Julesc013/abacus-2/hardware/video/video_adapter/CDA Code Pages New.pdf

0 | 1 | 2 | 3 | 4 | 5 | 6 | 7 | 8 | 9 | A | B | C | D | E
0x | Α Β Γ Δ Ε Ζ Η Θ Ι Κ û Μ Ν Ξ
1x | Π Ρ | ⁊ | Σ Τ Υ Φ Χ Ψ Ω ℥ ⟨ ‹ ⟩ ›
2x | | ! | " | # | $ | % | & | ' | ( | ) | * | + | , | - | .
3x | 0 | 1 | 2 | 3 | 4 | 5 | 6 | 7 | 8 | 9 | : | ; | < | = | >
4x | @ | A | B | C | D | E | F | G | H | I | J | K | L | M | N
5x | P | Q | R | S | T | U | V | W | X | Y | Z | [ | \ | ] | ^
6x | ` | a | b | c | d | e | f | g | h | i | j | k | l | m | n
7x | p | q | r | s | t | u | v | w | x | y | z | { | | | } | ~
8x | € | α | β | γ | δ | ε | ζ | η | θ | ι | κ | λ | μ | ν | ξ
9x | π | ρ | ς | σ | τ | υ | φ | χ | ψ | ω | – | — | … | ℠ | ℗
Ax | | ¡ | ¢ | £ | ¤ | ¥ | ¦ | § | ¨ | © | ª | « | ¬ | ™ | ®
Bx | ° ± ² ³ ´ | µ | ¶ · ¸ ¹ º » ¼ ½ ¾
Cx Dx Ex Fx | À Á Â Ã Ä Å Æ Ç È É Ê Ë Ì Í Î Ð Ñ Ò Ó Ô Õ Ö × Ø Ù Ú Û Ü Ý Þ à á â ã ä å æ ç è é ê ë ì í î ð ñ ò ó ô õ ö ÷ ø ù ú û ü ý þ
0x | † ‡ ℹ | ⁎ | ⁑ ⁂ ※ ∓ | ‸ ⁿ ƒ | ⁋ ⁌ ⁍ ‽
1x | ‰ ‱ ′ ″ ‴ ⁗ | ∂ | ∧ ∨ ∩ ∪ ∫ ∬ ∭ | ℇ
2x 3x | ∠ ∡ ∢ ∟ ⊾ ⅈ ⅉ ∈ ∉ ∥ ∦ ∝ ⌐ √ ∛ ≠ ≡ ≢ ≣ ≔ ∴ ∵ ∷ ⋰ ⋱ ⋮ ⋯ ≤ ≈ ≥
4x | ℕ ℤ ℚ A ℝ I ℂ ∞ | ⌀ ∗ ∘ · | ⊕ ⊖ ⊗
5x | ⅐ | ⅑ ⅒ ⅓ | ⅔ | ⅕ | ⅖ | ⅗ | ⅘ | ⅙ | ⅚ | ⅛ | ⅜ | ⅝ | ⅞
6x | ← | ↑ | → | ↓ ↔ | ↕ | ↖ | ↗ | ↘ | ↙ | ⇐ | ⇋ | ⇒ | ⇌ | ⇔
7x | ◄ | ▲ | ► | ▼ | ☺ ☻ | ♥ | ♦ | ♣ | ♠ | ♂ | ♀ | ♪ | ♫ | ☼
8x | 🮀 | 🮁 | 🮂 | 🮃 | 🮄 | 🮅 | 🮆 | 🮇 | 🮈 | 🮉 | 🮊 | 🮋 | 🮌 | 🮍 | 🮎
9x | 🮐 🮑 🮒 | ■ | 🮔 🮕 🮖 🮗 🮘 🮙 🮚 🮛 🮜 🮝 🮞
Ax Bx | ▀ ▁ ▂ ▃ ▄ ▅ ▆ ▇ █ ▉ ▊ ▋ ▌ ▍ ▎ ▐ ░ ▒ ▓ ▔ ▕ ▖ ▗ ▘ ▙ ▚ ▛ ▜ ▝ ▞
Cx | ─ │ ┌ ┐ └ ┘ ├ ┤ ┬ ┴ ┼ | ‣ • ◘ ○
Dx Ex | ═ ║ ╒ ╓ ╔ ╕ ╖ ╗ ╘ ╙ ╚ ╛ ╜ ╝ ╞ ╠ ╡ ╢ ╣ ╤ ╥ ╦ ╧ ╨ ╩ ╪ ╫ ╬ ╭ ╮
Fx | ╰ ╱ ╲ ╳ | ⌠ ⌡ ∎ | ▬ ╸ ╹ ╺ ╻ | ☑ ☐ 🮰

1

Page

0

F | Block | Page | Block
Ο ₧ | Greek Alphabet (Uppercase) | 0 | 0x – 1x 2x – 7x 8x – 9x Ax – Fx

/ ?

O 0x – 3x _ o ⌂ | Latin Alphabet (ASCII) | 1 | 4x – 7x 8x – Cx Dx – Fx
ο № | Greek Alphabet (Lowercase) | 2 | 0x – 7x 8x – Fx
¯ ¿ Ï | Latin Supplement | 3 | 0x – Bx Cx – Dx Ex – Fx

ß ï ÿ

‼
ℯ | General Punctuation &
∜ ≉ ⊘ | Mathematical Operators
⅟ ⇕ | Supplementary Symbols
↨ | Code Page 437 (Leftovers)
🮏 🮟 | Legacy Elements
▏ ▟ | Block Elements

◙
╟ ╯ | Box Drawing

Points | Notes
Miscellaneous Symbols A Latin Alphabet (ASCII) Miscellaneous Symbols B Latin Supplement
Greek Alphabet Cyrillic Alphabet General Punctuation Supplementary Symbols | Arrows, Fractions, Currency, Roman Numerals

Mathematical Operators Box Drawing

Legacy Elements Block Elements Letterlike Symbols | Symbols for Legacy Computing
