Julesc013/abacus-2/hardware/video/video_adapter/CDA Code Pages.pdf

0 | 1 | 2 | 3 | 4 | 5 | 6 | 7 | 8 | 9 | A | B | C | D | E | F | U+ | Block
0x 1x 2x 3x 4x 5x 6x 7x 0 8x 9x Ax Bx Cx Dx Ex Fx | NUL SOH STX ETX EOT ENQ ACK BEL BS HT LF VT FF CR SO SI DLE DC1 DC2 DC3 DC4 NAK SYN ETB CAN EM SUB ESC FS GS RS US | 000x C0 Controls 001x
| SP ! " # $ % & ' ( ) * + , -. / 0 1 2 3 4 5 6 7 8 9 : ; < = > ? @ A B C D E F G H I J K L M N O P Q R S T U V W X Y Z [ \ ] ^ _ ` a b c d e f g h i j k l m n o p q r s t u v w x y z { | } ~ DEL | 002x 003x 004x Basic Latin 005x 006x 007x
| XXX XXX BPH NBH IND NEL SSA ESA HTS HTJ VTS PLD PLU RI SS2 SS3 DCS PU1 PU2 STS CCH MW SPA EPA SOS XXX SCI CSI ST OSC PM APC | 008x C1 Controls 009x
| NBSP ¡ ¢ £ ¤ ¥ ¦ § ¨ © ª « ¬ SHY ® ¯ ° ± ² ³ ´ µ ¶ · ¸ ¹ º » ¼ ½ ¾ ¿ À Á Â Ã Ä Å Æ Ç È É Ê Ë Ì Í Î Ï Ð Ñ Ò Ó Ô Õ Ö × Ø Ù Ú Û Ü Ý Þ ß à á â ã ä å æ ç è é ê ë ì í î ï ð ñ ò ó ô õ ö ÷ ø ù ú û ü ý þ ÿ | 00Ax 00Bx 00Cx Latin-1 Supplement 00Dx 00Ex 00Fx
0x 1x 2x 3x 4x 5x 6x 7x 1 8x 9x Ax Bx Cx Dx Ex Fx | Ѐ Ё Ђ Ѓ Є Ѕ І Ї Ј Љ Њ Ћ Ќ Ѝ Ў Џ А Б В Г Д Е Ж З И Й К Л М Н О П Р С Т У Ф Х Ц Ч Ш Щ Ъ Ы Ь Э Ю Я а б в г д е ж з и й к л м н о п р с т у ф х ц ч ш щ ъ ы ь э ю я ѐ ё ђ ѓ є ѕ і ї ј љ њ ћ ќ ѝ ў џ Ѡ ѡ Ѣ ѣ Ѥ ѥ Ѧ ѧ Ѩ ѩ Ѫ ѫ Ѭ ѭ Ѯ ѯ Ѱ ѱ Ѳ ѳ Ѵ ѵ Ѷ ѷ Ѹ ѹ Ѻ ѻ Ѽ ѽ Ѿ ѿ | 040x 041x 042x 043x Cyrillic 044x 045x 046x 047x
| ΄ ΅ Ά · Έ Ή Ί Ό Ύ Ώ ΐ Α Β Γ Δ Ε Ζ Η Θ Ι Κ Λ Μ Ν Ξ Ο Π Ρ Σ Τ Υ Φ Χ Ψ Ω Ϊ Ϋ ά έ ή ί ΰ α β γ δ ε ζ η θ ι κ λ μ ν ξ ο π ρ ς σ τ υ φ χ ψ ω ϊ ϋ ό ύ ώ Ϗ ϐ ϑ ϒ ϓ ϔ ϕ ϖ ϗ Ϙ ϙ Ϛ ϛ Ϝ ϝ Ϟ ϟ Ϡ ϡ Ϣ ϣ Ϥ ϥ Ϧ ϧ Ϩ ϩ Ϫ ϫ Ϭ ϭ Ϯ ϯ ϰ ϱ ϲ ϳ ϴ ϵ ϶ Ϸ ϸ Ϲ Ϻ ϻ ϼ Ͻ Ͼ Ͽ | 038x 039x 03Ax 03Bx Greek and Coptic 03Cx 03Dx 03Ex 03Fx
0x 1x 2x 3x 4x 5x 6x 7x 2 8x 9x Ax Bx Cx Dx Ex Fx | IDSP 、 。 〃 〄 々 〆 〇 〈 〉 《 》 「 」 『 』 【 】 〒 〓 〔 〕 〖 〗 〘 〙 〚 〛 〜 〝 〞 〟 〠 〡 〢 〣 〤 〥 〦 〧 〨 〩 〪 〫 〬 〭 〮 〯 〰 〱 〲 〳 〴 〵 〶 〷 〸 〹 〺 〻 〼 〽 〾 〿 | 300x 301x CJK Symbols and Punctuation 302x 303x
| ぁ あ ぃ い ぅ う ぇ え ぉ お か が き ぎ く ぐ け げ こ ご さ ざ し じ す ず せ ぜ そ ぞ た だ ち ぢ っ つ づ て で と ど な に ぬ ね の は ば ぱ ひ び ぴ ふ ぶ ぷ へ べ ぺ ほ ぼ ぽ ま み む め も ゃ や ゅ ゆ ょ よ ら り る れ ろ ゎ わ ゐ ゑ を ん ゔ ゕ ゖ ゙◌ ゚◌ ゛ ゜ ゝ ゞ ゟ | 304x 305x 306x Hiragana 307x 308x 309x
| ゠ ァ ア ィ イ ゥ ウ ェ エ ォ オ カ ガ キ ギ ク グ ケ ゲ コ ゴ サ ザ シ ジ ス ズ セ ゼ ソ ゾ タ ダ チ ヂ ッ ツ ヅ テ デ ト ド ナ ニ ヌ ネ ノ ハ バ パ ヒ ビ ピ フ ブ プ ヘ ベ ペ ホ ボ ポ マ ミ ム メ モ ャ ヤ ュ ユ ョ ヨ ラ リ ル レ ロ ヮ ワ ヰ ヱ ヲ ン ヴ ヵ ヶ ヷ ヸ ヹ ヺ ・ ー ヽ ヾ ヿ | 30Ax 30Bx 30Cx Katakana 30Dx 30Ex 30Fx
0x 1x 2x 3x 4x 5x 6x 7x 3 8x 9x Ax Bx Cx Dx Ex Fx | ─ ━ │ ┃ ┄ ┅ ┆ ┇ ┈ ┉ ┊ ┋ ┌ ┍ ┎ ┏ ┐ ┑ ┒ ┓ └ ┕ ┖ ┗ ┘ ┙ ┚ ┛ ├ ┝ ┞ ┟ ┠ ┡ ┢ ┣ ┤ ┥ ┦ ┧ ┨ ┩ ┪ ┫ ┬ ┭ ┮ ┯ ┰ ┱ ┲ ┳ ┴ ┵ ┶ ┷ ┸ ┹ ┺ ┻ ┼ ┽ ┾ ┿ ╀ ╁ ╂ ╃ ╄ ╅ ╆ ╇ ╈ ╉ ╊ ╋ ╌ ╍ ╎ ╏ ═ ║ ╒ ╓ ╔ ╕ ╖ ╗ ╘ ╙ ╚ ╛ ╜ ╝ ╞ ╟ ╠ ╡ ╢ ╣ ╤ ╥ ╦ ╧ ╨ ╩ ╪ ╫ ╬ ╭ ╮ ╯ ╰ ╱ ╲ ╳ ╴ ╵ ╶ ╷ ╸ ╹ ╺ ╻ ╼ ╽ ╾ ╿ | 250x 251x 252x 253x Box Drawing 254x 255x 256x 257x
| ▀ ▁ ▂ ▃ ▄ ▅ ▆ ▇ █ ▉ ▊ ▋ ▌ ▍ ▎ ▏ ▐ ░ ▒ ▓ ▔ ▕ ▖ ▖ ▖ ▖ ▖ ▖ ▖ ▖ ▖ ▖ | 258x Block Elements 259x
| ■ □ ▢ ▣ ▤ ▥ ▦ ▧ ▨ ▩ ▪ ▫ ▬ ▭ ▮ ▯ ▰ ▱ ▲ △ ▴ ▵ ▶ ▷ ▸ ▹ ► ▻ ▼ ▽ ▾ ▿ ◀ ◁ ◂ ◃ ◄ ◅ ◆ ◇ ◈ ◉ ◊ ○ ◌ ◍ ◎ ● ◐ ◑ ◒ ◓ ◔ ◕ ◖ ◗ ◘ ◙ ◚ ◛ ◜ ◝ ◞ ◟ ◠ ◡ ◢ ◣ ◤ ◥ ◦ ◧ ◨ ◩ ◪ ◫ ◬ ◭ ◮ ◯ ◰ ◱ ◲ ◳ ◴ ◵ ◶ ◷ ◸ ◹ ◺ ◻ ◼ ◽ ◾ ◿ | 25Ax 25Bx 25Cx Geometric Shapes 25Dx 25Ex 25Fx

Page

0x 1x 2x 3x 4x 5x 6x 7x 4 8x 9x Ax Bx Cx Dx Ex Fx | NQSP MQSP ENSP EMSP 3/MSP 4/MSP 6/MSP FSP PSP THSP HSP ZWSP ZWNJ ZW J LRM RLM -NB ‒ – — ― ‖ ‗ ‘ ’ ‚ ‛ “ ” „ ‟ † ‡ • ‣ ․ ‥ … ‧ LSEP PSEP LRE RLE PDF LRO RLO NNBSP ‰ ‱ ′ ″ ‴ ‵ ‶ ‷ ‸ ‹ › ※ ‼ ‽ ‾ ‿ ⁀ ⁁ ⁂ ⁃ ⁄ ⁅ ⁆ ⁇ ⁈ ⁉ ⁊ ⁋ ⁌ ⁍ ⁎ ⁏ ⁐ ⁑ ⁒ ⁓ ⁔ ⁕ ⁖ ⁗ ⁘ ⁙ ⁚ ⁛ ⁜ ⁝ ⁞ MMSP WJ ƒ() × , + LRI RLI FSI PDI ISS ASS IAFS AAFS NADS NODS | 200x 201x 202x 203x General Punctuation 204x 205x 206x
| ▖ ▖ ▖ ▖ ▖ ▖ ▖ ▖ ▖ ▖ ▖ | 244x Optical Character Recognition
| ⸀ ⸁ ⸂ ⸃ ⸄ ⸅ ⸆ ⸇ ⸈ ⸉ ⸊ ⸋ ⸌ ⸍ ⸎ ⸒ ⸓ ⸔ ⸕ ⸖ ⸗ ⸘ ⸙ ⸚ ⸛ ⸜ ⸝ ⸞ ⸟ ⸠ ⸡ ⸢ ⸣ ⸤ ⸥ ⸦ ⸧ ⸨ ⸩ ⸪ ⸫ ⸬ ⸭ ⸮ ⸯ ⸰ ⸱ ⸲ ⸳ ⸴ ⸵ ⸶ ⸷ ⸸ ⸹ 2M⸺ 3M⸻ ⸼ ⸽ ⸾ ⸿ ⹀ ⹁ ⹂ ⹃ ⹄ ⹅ ⹅ ⹅ ⹅ ⹅ ⹅ ⹅ ⹅ ⹅ ⹅ ⹅ ▖ ▖ ▖ ▖ ▖ ▖ ▖ ▖ ▖ ▖ ▖ ▖ ▖ ▖ | 2E0x 2E1x 2E2x Supplemental Punctuation 2E3x 2E4x 2E5x
0x | ℀ | ℁ | ℂ | ℃ | ℄ | ℅ | ℆ | ℇ | ℈ | ℉ | ℊ | ℋ | ℌ | ℍ | ℎ | ℏ | 210x
1x | ℐ | ℑ | ℒ | ℓ | ℔ | ℕ | № | ℗ | ℘ | ℙ | ℚ | ℛ | ℜ | ℝ | ℞ | ℟ | 211x
2x | ℠ | ℡ | ™ | ℣ | ℤ | ℥ | Ω | ℧ | ℨ | ℩ | K | Å | ℬ | ℭ | ℮ | ℯ | 212x
3x | ℰ | ℱ | Ⅎ | ℳ | ℴ | ℵ | ℶ | ℷ | ℸ | ℹ | ℺ | ℻ | ℼ | ℽ | ℾ | ℿ | 213x
4x | ⅀ | ⅁ | ⅂ | ⅃ | ⅄ | ⅅ | ⅆ | ⅇ | ⅈ | ⅉ | ⅊ | ⅋ | ⅌ | ⅍ | ⅎ | ⅏ | 214x
5x | ⅐ | ⅑ ⅒ | ⅓ | ⅔ | ⅕ | ⅖ | ⅗ | ⅘ | ⅙ | ⅚ | ⅛ | ⅜ | ⅝ | ⅞ | ⅟ | 215x
6x | Ⅰ | Ⅱ | Ⅲ | Ⅳ | Ⅴ | Ⅵ | Ⅶ | Ⅷ | Ⅸ | Ⅹ | Ⅺ | Ⅻ | Ⅼ | Ⅽ | Ⅾ | Ⅿ | 216x
7x | ⅰ | ⅱ | ⅲ | ⅳ | ⅴ | ⅵ | ⅶ | ⅷ | ⅸ | ⅹ | ⅺ | ⅻ | ⅼ | ⅽ | ⅾ | ⅿ | 217x
8x | ↀ | ↁ | ↂ | Ↄ | ↄ | ↅ | ↆ | ↇ | ↈ | ↉ | ↊ | ↋ | | | | | 218x
9x
Ax | ₠ | ₡ | ₢ | ₣ | ₤ | ₥ | ₦ | ₧ | ₨ | ₩ | ₪ | ₫ | € | ₭ | ₮ | ₯ | 20Ax
Bx | ₰ | ₱ | ₲ | ₳ | ₴ | ₵ | ₶ | ₷ | ₸ | ₹ | ₺ | ₻ | ₼ | ₽ | ₾ | ₿ | 20Bx
Cx
Dx
Ex
Fx
0x 1x 2x 3x 4x 5x 6x 7x 6 Mathematical Operators 8x 9x Ax Bx Cx Dx Ex Fx | ∀ ∁ ∂ ∃ ∄ ∅ ∆ ∇ ∈ ∉ ∊ ∋ ∌ ∍ ∎ ∏ ∐ ∑ − ∓ ∔ ∕ ∖ ∗ ∘ · √ ∛ ∜ ∝ ∞ ∟ ∠ ∡ ∢ ∣ ∤ ∥ ∦ ∧ ∨ ∩ ∪ ∫ ∬ ∭ ∮ ∯ ∰ ∱ ∲ ∳ ∴ ∵ ∶ ∷ ∸ ∹ ∺ ∻ ∼ ∽ ∾ ∿ ≀ ≁ ≂ ≃ ≄ ≅ ≆ ≇ ≈ ≉ ≊ ≋ ≌ ≍ ≎ ≏ ≐ ≑ ≒ ≓ ≔ ≕ ≖ ≗ ≘ ≙ ≚ ≛ ≜ ≝ ≞ ≟ ≠ ≡ ≢ ≣ ≤ ≥ ≦ ≧ ≨ ≩ ≪ ≫ ≬ ≭ ≮ ≯ ≰ ≱ ≲ ≳ ≴ ≵ ≶ ≷ ≸ ≹ ≺ ≻ ≼ ≽ ≾ ≿ ⊀ ⊁ ⊂ ⊃ ⊄ ⊅ ⊆ ⊇ ⊈ ⊉ ⊊ ⊋ ⊌ ⊍ ⊎ ⊏ ⊐ ⊑ ⊒ ⊓ ⊔ ⊕ ⊖ ⊗ ⊘ ⊙ ⊚ ⊛ ⊜ ⊝ ⊞ ⊟ ⊠ ⊡ ⊢ ⊣ ⊤ ⊥ ⊦ ⊧ ⊨ ⊩ ⊪ ⊫ ⊬ ⊭ ⊮ ⊯ ⊰ ⊱ ⊲ ⊳ ⊴ ⊵ ⊶ ⊷ ⊸ ⊹ ⊺ ⊻ ⊼ ⊽ ⊾ ⊿ ⋀ ⋁ ⋂ ⋃ ⋄ ⋅ ⋆ ⋇ ⋈ ⋉ ⋊ ⋋ ⋌ ⋍ ⋎ ⋏ ⋐ ⋑ ⋒ ⋓ ⋔ ⋕ ⋖ ⋗ ⋘ ⋙ ⋚ ⋛ ⋜ ⋝ ⋞ ⋟ ⋠ ⋡ ⋢ ⋣ ⋤ ⋥ ⋦ ⋧ ⋨ ⋩ ⋪ ⋫ ⋬ ⋭ ⋮ ⋯ ⋰ ⋱ ⋲ ⋳ ⋴ ⋵ ⋶ ⋷ ⋸ ⋹ ⋺ ⋻ ⋼ ⋽ ⋾ ⋿ | 220x 221x 222x 223x 224x 225x 226x 227x 228x 229x 22Ax 22Bx 22Cx 22Dx 22Ex 22Fx
0x 1x 2x 3x 4x 5x 6x 7x 7 8x 9x Ax Bx Cx Dx Ex Fx | 🬀 🬁 🬂 🬃 🬄 🬅 🬆 🬇 🬈 🬉 🬊 🬋 🬌 🬍 🬎 🬏 🬐 🬑 🬒 🬓 🬔 🬕 🬖 🬗 🬘 🬙 🬚 🬛 🬜 🬝 🬞 🬟 🬠 🬡 🬢 🬣 🬤 🬥 🬦 🬧 🬨 🬩 🬪 🬫 🬬 🬭 🬮 🬯 🬰 🬱 🬲 🬳 🬴 🬵 🬶 🬷 🬸 🬹 🬺 🬻 🬼 🬽 🬾 🬿 🭀 🭁 🭂 🭃 🭄 🭅 🭆 🭇 🭈 🭉 🭊 🭋 🭌 🭍 🭎 🭏 🭐 🭑 🭒 🭓 🭔 🭕 🭖 🭗 🭘 🭙 🭚 🭛 🭜 🭝 🭞 🭟 🭠 🭡 🭢 🭣 🭤 🭥 🭦 🭧 🭨 🭩 🭪 🭫 🭬 🭭 🭮 🭯 🭰 🭱 🭲 🭳 🭴 🭵 🭶 🭷 🭸 🭹 🭺 🭻 🭼 🭽 🭾 🭿 🮀 🮁 🮂 🮃 🮄 🮅 🮆 🮇 🮈 🮉 🮊 🮋 🮌 🮍 🮎 🮏 🮐 🮑 🮒 🮔 🮕 🮖 🮗 🮘 🮙 🮚 🮛 🮜 🮝 🮞 🮟 🮠 🮡 🮢 🮣 🮤 🮥 🮦 🮧 🮨 🮩 🮪 🮫 🮬 🮭 🮮 🮯 🮰 🮱 🮲 🮳 🮴 🮵 🮶 🮷 🮸 🮹 🮺 🮻 🮼 🮽 🮾 🮿 🯀 🯁 🯂 🯃 🯄 🯅 🯆 🯇 🯈 🯉 🯊 | 1FB0x 1FB1x 1FB2x 1FB3x 1FB4x 1FB5x 1FB6x Symbols for Legacy Computing 1FB7x 1FB8x 1FB9x 1FBAx 1FBBx 1FBCx
| 🜀 🜁 🜂 🜃 🜄 🜅 🜆 🜇 🜈 🜉 🜊 🜋 🜌 🜍 🜎 🜏 🜐 🜑 🜒 🜓 🜔 🜕 🜖 🜗 🜘 🜙 🜚 🜛 🜜 🜝 🜞 🜟 | 1F70x Alchemical Symbols 1F71x
| 🯰 🯱 🯲 🯳 🯴 🯵 🯶 🯷 🯸 🯹 | 1FBFx Symbols for Legacy Computing

5

Letterlike Symbols

Number Forms

Currency Symbols

0x 1x 2x 3x 4x 5x 6x 7x 8 8x 9x Ax Bx Cx Dx Ex Fx | SP ! " # $ % & ' ( ) * + , -. / 0 1 2 3 4 5 6 7 8 9 : ; < = > ? @ A B C D E F G H I J K L M N O P Q R S T U V W X Y Z [ \ ] ^ _ ` a b c d e f g h i j k l m n o p q r s t u v w x y z { | } ~ ± § α β γ δ ε ζ η θ ι κ λ μ ν ξ ο π ρ ς σ τ υ φ χ ψ ω Δ Θ Ξ Π Σ Ω | N/A N/A N/A N/A Superscript Symbols N/A N/A N/A N/A
| SP ! " # $ % & ' ( ) * + , -. / 0 1 2 3 4 5 6 7 8 9 : ; < = > ? @ A B C D E F G H I J K L M N O P Q R S T U V W X Y Z [ \ ] ^ _ ` a b c d e f g h i j k l m n o p q r s t u v w x y z { | } ~ ± § α β γ δ ε ζ η θ ι κ λ μ ν ξ ο π ρ ς σ τ υ φ χ ψ ω Δ Θ Ξ Π Σ Ω | N/A N/A N/A N/A Subscript Symbols N/A N/A N/A N/A
| | Miscellaneous Mathematical Symbols-B
| | Miscellaneous Mathematical Symbols-A
| | Arrows
| | Miscellaneous Symbols and Arrows
| | Miscellaneous Symbols
0x 1x 2x 3x 4x 5x 6x 7x B Miscellaneous Technical 8x 9x Ax Bx Cx Dx Ex Fx | ⌀ ⌁ ⌂ ⌃ ⌄ ⌅ ⌆ ⌇ ⌈ ⌉ ⌊ ⌋ ⌌ ⌍ ⌎ ⌏ ⌐ ⌑ ⌒ ⌓ ⌔ ⌕ ⌖ ⌗ ⌘ ⌙ ⌚ ⌛ ⌜ ⌝ ⌞ ⌟ ⌠ ⌡ ⌢ ⌣ ⌤ ⌥ ⌦ ⌧ ⌨ 〈 〉 ▖ ▖ ▖ ▖ ▖ ⌰ ⌱ ⌲ ⌳ ⌴ ⌵ ⌶ ⌷ ⌸ ⌹ ⌺ ⌻ ⌼ ⌽ ⌾ ⌿ ⍀ ⍁ ⍂ ⍃ ⍄ ⍅ ⍆ ⍇ ⍈ ⍉ ⍊ ⍋ ⍌ ⍍ ⍎ ⍏ ⍐ ⍑ ⍒ ⍓ ⍔ ⍕ ⍖ ⍗ ⍘ ⍙ ⍚ ⍛ ⍜ ⍝ ⍞ ⍟ ⍠ ⍡ ⍢ ⍣ ⍤ ⍥ ⍦ ⍧ ⍨ ⍩ ⍪ ⍫ ⍬ ⍭ ⍮ ⍯ ⍰ ⍱ ⍲ ⍳ ⍴ ⍵ ⍶ ⍷ ⍸ ⍹ ⍺ ⍻ ⍼ ⍽ ⍾ ⍿ ⎀ ⎐ ⎁ ⎑ ⎂ ⎒ ⎃ ⎓ ⎄ ⎔ ⎕ ⎅ ⎆ ⎖ ⎇ ⎗ ⎘ ⎈ ⎙ ⎉ ⎚ ⎊ ⎛ ⎜ ⎝ ⎞ ⎟ ⎋ ⎌ ⎍ ⎎ ⎏ ⎠ ⎡ ⎢ ⎣ ⎤ ⎥ ⎦ ⎧ ⎨ ⎩ ⎪ ⎫ ⎬ ⎭ ⎮ ⎯ ⎰ ⎱ ⎲ ⎳ ⎴ ⎵ ⎶ ⎷ ⎸ ⎹ ⎺ ⎻ ⎼ ⎽ ⎾ ⎿ ⏀ ⏁ ⏂ ⏃ ⏄ ⏅ ⏆ ⏇ ⏈ ⏉ ⏊ ⏋ ⏌ ⏍ ⏎ ⏏ ▖ ▖ ▖ ▖ ▖ ▖ ▖ ▖ ▖ ▖ ⏚ ⏛ ⏜ ⏝ ⏞ ⏟ ⏠ ▖ ▖ ▖ ▖ ▖ ▖ ▖ ▖ ⏩ ⏪ ⏫ ⏬ ⏭ ⏮ ⏯ ⏰ ⏱ ⏲ ⏳ ▖ ▖ ▖ ▖ ⏸ ⏹ ⏺ ▖ ▖ ▖ ▖ ▖ | 230x 231x 232x 233x 234x 235x 236x 237x 238x 239x 23Ax 23Bx 23Cx 23Dx 23Ex 23Fx
0x | ⦀ | ⦁ | ⦂ | ⦃ | ⦄ | ⦅ | ⦆ | ⦇ | ⦈ | ⦉ | ⦊ | ⦋ | ⦌ | ⦍ | ⦎ | ⦏ | 298x
1x | ⦐ | ⦑ | ⦒ | ⦓ | ⦔ | ⦕ | ⦖ | ⦗ | ⦘ | ⦙ | ⦚ | ⦛ | ⦜ | ⦝ | ⦞ | ⦟ | 299x
2x | ⦠ | ⦡ | ⦢ | ⦣ | ⦤ | ⦥ | ⦦ | ⦧ | ⦨ | ⦩ | ⦪ | ⦫ | ⦬ | ⦭ | ⦮ | ⦯ | 29Ax
3x | ⦰ | ⦱ | ⦲ ⦳ ⦴ ⦵ | ⦶ | ⦷ | ⦸ | ⦹ | ⦺ | ⦻ | ⦼ | ⦽ ⦾ | ⦿ | 29Bx
4x | ⧀ | ⧁ | ⧂ ⧃ | ⧄ | ⧅ | ⧆ | ⧇ | ⧈ | ⧉ | ⧊ | ⧋ | ⧌ | ⧍ | ⧎ | ⧏ | 29Cx
5x | ⧐ | ⧑ | ⧒ | ⧓ | ⧔ | ⧕ | ⧖ | ⧗ | ⧘ | ⧙ | ⧚ | ⧛ | ⧜ | ⧝ | ⧞ | ⧟ | 29Dx
6x | ⧠ | ⧡ | ⧢ | ⧣ | ⧤ | ⧥ | ⧦ | ⧧ | ⧨ | ⧩ | ⧪ | ⧫ | ⧬ | ⧭ | ⧮ | ⧯ | 29Ex
7x | ⧰ | ⧱ | ⧲ | ⧳ | ⧴ | ⧵ | ⧶ | ⧷ | ⧸ ⧹ ⧺ | ⧻ | ⧼ | ⧽ | ⧾ | ⧿ | 29Fx
8x | ⟀ | ⟁ | ⟂ | ⟃ | ⟄ | ⟅ | ⟆ | ⟇ | ⟈ | ⟉ | ⟊ | ⟋ | ⟌ | ⟍ | ⟎ | ⟏ | 27Cx
9x | ⟐ | ⟑ | ⟒ | ⟓ | ⟔ | ⟕ | ⟖ | ⟗ | ⟘ | ⟙ | ⟚ ⟛ | ⟜ | ⟝ | ⟞ | ⟟ | 27Dx
Ax | ⟠ | ⟡ | ⟢ | ⟣ | ⟤ | ⟥ | ⟦ | ⟧ | ⟨ | ⟩ | ⟪ | ⟫ | ⟬ | ⟭ | ⟮ | ⟯ | 27Ex
Bx | ← ↑ → ↓ ↔ ↕ | ↖ ↗ ↘ ↙ ↚ | ↛ | ↜ | ↝ | ↞ | ↟ | 219x
Cx | ↠ | ↡ | ↢ | ↣ | ↤ | ↥ | ↦ | ↧ | ↨ | ↩ | ↪ | ↫ | ↬ | ↭ | ↮ | ↯ | 21Ax
Dx | ↰ | ↱ | ↲ | ↳ | ↴ | ↵ | ↶ | ↷ | ↸ | ↹ | ↺ | ↻ | ↼ | ↽ | ↾ | ↿ | 21Bx
Ex | ⇀ | ⇁ | ⇂ | ⇃ | ⇄ | ⇅ | ⇆ | ⇇ | ⇈ | ⇉ | ⇊ | ⇋ | ⇌ | ⇍ | ⇎ | ⇏ | 21Cx
Fx | ⇐ | ⇑ | ⇒ | ⇓ | ⇔ | ⇕ | ⇖ | ⇗ | ⇘ | ⇙ | ⇚ | ⇛ | ⇜ | ⇝ | ⇞ | ⇟ | 21Dx
0x | ⬀ ⬁ ⬂ ⬃ ⬄ | ⬅ ⬆ | ⬇ | ⬈ ⬉ ⬊ ⬋ ⬌ | ⬍ | ⬎ ⬏ | 2B0x
1x | ⬐ ⬑ ⬒ ⬓ ⬔ ⬕ ⬖ ⬗ ⬘ ⬙ ⬚ ⬛ ⬜ ⬝ | ⬞ | ⬟ | 2B1x
2x | ⬠ ⬡ ⬢ ⬣ ⬤ ⬥ ⬦ ⬧ ⬨ | ⬩ | ⬪ | ⬫ | ⬬ ⬭ ⬮ ⬯ | 2B2x
3x | ⬰ ⬱ ⬲ ⬳ ⬴ ⬵ ⬶ ⬷ ⬸ ⬹ ⬺ ⬻ ⬼ ⬽ ⬾ ⬿ | 2B3x
4x | ⭀ ⭁ ⭂ ⭃ ⭄ ⭅ ⭆ ⭇ ⭈ ⭉ ⭊ ⭋ ⭌ | ⭍ ⭎ | ⭏ | 2B4x
5x | ⭐ ⭑ | ⭒ | ⭓ ⭔ ⭕ ⭖ ⭗ ⭘ ⭙ ⭚ | ⭛ ⭜ ⭝ ⭞ | ⭟ | 2B5x
6x | ⭠ ⭡ ⭢ ⭣ | ⭤ ⭥ | ⭦ | ⭧ | ⭨ | ⭩ | ⭪ ⭫ | ⭬ ⭭ ⭮ ⭯ | 2B6x
7x | ⭰ ⭱ ⭲ ⭳ | ⭶ ⭷ ⭸ ⭹ ⭺ | ⭻ | ⭼ | ⭽ ⭾ ⭿ | 2B7x
8x | ☀ ☁ ☂ ☃ ☄ ★ ☆ | ☇ | ☈ ☉ ☊ ☋ | ☌ | ☍ ☎ ☏ | 260x
9x | ☐ ☑ ☒ ☓ ☔ ☕ ☖ ☗ ☘ ☙ ☚ ☛ ☜ | ☝ | ☞ | ☟ | 261x
Ax | ☠ ☡ ☢ ☣ | ☤ | ☥ | ☦ | ☧ | ☨ ☩ ☪ ☫ ☬ ☭ ☮ ☯ | 262x
Bx | ☰ ☱ ☲ ☳ ☴ ☵ ☶ ☷ ☸ ☹ ☺ ☻ ☼ ☽ | ☾ | ☿ | 263x
Cx | ♀ | ♁ | ♂ ♃ | ♄ | ♅ ♆ | ♇ ♈ ♉ ♊ ♋ ♌ ♍ ♎ ♏ | 264x
Dx | ♐ ♑ ♒ ♓ ♔ ♕ ♖ ♗ ♘ ♙ ♚ ♛ ♜ ♝ ♞ ♟ | 265x
Ex | ♠ | ♡ | ♢ | ♣ | ♤ | ♥ | ♦ | ♧ ♨ | ♩ | ♪ | ♫ ♬ | ♭ | ♮ | ♯ | 266x
Fx | ♰ | ♱ ♲ ♳ ♴ ♵ ♶ ♷ ♸ ♹ ♺ ♻ ♼ ♽ ♾ ♿ | 267x

9

A

0x 1x 2x 3x 4x 5x 6x 7x C Allocated for User Definition 8x 9x Ax Bx Cx Dx Ex Fx | N/A N/A N/A N/A N/A N/A N/A N/A N/A N/A N/A N/A N/A N/A N/A N/A
0x 1x 2x 3x 4x 5x 6x 7x D Allocated for User Definition 8x 9x Ax Bx Cx Dx Ex Fx | N/A N/A N/A N/A N/A N/A N/A N/A N/A N/A N/A N/A N/A N/A N/A N/A
0x 1x 2x 3x 4x 5x 6x 7x E Allocated for User Definition 8x 9x Ax Bx Cx Dx Ex Fx | N/A N/A N/A N/A N/A N/A N/A N/A N/A N/A N/A N/A N/A N/A N/A N/A
0x 1x 2x 3x 4x 5x 6x 7x F Allocated for User Definition 8x 9x Ax Bx Cx Dx Ex Fx | N/A N/A N/A N/A N/A N/A N/A N/A N/A N/A N/A N/A N/A N/A N/A N/A
