Julesc013/abacus-2/hardware/case/s01.JPG

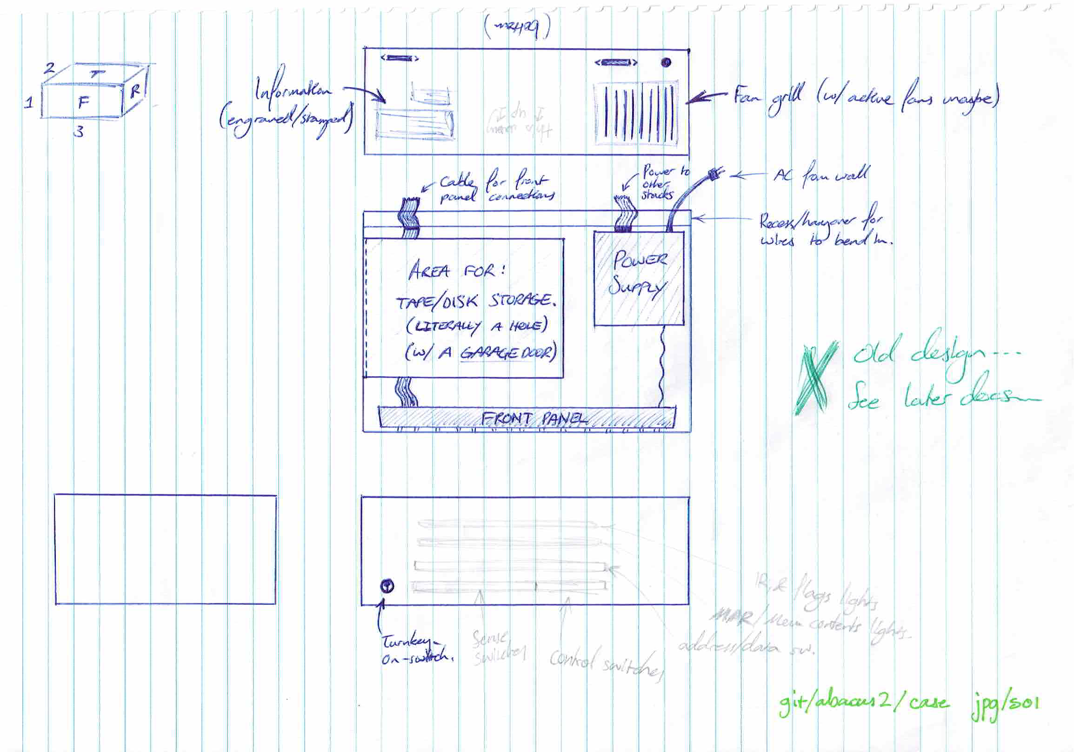
hardware/case/s01.JPG
