Julesc013/abacus-2/hardware/case/s02.JPG

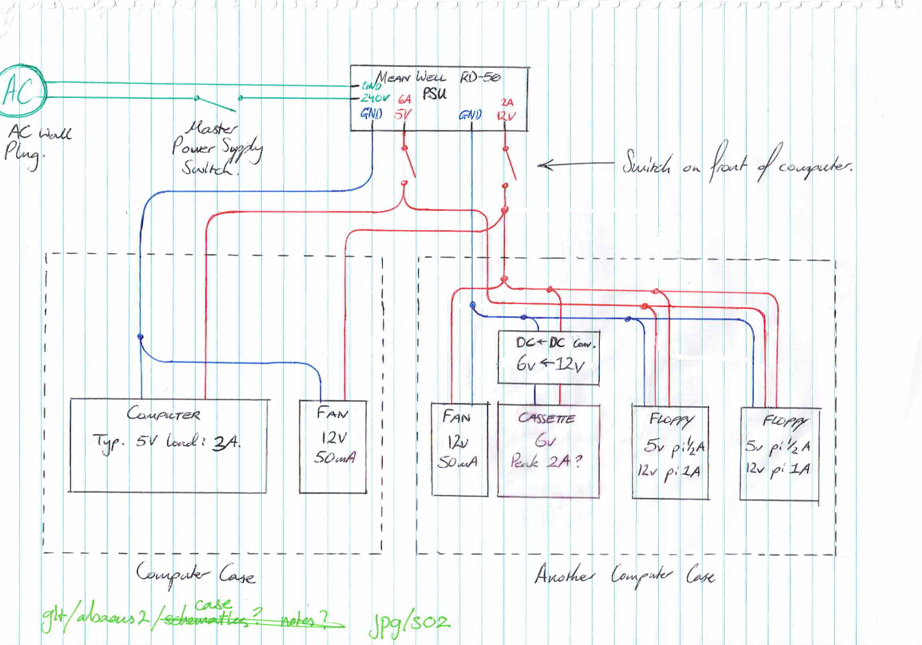
hardware/case/s02.JPG
