Julesc013/abacus-2/hardware/chipset/c04.JPG

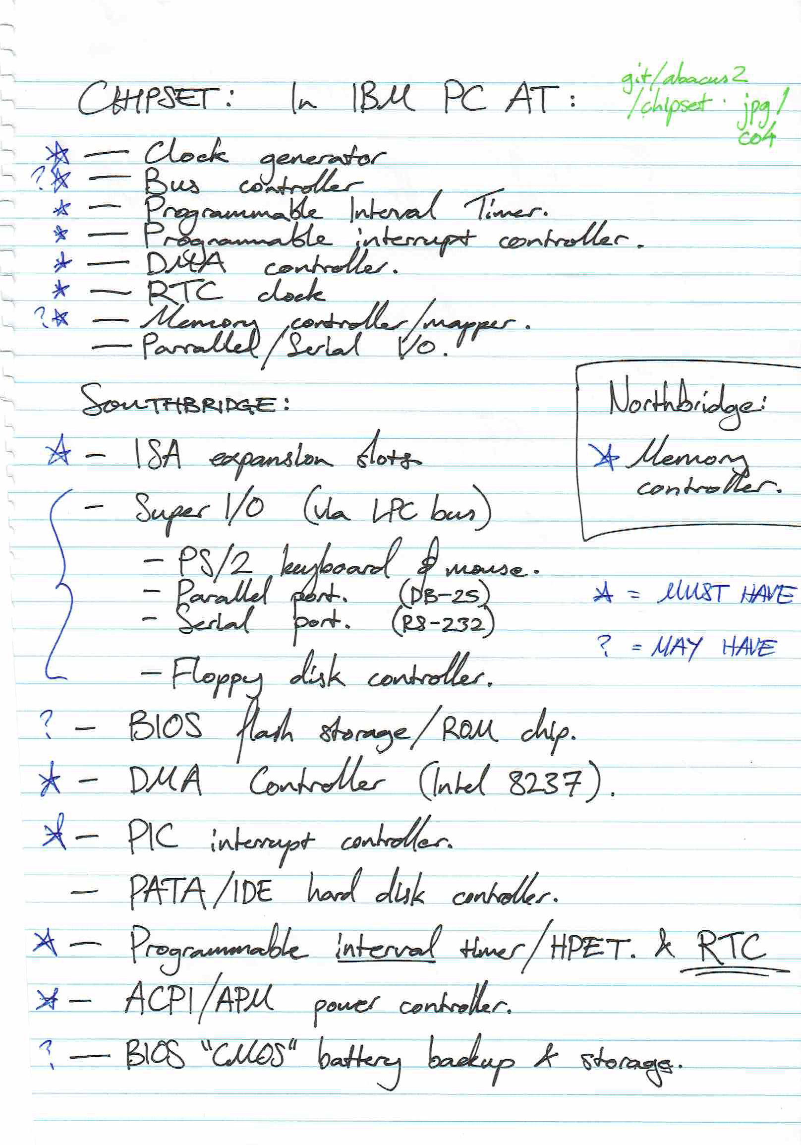
hardware/chipset/c04.JPG
