Julesc013/abacus-2/hardware/interrupts/i04.JPG

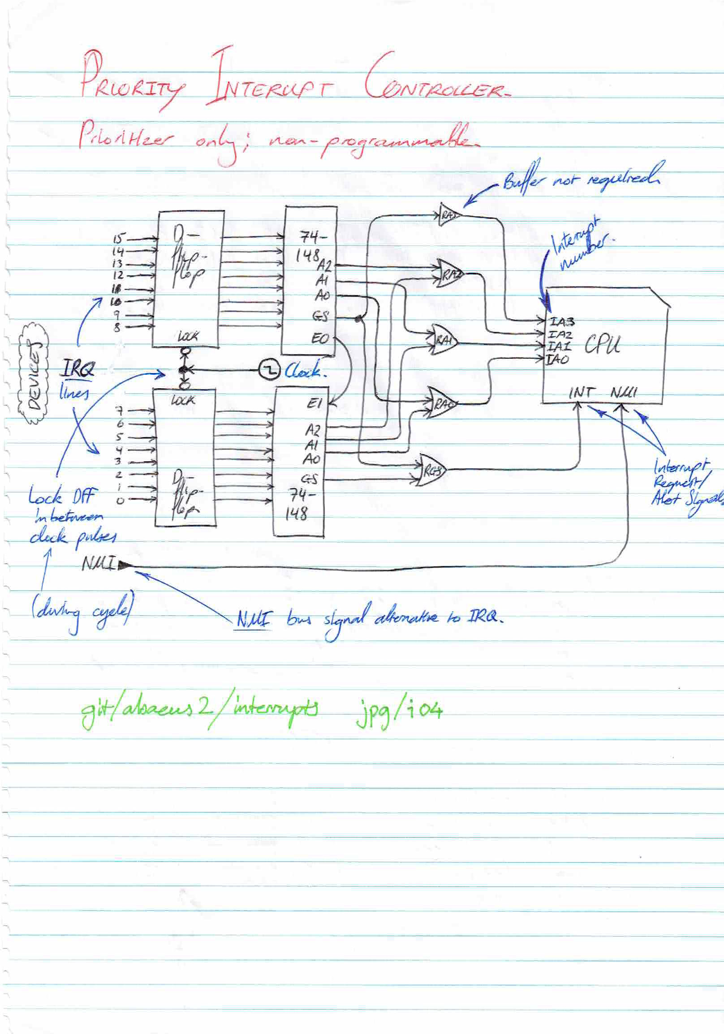
hardware/interrupts/i04.JPG
