Julesc013/abacus-2/hardware/interrupts/v01.JPG

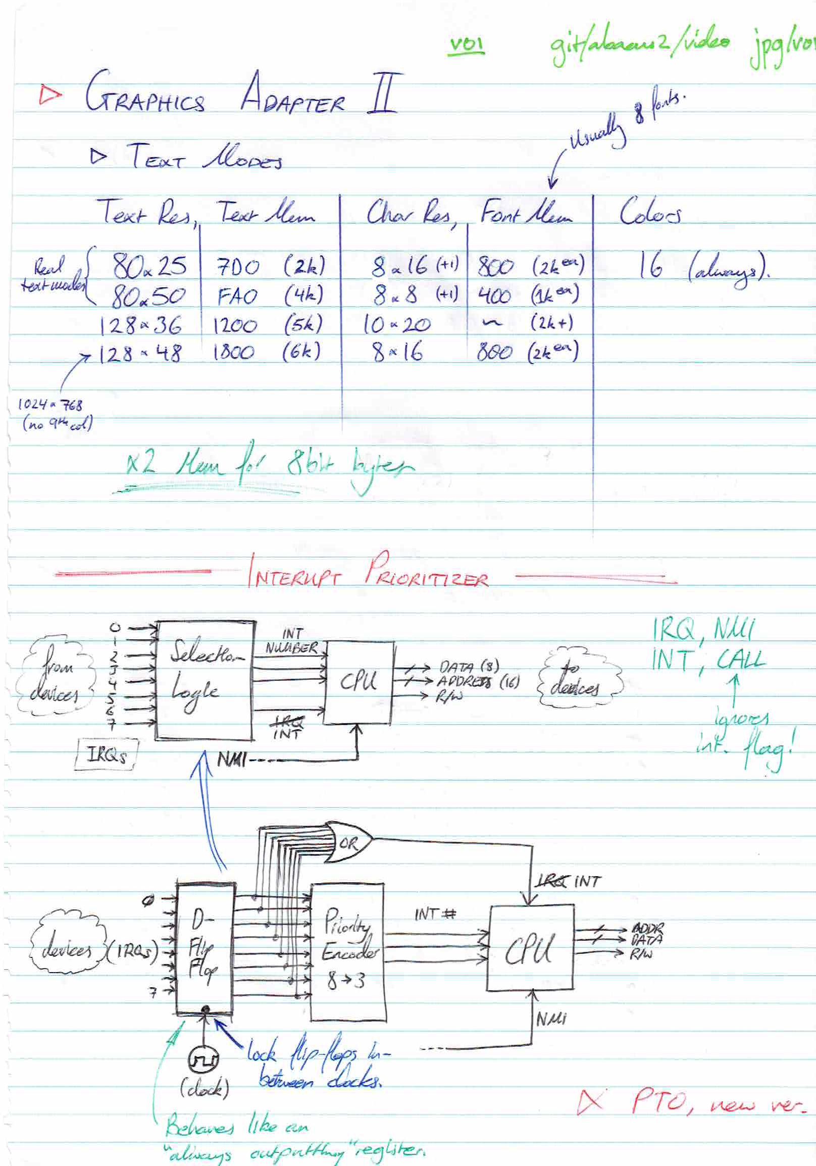
hardware/interrupts/v01.JPG
