Julesc013/abacus-2/hardware/memory/Memory Map 5V.png

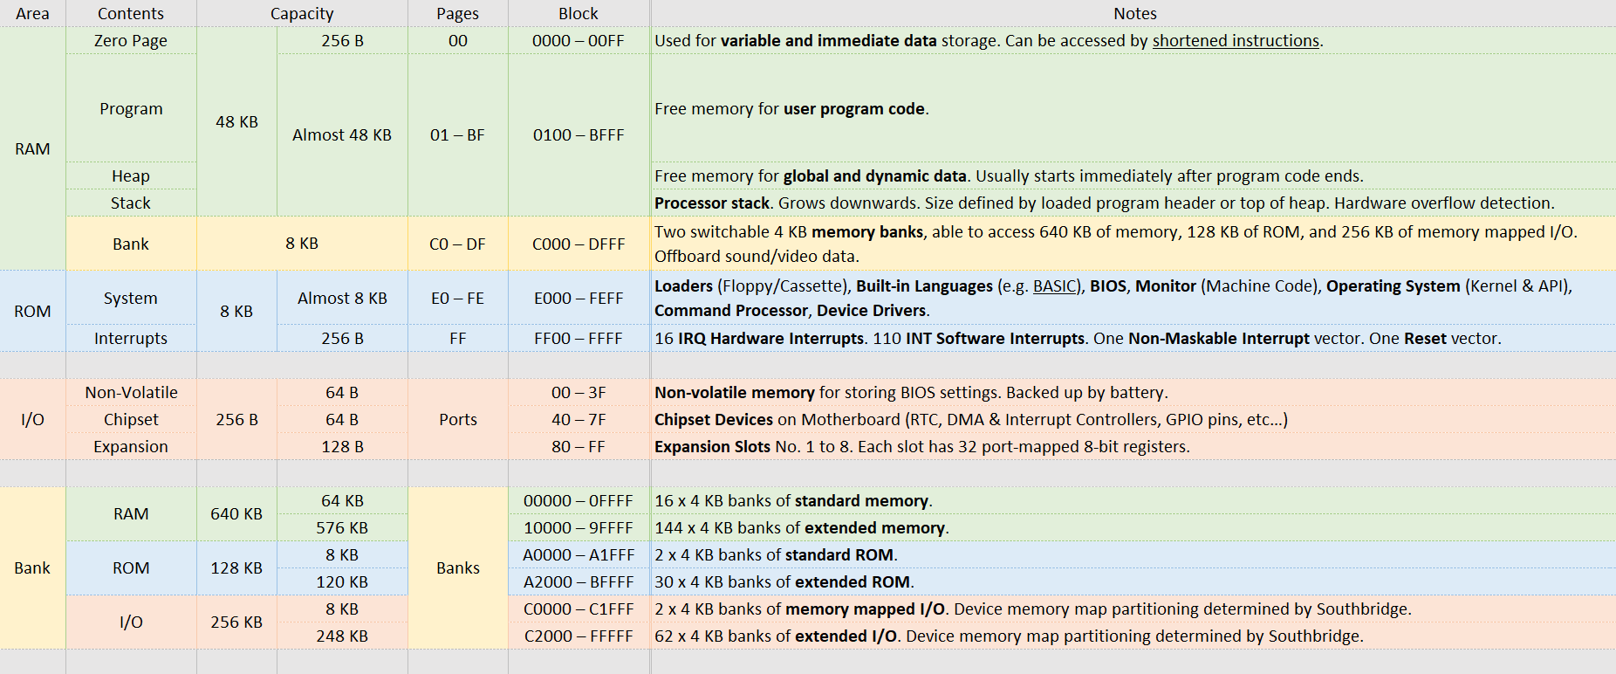
hardware/memory/Memory Map 5V.png
