Julesc013/abacus-2/hardware/memory/Memory Map 6 Lite.png

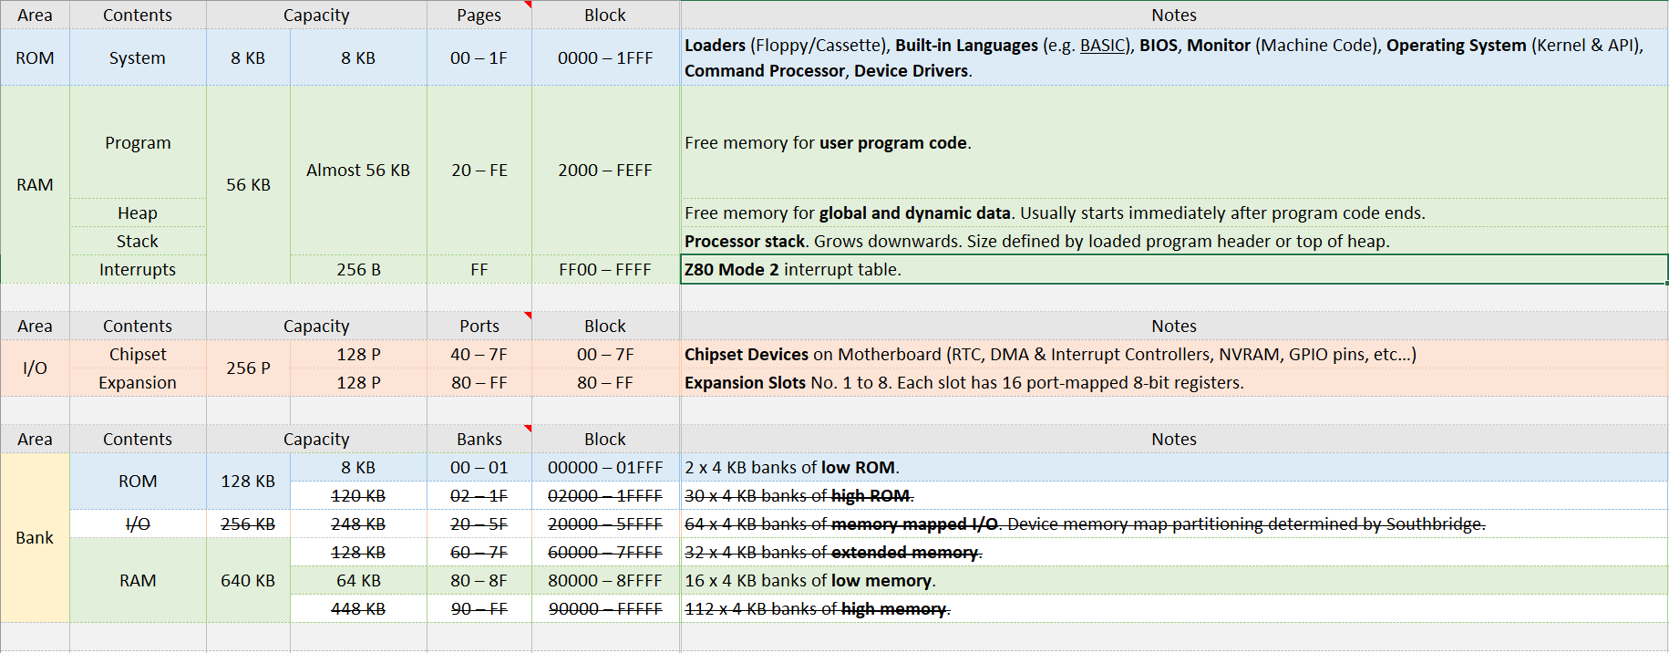
hardware/memory/Memory Map 6 Lite.png
