Julesc013/abacus-2/hardware/video/video_adapter/resources/Color_Palette_-_8-Bit_Color_(VGA).png

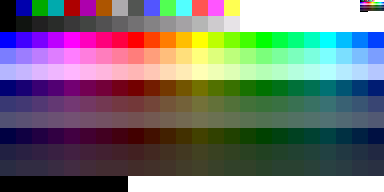
hardware/video/video_adapter/resources/Color_Palette_-_8-Bit_Color_(VGA).png
