Julesc013/abacus-2/hardware/video/video_adapter/resources/US_ASCII_Control_Character_Symbols.png

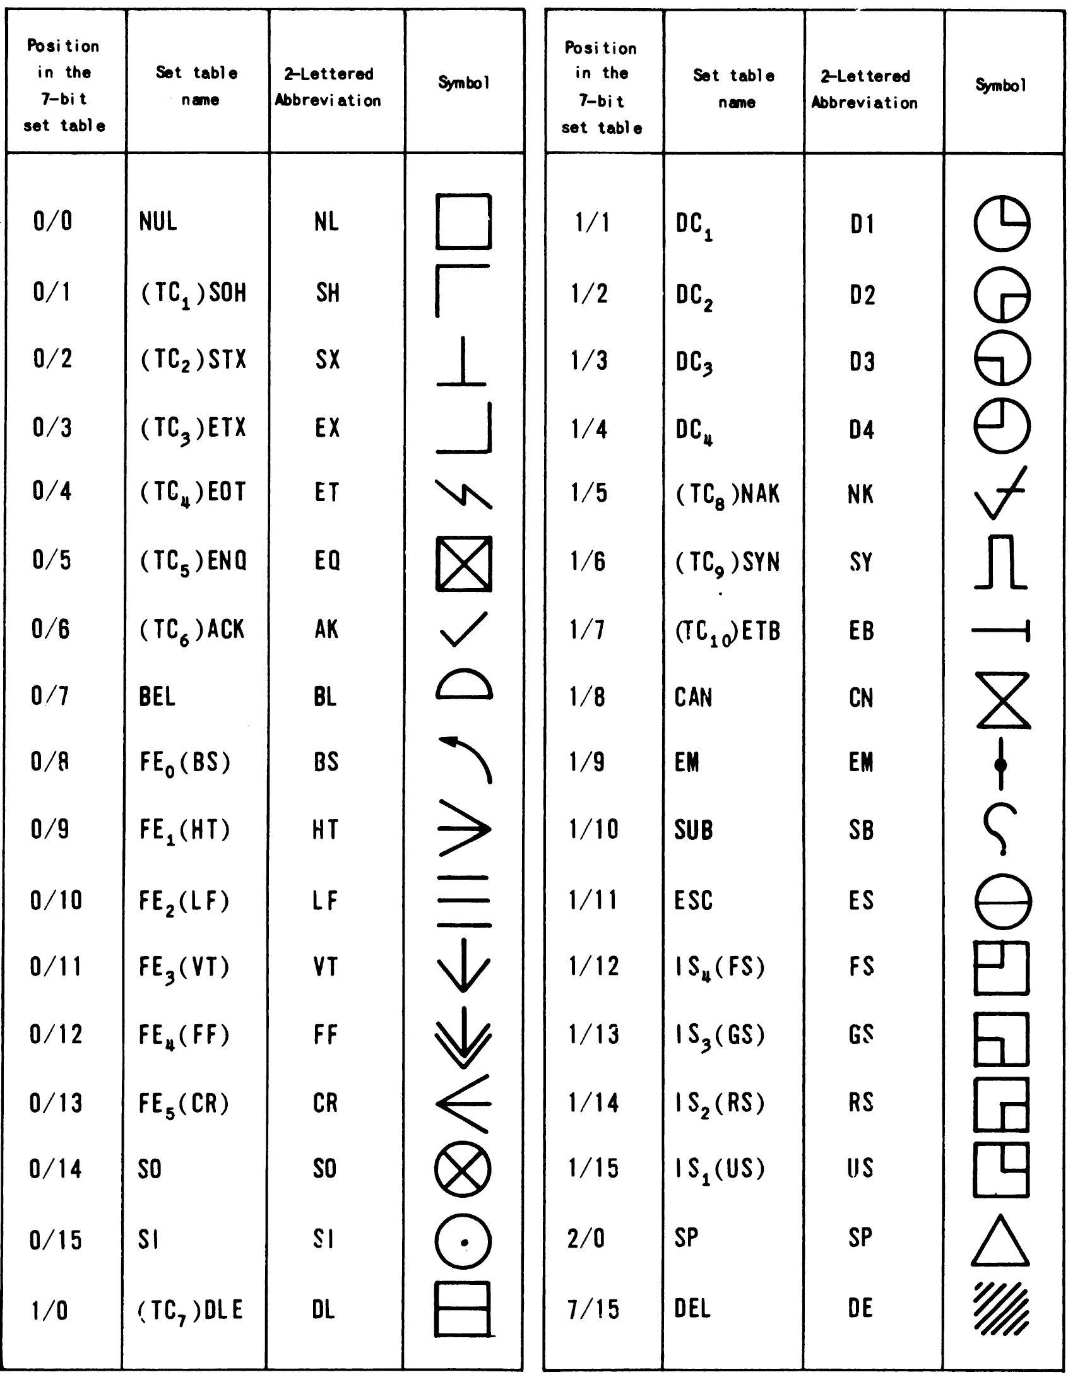
hardware/video/video_adapter/resources/US_ASCII_Control_Character_Symbols.png
