Julesc013/abacus-2/info/datasheets/alu/74181 Functions.jpg

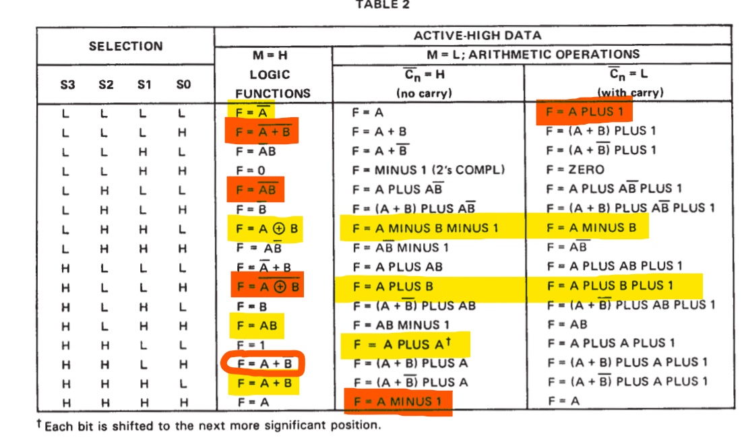
info/datasheets/alu/74181 Functions.jpg
