Julesc013/abacus-2/info/datasheets/logic/Logic Families.png

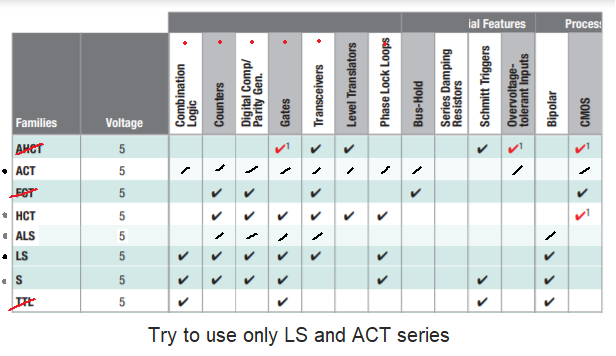
info/datasheets/logic/Logic Families.png
