Julesc013/abacus-2/hardware/video/Unicode Code Points.xlsx

Sheet: Latin
U+ | 0 | 1 | 2 | 3 | 4 | 5 | 6 | 7 | 8 | 9 | A | B | C | D | E | F | Block | #
0040 | @ | A | B | C | D | E | F | G | H | I | J | K | L | M | N | O | C0 Controls and Basic Latin | 52
0050 | P | Q | R | S | T | U | V | W | X | Y | Z | [ | \ | ] | ^ | _ | 0000–007F
0060 | ` | a | b | c | d | e | f | g | h | i | j | k | l | m | n | o | (identical to ASCII)
0070 | p | q | r | s | t | u | v | w | x | y | z | { | | | } | ~ | DEL
00A0 |  | ¡ | ¢ | £ | ¤ | ¥ | ¦ | § | ¨ | © | ª | « | ¬ |  | ® | ¯ | C1 Controls and Latin-1 Supplement | 64
00B0 | ° | ± | ² | ³ | ´ | µ | ¶ | · | ¸ | ¹ | º | » | ¼ | ½ | ¾ | ¿ | 0080–00FF
00C0 | À | Á | Â | Ã | Ä | Å | Æ | Ç | È | É | Ê | Ë | Ì | Í | Î | Ï | (identical to ISO/IEC 8859-1)
00D0 | Ð | Ñ | Ò | Ó | Ô | Õ | Ö | × | Ø | Ù | Ú | Û | Ü | Ý | Þ | ß
00E0 | à | á | â | ã | ä | å | æ | ç | è | é | ê | ë | ì | í | î | ï
00F0 | ð | ñ | ò | ó | ô | õ | ö | ÷ | ø | ù | ú | û | ü | ý | þ | ÿ
0100 | Ā | ā | Ă | ă | Ą | ą | Ć | ć | Ĉ | ĉ | Ċ | ċ | Č | č | Ď | ď | Latin Extended-A | 128
0110 | Đ | đ | Ē | ē | Ĕ | ĕ | Ė | ė | Ę | ę | Ě | ě | Ĝ | ĝ | Ğ | ğ | 0100–017F
0120 | Ġ | ġ | Ģ | ģ | Ĥ | ĥ | Ħ | ħ | Ĩ | ĩ | Ī | ī | Ĭ | ĭ | Į | į
0130 | İ | ı | Ĳ | ĳ | Ĵ | ĵ | Ķ | ķ | ĸ | Ĺ | ĺ | Ļ | ļ | Ľ | ľ | Ŀ
0140 | ŀ | Ł | ł | Ń | ń | Ņ | ņ | Ň | ň | ŉ | Ŋ | ŋ | Ō | ō | Ŏ | ŏ
0150 | Ő | ő | Œ | œ | Ŕ | ŕ | Ŗ | ŗ | Ř | ř | Ś | ś | Ŝ | ŝ | Ş | ş
0160 | Š | š | Ţ | ţ | Ť | ť | Ŧ | ŧ | Ũ | ũ | Ū | ū | Ŭ | ŭ | Ů | ů
0170 | Ű | ű | Ų | ų | Ŵ | ŵ | Ŷ | ŷ | Ÿ | Ź | ź | Ż | ż | Ž | ž | ſ
0180 | ƀ | Ɓ | Ƃ | ƃ | Ƅ | ƅ | Ɔ | Ƈ | ƈ | Ɖ | Ɗ | Ƌ | ƌ | ƍ | Ǝ | Ə | Latin Extended-B | 208
0190 | Ɛ | Ƒ | ƒ | Ɠ | Ɣ | ƕ | Ɩ | Ɨ | Ƙ | ƙ | ƚ | ƛ | Ɯ | Ɲ | ƞ | Ɵ | 0180–024F
01A0 | Ơ | ơ | Ƣ | ƣ | Ƥ | ƥ | Ʀ | Ƨ | ƨ | Ʃ | ƪ | ƫ | Ƭ | ƭ | Ʈ | Ư
01B0 | ư | Ʊ | Ʋ | Ƴ | ƴ | Ƶ | ƶ | Ʒ | Ƹ | ƹ | ƺ | ƻ | Ƽ | ƽ | ƾ | ƿ
01C0 | ǀ | ǁ | ǂ | ǃ | Ǆ | ǅ | ǆ | Ǉ | ǈ | ǉ | Ǌ | ǋ | ǌ | Ǎ | ǎ | Ǐ
01D0 | ǐ | Ǒ | ǒ | Ǔ | ǔ | Ǖ | ǖ | Ǘ | ǘ | Ǚ | ǚ | Ǜ | ǜ | ǝ | Ǟ | ǟ
01E0 | Ǡ | ǡ | Ǣ | ǣ | Ǥ | ǥ | Ǧ | ǧ | Ǩ | ǩ | Ǫ | ǫ | Ǭ | ǭ | Ǯ | ǯ
01F0 | ǰ | Ǳ | ǲ | ǳ | Ǵ | ǵ | Ƕ | Ƿ | Ǹ | ǹ | Ǻ | ǻ | Ǽ | ǽ | Ǿ | ǿ
0200 | Ȁ | ȁ | Ȃ | ȃ | Ȅ | ȅ | Ȇ | ȇ | Ȉ | ȉ | Ȋ | ȋ | Ȍ | ȍ | Ȏ | ȏ
0210 | Ȑ | ȑ | Ȓ | ȓ | Ȕ | ȕ | Ȗ | ȗ | Ș | ș | Ț | ț | Ȝ | ȝ | Ȟ | ȟ
0220 | Ƞ | ȡ | Ȣ | ȣ | Ȥ | ȥ | Ȧ | ȧ | Ȩ | ȩ | Ȫ | ȫ | Ȭ | ȭ | Ȯ | ȯ
0230 | Ȱ | ȱ | Ȳ | ȳ | ȴ | ȵ | ȶ | ȷ | ȸ | ȹ | Ⱥ | Ȼ | ȼ | Ƚ | Ⱦ | ȿ
0240 | ɀ | Ɂ | ɂ | Ƀ | Ʉ | Ʌ | Ɇ | ɇ | Ɉ | ɉ | Ɋ | ɋ | Ɍ | ɍ | Ɏ | ɏ
0250 | ɐ | ɑ | ɒ | ɓ | ɔ | ɕ | ɖ | ɗ | ɘ | ə | ɚ | ɛ | ɜ | ɝ | ɞ | ɟ | IPA Extensions | 96
0260 | ɠ | ɡ | ɢ | ɣ | ɤ | ɥ | ɦ | ɧ | ɨ | ɩ | ɪ | ɫ | ɬ | ɭ | ɮ | ɯ | 0250–02AF
0270 | ɰ | ɱ | ɲ | ɳ | ɴ | ɵ | ɶ | ɷ | ɸ | ɹ | ɺ | ɻ | ɼ | ɽ | ɾ | ɿ
0280 | ʀ | ʁ | ʂ | ʃ | ʄ | ʅ | ʆ | ʇ | ʈ | ʉ | ʊ | ʋ | ʌ | ʍ | ʎ | ʏ
0290 | ʐ | ʑ | ʒ | ʓ | ʔ | ʕ | ʖ | ʗ | ʘ | ʙ | ʚ | ʛ | ʜ | ʝ | ʞ | ʟ
02A0 | ʠ | ʡ | ʢ | ʣ | ʤ | ʥ | ʦ | ʧ | ʨ | ʩ | ʪ | ʫ | ʬ | ʭ | ʮ | ʯ
02B0 | ʰ | ʱ | ʲ | ʳ | ʴ | ʵ | ʶ | ʷ | ʸ | ʹ | ʺ | ʻ | ʼ | ʽ | ʾ | ʿ | Spacing Modifier Letters | 14
 |  |  |  |  |  |  |  |  |  |  |  |  |  |  |  |  | 02B0–02FF
02E0 | ˠ | ˡ | ˢ | ˣ | ˤ | ˥ | ˦ | ˧ | ˨ | ˩ | ˪ | ˫ | ˬ | ˭ | ˮ | ˯
1D00 | ᴀ | ᴁ | ᴂ | ᴃ | ᴄ | ᴅ | ᴆ | ᴇ | ᴈ | ᴉ | ᴊ | ᴋ | ᴌ | ᴍ | ᴎ | ᴏ | Phonetic Extensions | 111
1D10 | ᴐ | ᴑ | ᴒ | ᴓ | ᴔ | ᴕ | ᴖ | ᴗ | ᴘ | ᴙ | ᴚ | ᴛ | ᴜ | ᴝ | ᴞ | ᴟ | 1D00–1D7F
1D20 | ᴠ | ᴡ | ᴢ | ᴣ | ᴤ | ᴥ | ᴦ | ᴧ | ᴨ | ᴩ | ᴪ | ᴫ | ᴬ | ᴭ | ᴮ | ᴯ
1D30 | ᴰ | ᴱ | ᴲ | ᴳ | ᴴ | ᴵ | ᴶ | ᴷ | ᴸ | ᴹ | ᴺ | ᴻ | ᴼ | ᴽ | ᴾ | ᴿ
1D40 | ᵀ | ᵁ | ᵂ | ᵃ | ᵄ | ᵅ | ᵆ | ᵇ | ᵈ | ᵉ | ᵊ | ᵋ | ᵌ | ᵍ | ᵎ | ᵏ
1D50 | ᵐ | ᵑ | ᵒ | ᵓ | ᵔ | ᵕ | ᵖ | ᵗ | ᵘ | ᵙ | ᵚ | ᵛ | ᵜ | ᵝ | ᵞ | ᵟ
1D60 | ᵠ | ᵡ | ᵢ | ᵣ | ᵤ | ᵥ | ᵦ | ᵧ | ᵨ | ᵩ | ᵪ | ᵫ | ᵬ | ᵭ | ᵮ | ᵯ
1D70 | ᵰ | ᵱ | ᵲ | ᵳ | ᵴ | ᵵ | ᵶ | ᵷ | ᵸ | ᵹ | ᵺ | ᵻ | ᵼ | ᵽ | ᵾ | ᵿ
1D80 | ᶀ | ᶁ | ᶂ | ᶃ | ᶄ | ᶅ | ᶆ | ᶇ | ᶈ | ᶉ | ᶊ | ᶋ | ᶌ | ᶍ | ᶎ | ᶏ | Phonetic Extensions Supplement | 63
1D90 | ᶐ | ᶑ | ᶒ | ᶓ | ᶔ | ᶕ | ᶖ | ᶗ | ᶘ | ᶙ | ᶚ | ᶛ | ᶜ | ᶝ | ᶞ | ᶟ | 1D80–1DBF
1DA0 | ᶠ | ᶡ | ᶢ | ᶣ | ᶤ | ᶥ | ᶦ | ᶧ | ᶨ | ᶩ | ᶪ | ᶫ | ᶬ | ᶭ | ᶮ | ᶯ
1DB0 | ᶰ | ᶱ | ᶲ | ᶳ | ᶴ | ᶵ | ᶶ | ᶷ | ᶸ | ᶹ | ᶺ | ᶻ | ᶼ | ᶽ | ᶾ | ᶿ
1E00 | Ḁ | ḁ | Ḃ | ḃ | Ḅ | ḅ | Ḇ | ḇ | Ḉ | ḉ | Ḋ | ḋ | Ḍ | ḍ | Ḏ | ḏ | Latin Extended Additional | 256
1E10 | Ḑ | ḑ | Ḓ | ḓ | Ḕ | ḕ | Ḗ | ḗ | Ḙ | ḙ | Ḛ | ḛ | Ḝ | ḝ | Ḟ | ḟ | 1E00–1EFF
1E20 | Ḡ | ḡ | Ḣ | ḣ | Ḥ | ḥ | Ḧ | ḧ | Ḩ | ḩ | Ḫ | ḫ | Ḭ | ḭ | Ḯ | ḯ
1E30 | Ḱ | ḱ | Ḳ | ḳ | Ḵ | ḵ | Ḷ | ḷ | Ḹ | ḹ | Ḻ | ḻ | Ḽ | ḽ | Ḿ | ḿ
1E40 | Ṁ | ṁ | Ṃ | ṃ | Ṅ | ṅ | Ṇ | ṇ | Ṉ | ṉ | Ṋ | ṋ | Ṍ | ṍ | Ṏ | ṏ
1E50 | Ṑ | ṑ | Ṓ | ṓ | Ṕ | ṕ | Ṗ | ṗ | Ṙ | ṙ | Ṛ | ṛ | Ṝ | ṝ | Ṟ | ṟ
1E60 | Ṡ | ṡ | Ṣ | ṣ | Ṥ | ṥ | Ṧ | ṧ | Ṩ | ṩ | Ṫ | ṫ | Ṭ | ṭ | Ṯ | ṯ
1E70 | Ṱ | ṱ | Ṳ | ṳ | Ṵ | ṵ | Ṷ | ṷ | Ṹ | ṹ | Ṻ | ṻ | Ṽ | ṽ | Ṿ | ṿ
1E80 | Ẁ | ẁ | Ẃ | ẃ | Ẅ | ẅ | Ẇ | ẇ | Ẉ | ẉ | Ẋ | ẋ | Ẍ | ẍ | Ẏ | ẏ
1E90 | Ẑ | ẑ | Ẓ | ẓ | Ẕ | ẕ | ẖ | ẗ | ẘ | ẙ | ẚ | ẛ | ẜ | ẝ | ẞ | ẟ
1EA0 | Ạ | ạ | Ả | ả | Ấ | ấ | Ầ | ầ | Ẩ | ẩ | Ẫ | ẫ | Ậ | ậ | Ắ | ắ
1EB0 | Ằ | ằ | Ẳ | ẳ | Ẵ | ẵ | Ặ | ặ | Ẹ | ẹ | Ẻ | ẻ | Ẽ | ẽ | Ế | ế
1EC0 | Ề | ề | Ể | ể | Ễ | ễ | Ệ | ệ | Ỉ | ỉ | Ị | ị | Ọ | ọ | Ỏ | ỏ
1ED0 | Ố | ố | Ồ | ồ | Ổ | ổ | Ỗ | ỗ | Ộ | ộ | Ớ | ớ | Ờ | ờ | Ở | ở
1EE0 | Ỡ | ỡ | Ợ | ợ | Ụ | ụ | Ủ | ủ | Ứ | ứ | Ừ | ừ | Ử | ử | Ữ | ữ
1EF0 | Ự | ự | Ỳ | ỳ | Ỵ | ỵ | Ỷ | ỷ | Ỹ | ỹ | Ỻ | ỻ | Ỽ | ỽ | Ỿ | ỿ
2070 | ⁰ | ⁱ |  |  | ⁴ | ⁵ | ⁶ | ⁷ | ⁸ | ⁹ | ⁺ | ⁻ | ⁼ | ⁽ | ⁾ | ⁿ | Superscripts and Subscripts | 15
2080 | ₀ | ₁ | ₂ | ₃ | ₄ | ₅ | ₆ | ₇ | ₈ | ₉ | ₊ | ₋ | ₌ | ₍ | ₎ |  | 2070–209F
2090 | ₐ | ₑ | ₒ | ₓ | ₔ | ₕ | ₖ | ₗ | ₘ | ₙ | ₚ | ₛ | ₜ
2C60 | Ⱡ | ⱡ | Ɫ | Ᵽ | Ɽ | ⱥ | ⱦ | Ⱨ | ⱨ | Ⱪ | ⱪ | Ⱬ | ⱬ | Ɑ | Ɱ | Ɐ | Latin Extended-C | 32
2C70 | Ɒ | ⱱ | Ⱳ | ⱳ | ⱴ | Ⱶ | ⱶ | ⱷ | ⱸ | ⱹ | ⱺ | ⱻ | ⱼ | ⱽ | Ȿ | Ɀ | 2C60–2C7F
A720 | ꜠ | ꜡ | Ꜣ | ꜣ | Ꜥ | ꜥ | Ꜧ | ꜧ | Ꜩ | ꜩ | Ꜫ | ꜫ | Ꜭ | ꜭ | Ꜯ | ꜯ | Latin Extended-D | 188
A730 | ꜰ | ꜱ | Ꜳ | ꜳ | Ꜵ | ꜵ | Ꜷ | ꜷ | Ꜹ | ꜹ | Ꜻ | ꜻ | Ꜽ | ꜽ | Ꜿ | ꜿ | A720–A7FF
A740 | Ꝁ | ꝁ | Ꝃ | ꝃ | Ꝅ | ꝅ | Ꝇ | ꝇ | Ꝉ | ꝉ | Ꝋ | ꝋ | Ꝍ | ꝍ | Ꝏ | ꝏ
A750 | Ꝑ | ꝑ | Ꝓ | ꝓ | Ꝕ | ꝕ | Ꝗ | ꝗ | Ꝙ | ꝙ | Ꝛ | ꝛ | Ꝝ | ꝝ | Ꝟ | ꝟ
A760 | Ꝡ | ꝡ | Ꝣ | ꝣ | Ꝥ | ꝥ | Ꝧ | ꝧ | Ꝩ | ꝩ | Ꝫ | ꝫ | Ꝭ | ꝭ | Ꝯ | ꝯ
A770 | ꝰ | ꝱ | ꝲ | ꝳ | ꝴ | ꝵ | ꝶ | ꝷ | ꝸ | Ꝺ | ꝺ | Ꝼ | ꝼ | Ᵹ | Ꝿ | ꝿ
A780 | Ꞁ | ꞁ | Ꞃ | ꞃ | Ꞅ | ꞅ | Ꞇ | ꞇ | ꞈ | ꞉ | ꞊ | Ꞌ | ꞌ | Ɥ | ꞎ | ꞏ
A790 | Ꞑ | ꞑ | Ꞓ | ꞓ | ꞔ | ꞕ | Ꞗ | ꞗ | Ꞙ | ꞙ | Ꞛ | ꞛ | Ꞝ | ꞝ | Ꞟ | ꞟ
A7A0 | Ꞡ | ꞡ | Ꞣ | ꞣ | Ꞥ | ꞥ | Ꞧ | ꞧ | Ꞩ | ꞩ | Ɦ | Ɜ | Ɡ | Ɬ | Ɪ | ꞯ
A7B0 | Ʞ | Ʇ | Ʝ | Ꭓ | Ꞵ | ꞵ | Ꞷ | ꞷ | Ꞹ | ꞹ | Ꞻ | ꞻ | Ꞽ | ꞽ | Ꞿ | ꞿ
A7C0 | Ꟁ | ꟁ | Ꟃ | ꟃ | Ꞔ | Ʂ | Ᶎ | Ꟈ | ꟈ | Ꟊ | ꟊ
A7D0 | Ꟑ | ꟑ |  | ꟓ |  | ꟕ | Ꟗ | ꟗ | Ꟙ | ꟙ
A7E0
A7F0 |  |  | ꟲ | ꟳ | ꟴ | Ꟶ | ꟶ | ꟷ | ꟸ | ꟹ | ꟺ | ꟻ | ꟼ | ꟽ | ꟾ | ꟿ
AB30 | ꬰ | ꬱ | ꬲ | ꬳ | ꬴ | ꬵ | ꬶ | ꬷ | ꬸ | ꬹ | ꬺ | ꬻ | ꬼ | ꬽ | ꬾ | ꬿ | Latin Extended-E | 56
AB40 | ꭀ | ꭁ | ꭂ | ꭃ | ꭄ | ꭅ | ꭆ | ꭇ | ꭈ | ꭉ | ꭊ | ꭋ | ꭌ | ꭍ | ꭎ | ꭏ | AB30–AB6F
AB50 | ꭐ | ꭑ | ꭒ | ꭓ | ꭔ | ꭕ | ꭖ | ꭗ | ꭘ | ꭙ | ꭚ | ꭛ | ꭜ | ꭝ | ꭞ | ꭟ
AB60 | ꭠ | ꭡ | ꭢ | ꭣ | ꭤ | ꭥ | ꭦ | ꭧ | ꭨ | ꭩ | ꭪ | ꭫
FB00 | ﬀ | ﬁ | ﬂ | ﬃ | ﬄ | ﬅ | ﬆ |  |  |  |  |  |  |  |  |  | Alphabetic Presentation Forms | 7
FF20 | ＠ | Ａ | Ｂ | Ｃ | Ｄ | Ｅ | Ｆ | Ｇ | Ｈ | Ｉ | Ｊ | Ｋ | Ｌ | Ｍ | Ｎ | Ｏ | Halfwidth and Fullwidth Forms | 52
FF30 | Ｐ | Ｑ | Ｒ | Ｓ | Ｔ | Ｕ | Ｖ | Ｗ | Ｘ | Ｙ | Ｚ | ［ | ＼ | ］ | ＾ | ＿ | (fullwidth Latin letters)
FF40 | ｀ | ａ | ｂ | ｃ | ｄ | ｅ | ｆ | ｇ | ｈ | ｉ | ｊ | ｋ | ｌ | ｍ | ｎ | ｏ | FF00–FFEF
FF50 | ｐ | ｑ | ｒ | ｓ | ｔ | ｕ | ｖ | ｗ | ｘ | ｙ | ｚ | ｛ | ｜ | ｝ | ～ | ｟
10780 | 𐞀 | 𐞁 | 𐞂 | 𐞃 | 𐞄 | 𐞅 |  | 𐞇 | 𐞈 | 𐞉 | 𐞊 | 𐞋 | 𐞌 | 𐞍 | 𐞎 | 𐞏 | Latin Extended-F | 57
10790 | 𐞐 | 𐞑 | 𐞒 | 𐞓 | 𐞔 | 𐞕 | 𐞖 | 𐞗 | 𐞘 | 𐞙 | 𐞚 | 𐞛 | 𐞜 | 𐞝 | 𐞞 | 𐞟 | 10780–107BF
107A0 | 𐞠 | 𐞡 | 𐞢 | 𐞣 | 𐞤 | 𐞥 | 𐞦 | 𐞧 | 𐞨 | 𐞩 | 𐞪 | 𐞫 | 𐞬 | 𐞭 | 𐞮 | 𐞯
107B0 | 𐞰 |  | 𐞲 | 𐞳 | 𐞴 | 𐞵 | 𐞶 | 𐞷 | 𐞸 | 𐞹 | 𐞺
1DF00 | 𝼀 | 𝼁 | 𝼂 | 𝼃 | 𝼄 | 𝼅 | 𝼆 | 𝼇 | 𝼈 | 𝼉 | 𝼊 | 𝼋 | 𝼌 | 𝼍 | 𝼎 | 𝼏 | Latin Extended-G | 37
1DF10 | 𝼐 | 𝼑 | 𝼒 | 𝼓 | 𝼔 | 𝼕 | 𝼖 | 𝼗 | 𝼘 | 𝼙 | 𝼚 | 𝼛 | 𝼜 | 𝼝 | 𝼞 |  | 1DF00–1DFFF
1DF20 |  |  |  |  |  | 𝼥 | 𝼦 | 𝼧 | 𝼨 | 𝼩 | 𝼪
TOTAL |  |  |  |  |  |  |  |  |  |  |  |  |  |  |  |  |  | 1,481

Sheet: Non-Latin
U+ | U+ | 0 | 1 | 2 | 3 | 4 | 5 | 6 | 7 | 8 | 9 | A | B | C | D | E | F | Block | #
037x | U+037x | Ͱ | ͱ | Ͳ | ͳ | ʹ | ͵ | Ͷ | ͷ |  |  | ͺ | ͻ | ͼ | ͽ | ; | Ϳ | Greek and Coptic | 135
038x | U+038x |  |  |  |  | ΄ | ΅ | Ά | · | Έ | Ή | Ί |  | Ό |  | Ύ | Ώ | U+0370..U+03FF
039x | U+039x | ΐ | Α | Β | Γ | Δ | Ε | Ζ | Η | Θ | Ι | Κ | Λ | Μ | Ν | Ξ | Ο
03Ax | U+03Ax | Π | Ρ |  | Σ | Τ | Υ | Φ | Χ | Ψ | Ω | Ϊ | Ϋ | ά | έ | ή | ί
03Bx | U+03Bx | ΰ | α | β | γ | δ | ε | ζ | η | θ | ι | κ | λ | μ | ν | ξ | ο
03Cx | U+03Cx | π | ρ | ς | σ | τ | υ | φ | χ | ψ | ω | ϊ | ϋ | ό | ύ | ώ | Ϗ
03Dx | U+03Dx | ϐ | ϑ | ϒ | ϓ | ϔ | ϕ | ϖ | ϗ | Ϙ | ϙ | Ϛ | ϛ | Ϝ | ϝ | Ϟ | ϟ
03Ex | U+03Ex | Ϡ | ϡ | Ϣ | ϣ | Ϥ | ϥ | Ϧ | ϧ | Ϩ | ϩ | Ϫ | ϫ | Ϭ | ϭ | Ϯ | ϯ
03Fx | U+03Fx | ϰ | ϱ | ϲ | ϳ | ϴ | ϵ | ϶ | Ϸ | ϸ | Ϲ | Ϻ | ϻ | ϼ | Ͻ | Ͼ | Ͽ
040x | U+040x | Ѐ | Ё | Ђ | Ѓ | Є | Ѕ | І | Ї | Ј | Љ | Њ | Ћ | Ќ | Ѝ | Ў | Џ | Cyrillic | 256
041x | U+041x | А | Б | В | Г | Д | Е | Ж | З | И | Й | К | Л | М | Н | О | П | U+0400..U+04FF
042x | U+042x | Р | С | Т | У | Ф | Х | Ц | Ч | Ш | Щ | Ъ | Ы | Ь | Э | Ю | Я
043x | U+043x | а | б | в | г | д | е | ж | з | и | й | к | л | м | н | о | п
044x | U+044x | р | с | т | у | ф | х | ц | ч | ш | щ | ъ | ы | ь | э | ю | я
045x | U+045x | ѐ | ё | ђ | ѓ | є | ѕ | і | ї | ј | љ | њ | ћ | ќ | ѝ | ў | џ
046x | U+046x | Ѡ | ѡ | Ѣ | ѣ | Ѥ | ѥ | Ѧ | ѧ | Ѩ | ѩ | Ѫ | ѫ | Ѭ | ѭ | Ѯ | ѯ
047x | U+047x | Ѱ | ѱ | Ѳ | ѳ | Ѵ | ѵ | Ѷ | ѷ | Ѹ | ѹ | Ѻ | ѻ | Ѽ | ѽ | Ѿ | ѿ
048x | U+048x | Ҁ | ҁ | ҂ | ◌҃ | ◌҄ | ◌҅ | ◌҆ | ◌҇ | ◌҈ | ◌҉ | Ҋ | ҋ | Ҍ | ҍ | Ҏ | ҏ
049x | U+049x | Ґ | ґ | Ғ | ғ | Ҕ | ҕ | Җ | җ | Ҙ | ҙ | Қ | қ | Ҝ | ҝ | Ҟ | ҟ
04Ax | U+04Ax | Ҡ | ҡ | Ң | ң | Ҥ | ҥ | Ҧ | ҧ | Ҩ | ҩ | Ҫ | ҫ | Ҭ | ҭ | Ү | ү
04Bx | U+04Bx | Ұ | ұ | Ҳ | ҳ | Ҵ | ҵ | Ҷ | ҷ | Ҹ | ҹ | Һ | һ | Ҽ | ҽ | Ҿ | ҿ
04Cx | U+04Cx | Ӏ | Ӂ | ӂ | Ӄ | ӄ | Ӆ | ӆ | Ӈ | ӈ | Ӊ | ӊ | Ӌ | ӌ | Ӎ | ӎ | ӏ
04Dx | U+04Dx | Ӑ | ӑ | Ӓ | ӓ | Ӕ | ӕ | Ӗ | ӗ | Ә | ә | Ӛ | ӛ | Ӝ | ӝ | Ӟ | ӟ
04Ex | U+04Ex | Ӡ | ӡ | Ӣ | ӣ | Ӥ | ӥ | Ӧ | ӧ | Ө | ө | Ӫ | ӫ | Ӭ | ӭ | Ӯ | ӯ
04Fx | U+04Fx | Ӱ | ӱ | Ӳ | ӳ | Ӵ | ӵ | Ӷ | ӷ | Ӹ | ӹ | Ӻ | ӻ | Ӽ | ӽ | Ӿ | ӿ
304x | U+304x |  | ぁ | あ | ぃ | い | ぅ | う | ぇ | え | ぉ | お | か | が | き | ぎ | く | Hiragana | 93
305x | U+305x | ぐ | け | げ | こ | ご | さ | ざ | し | じ | す | ず | せ | ぜ | そ | ぞ | た | U+3040..U+309F
306x | U+306x | だ | ち | ぢ | っ | つ | づ | て | で | と | ど | な | に | ぬ | ね | の | は
307x | U+307x | ば | ぱ | ひ | び | ぴ | ふ | ぶ | ぷ | へ | べ | ぺ | ほ | ぼ | ぽ | ま | み
308x | U+308x | む | め | も | ゃ | や | ゅ | ゆ | ょ | よ | ら | り | る | れ | ろ | ゎ | わ
309x | U+309x | ゐ | ゑ | を | ん | ゔ | ゕ | ゖ |  |  | ゙ | ゚ | ゛ | ゜ | ゝ | ゞ | ゟ
30Ax | U+30Ax | ゠ | ァ | ア | ィ | イ | ゥ | ウ | ェ | エ | ォ | オ | カ | ガ | キ | ギ | ク | Katakana | 96
30Bx | U+30Bx | グ | ケ | ゲ | コ | ゴ | サ | ザ | シ | ジ | ス | ズ | セ | ゼ | ソ | ゾ | タ | U+30A0..U+30FF
30Cx | U+30Cx | ダ | チ | ヂ | ッ | ツ | ヅ | テ | デ | ト | ド | ナ | ニ | ヌ | ネ | ノ | ハ
30Dx | U+30Dx | バ | パ | ヒ | ビ | ピ | フ | ブ | プ | ヘ | ベ | ペ | ホ | ボ | ポ | マ | ミ
30Ex | U+30Ex | ム | メ | モ | ャ | ヤ | ュ | ユ | ョ | ヨ | ラ | リ | ル | レ | ロ | ヮ | ワ
30Fx | U+30Fx | ヰ | ヱ | ヲ | ン | ヴ | ヵ | ヶ | ヷ | ヸ | ヹ | ヺ | ・ | ー | ヽ | ヾ | ヿ
300x | U+300x | IDSP | 、 | 。 | 〃 | 〄 | 々 | 〆 | 〇 | 〈 | 〉 | 《 | 》 | 「 | 」 | 『 | 』 | CJK Symbols and Punctuation | 64
301x | U+301x | 【 | 】 | 〒 | 〓 | 〔 | 〕 | 〖 | 〗 | 〘 | 〙 | 〚 | 〛 | 〜 | 〝 | 〞 | 〟 | U+3000..U+303F
302x | U+302x | 〠 | 〡 | 〢 | 〣 | 〤 | 〥 | 〦 | 〧 | 〨 | 〩 | 〪 | 〫 | 〬 | 〭 | 〮 | 〯
303x | U+303x | 〰 | 〱 | 〲 | 〳 | 〴 | 〵 | 〶 | 〷 | 〸 | 〹 | 〺 | 〻 | 〼 | 〽 | 〾 | 〿

Sheet: Punctuation
U+ | U+ | 0 | 1 | 2 | 3 | 4 | 5 | 6 | 7 | 8 | 9 | A | B | C | D | E | F | Block | #
200x | U+200x | NQSP | MQSP | ENSP | EMSP | 3/MSP | 4/MSP | 6/MSP | FSP | PSP | THSP | HSP | ZWSP | ZWNJ | ZW J | LRM | RLM | General Punctuation | 111
201x | U+201x | ‐ | NB | ‒ | – | — | ― | ‖ | ‗ | ‘ | ’ | ‚ | ‛ | “ | ” | „ | ‟
202x | U+202x | † | ‡ | • | ‣ | ․ | ‥ | … | ‧ | LSEP | PSEP | LRE | RLE | PDF | LRO | RLO | NNBSP
203x | U+203x | ‰ | ‱ | ′ | ″ | ‴ | ‵ | ‶ | ‷ | ‸ | ‹ | › | ※ | ‼ | ‽ | ‾ | ‿
204x | U+204x | ⁀ | ⁁ | ⁂ | ⁃ | ⁄ | ⁅ | ⁆ | ⁇ | ⁈ | ⁉ | ⁊ | ⁋ | ⁌ | ⁍ | ⁎ | ⁏
205x | U+205x | ⁐ | ⁑ | ⁒ | ⁓ | ⁔ | ⁕ | ⁖ | ⁗ | ⁘ | ⁙ | ⁚ | ⁛ | ⁜ | ⁝ | ⁞ | MMSP
206x | U+206x | WJ | ƒ() | × | , | + |  | LRI | RLI | FSI | PDI | ISS | ASS | IAFS | AAFS | NADS | NODS
2E0x | U+2E0x | ⸀ | ⸁ | ⸂ | ⸃ | ⸄ | ⸅ | ⸆ | ⸇ | ⸈ | ⸉ | ⸊ | ⸋ | ⸌ | ⸍ | ⸎ | ⸏ | Supplemental Punctuation | 128
2E1x | U+2E1x | ⸐ | ⸑ | ⸒ | ⸓ | ⸔ | ⸕ | ⸖ | ⸗ | ⸘ | ⸙ | ⸚ | ⸛ | ⸜ | ⸝ | ⸞ | ⸟ | U+2E00..U+2E7F
2E2x | U+2E2x | ⸠ | ⸡ | ⸢ | ⸣ | ⸤ | ⸥ | ⸦ | ⸧ | ⸨ | ⸩ | ⸪ | ⸫ | ⸬ | ⸭ | ⸮ | ⸯ
2E3x | U+2E3x | ⸰ | ⸱ | ⸲ | ⸳ | ⸴ | ⸵ | ⸶ | ⸷ | ⸸ | ⸹ | 2M⸺ | 3M⸻ | ⸼ | ⸽ | ⸾ | ⸿
2E4x | U+2E4x | ⹀ | ⹁ | ⹂ | ⹃ | ⹄ | ⹅ | ⹆ | ⹇ | ⹈ | ⹉ | ⹊ | ⹋ | ⹌ | ⹍ | ⹎ | ⹏
2E5x | U+2E5x | ⹐ | ⹑ | ⹒ | ⹓ | ⹔ | ⹕ | ⹖ | ⹗ | ⹘ | ⹙ | ⹚ | ⹛ | ⹜ | ⹝
2E6x | U+2E6x
2E7x | U+2E7x
20Ax | U+20Ax | ₠ | ₡ | ₢ | ₣ | ₤ | ₥ | ₦ | ₧ | ₨ | ₩ | ₪ | ₫ | € | ₭ | ₮ | ₯ | Currency Symbols | 48
20Bx | U+20Bx | ₰ | ₱ | ₲ | ₳ | ₴ | ₵ | ₶ | ₷ | ₸ | ₹ | ₺ | ₻ | ₼ | ₽ | ₾ | ₿ | U+20A0..U+20CF
20Cx | U+20Cx | ⃀
210x | U+210x | ℀ | ℁ | ℂ | ℃ | ℄ | ℅ | ℆ | ℇ | ℈ | ℉ | ℊ | ℋ | ℌ | ℍ | ℎ | ℏ | Letterlike Symbols | 80
211x | U+211x | ℐ | ℑ | ℒ | ℓ | ℔ | ℕ | № | ℗ | ℘ | ℙ | ℚ | ℛ | ℜ | ℝ | ℞ | ℟ | U+2100–U+214F
212x | U+212x | ℠ | ℡ | ™ | ℣ | ℤ | ℥ | Ω | ℧ | ℨ | ℩ | K | Å | ℬ | ℭ | ℮ | ℯ
213x | U+213x | ℰ | ℱ | Ⅎ | ℳ | ℴ | ℵ | ℶ | ℷ | ℸ | ℹ | ℺ | ℻ | ℼ | ℽ | ℾ | ℿ
214x | U+214x | ⅀ | ⅁ | ⅂ | ⅃ | ⅄ | ⅅ | ⅆ | ⅇ | ⅈ | ⅉ | ⅊ | ⅋ | ⅌ | ⅍ | ⅎ | ⅏
246x | U+246x | ① | ② | ③ | ④ | ⑤ | ⑥ | ⑦ | ⑧ | ⑨ | ⑩ | ⑪ | ⑫ | ⑬ | ⑭ | ⑮ | ⑯ | Enclosed Alphanumerics | 160
247x | U+247x | ⑰ | ⑱ | ⑲ | ⑳ | ⑴ | ⑵ | ⑶ | ⑷ | ⑸ | ⑹ | ⑺ | ⑻ | ⑼ | ⑽ | ⑾ | ⑿ | U+2460..U+24FF
248x | U+248x | ⒀ | ⒁ | ⒂ | ⒃ | ⒄ | ⒅ | ⒆ | ⒇ | ⒈ | ⒉ | ⒊ | ⒋ | ⒌ | ⒍ | ⒎ | ⒏
249x | U+249x | ⒐ | ⒑ | ⒒ | ⒓ | ⒔ | ⒕ | ⒖ | ⒗ | ⒘ | ⒙ | ⒚ | ⒛ | ⒜ | ⒝ | ⒞ | ⒟
24Ax | U+24Ax | ⒠ | ⒡ | ⒢ | ⒣ | ⒤ | ⒥ | ⒦ | ⒧ | ⒨ | ⒩ | ⒪ | ⒫ | ⒬ | ⒭ | ⒮ | ⒯
24Bx | U+24Bx | ⒰ | ⒱ | ⒲ | ⒳ | ⒴ | ⒵ | Ⓐ | Ⓑ | Ⓒ | Ⓓ | Ⓔ | Ⓕ | Ⓖ | Ⓗ | Ⓘ | Ⓙ
24Cx | U+24Cx | Ⓚ | Ⓛ | Ⓜ | Ⓝ | Ⓞ | Ⓟ | Ⓠ | Ⓡ | Ⓢ | Ⓣ | Ⓤ | Ⓥ | Ⓦ | Ⓧ | Ⓨ | Ⓩ
24Dx | U+24Dx | ⓐ | ⓑ | ⓒ | ⓓ | ⓔ | ⓕ | ⓖ | ⓗ | ⓘ | ⓙ | ⓚ | ⓛ | ⓜ | ⓝ | ⓞ | ⓟ
24Ex | U+24Ex | ⓠ | ⓡ | ⓢ | ⓣ | ⓤ | ⓥ | ⓦ | ⓧ | ⓨ | ⓩ | ⓪ | ⓫ | ⓬ | ⓭ | ⓮ | ⓯
24Fx | U+24Fx | ⓰ | ⓱ | ⓲ | ⓳ | ⓴ | ⓵ | ⓶ | ⓷ | ⓸ | ⓹ | ⓺ | ⓻ | ⓼ | ⓽ | ⓾ | ⓿

Sheet: Mathematics
U+ | U+ | 0 | 1 | 2 | 3 | 4 | 5 | 6 | 7 | 8 | 9 | A | B | C | D | E | F | Block | #
220x | U+220x | ∀ | ∁ | ∂ | ∃ | ∄ | ∅ | ∆ | ∇ | ∈ | ∉ | ∊ | ∋ | ∌ | ∍ | ∎ | ∏ | Mathematical Operators | 256
221x | U+221x | ∐ | ∑ | − | ∓ | ∔ | ∕ | ∖ | ∗ | ∘ | ∙ | √ | ∛ | ∜ | ∝ | ∞ | ∟ | U+2200–U+22FF
222x | U+222x | ∠ | ∡ | ∢ | ∣ | ∤ | ∥ | ∦ | ∧ | ∨ | ∩ | ∪ | ∫ | ∬ | ∭ | ∮ | ∯
223x | U+223x | ∰ | ∱ | ∲ | ∳ | ∴ | ∵ | ∶ | ∷ | ∸ | ∹ | ∺ | ∻ | ∼ | ∽ | ∾ | ∿
224x | U+224x | ≀ | ≁ | ≂ | ≃ | ≄ | ≅ | ≆ | ≇ | ≈ | ≉ | ≊ | ≋ | ≌ | ≍ | ≎ | ≏
225x | U+225x | ≐ | ≑ | ≒ | ≓ | ≔ | ≕ | ≖ | ≗ | ≘ | ≙ | ≚ | ≛ | ≜ | ≝ | ≞ | ≟
226x | U+226x | ≠ | ≡ | ≢ | ≣ | ≤ | ≥ | ≦ | ≧ | ≨ | ≩ | ≪ | ≫ | ≬ | ≭ | ≮ | ≯
227x | U+227x | ≰ | ≱ | ≲ | ≳ | ≴ | ≵ | ≶ | ≷ | ≸ | ≹ | ≺ | ≻ | ≼ | ≽ | ≾ | ≿
228x | U+228x | ⊀ | ⊁ | ⊂ | ⊃ | ⊄ | ⊅ | ⊆ | ⊇ | ⊈ | ⊉ | ⊊ | ⊋ | ⊌ | ⊍ | ⊎ | ⊏
229x | U+229x | ⊐ | ⊑ | ⊒ | ⊓ | ⊔ | ⊕ | ⊖ | ⊗ | ⊘ | ⊙ | ⊚ | ⊛ | ⊜ | ⊝ | ⊞ | ⊟
22Ax | U+22Ax | ⊠ | ⊡ | ⊢ | ⊣ | ⊤ | ⊥ | ⊦ | ⊧ | ⊨ | ⊩ | ⊪ | ⊫ | ⊬ | ⊭ | ⊮ | ⊯
22Bx | U+22Bx | ⊰ | ⊱ | ⊲ | ⊳ | ⊴ | ⊵ | ⊶ | ⊷ | ⊸ | ⊹ | ⊺ | ⊻ | ⊼ | ⊽ | ⊾ | ⊿
22Cx | U+22Cx | ⋀ | ⋁ | ⋂ | ⋃ | ⋄ | ⋅ | ⋆ | ⋇ | ⋈ | ⋉ | ⋊ | ⋋ | ⋌ | ⋍ | ⋎ | ⋏
22Dx | U+22Dx | ⋐ | ⋑ | ⋒ | ⋓ | ⋔ | ⋕ | ⋖ | ⋗ | ⋘ | ⋙ | ⋚ | ⋛ | ⋜ | ⋝ | ⋞ | ⋟
22Ex | U+22Ex | ⋠ | ⋡ | ⋢ | ⋣ | ⋤ | ⋥ | ⋦ | ⋧ | ⋨ | ⋩ | ⋪ | ⋫ | ⋬ | ⋭ | ⋮ | ⋯
22Fx | U+22Fx | ⋰ | ⋱ | ⋲ | ⋳ | ⋴ | ⋵ | ⋶ | ⋷ | ⋸ | ⋹ | ⋺ | ⋻ | ⋼ | ⋽ | ⋾ | ⋿
2A0x | U+2A0x | ⨀ | ⨁ | ⨂ | ⨃ | ⨄ | ⨅ | ⨆ | ⨇ | ⨈ | ⨉ | ⨊ | ⨋ | ⨌ | ⨍ | ⨎ | ⨏ | Supplemental Mathematical Operators | 256
2A1x | U+2A1x | ⨐ | ⨑ | ⨒ | ⨓ | ⨔ | ⨕ | ⨖ | ⨗ | ⨘ | ⨙ | ⨚ | ⨛ | ⨜ | ⨝ | ⨞ | ⨟ | U+2A00–U+2AFF
2A2x | U+2A2x | ⨠ | ⨡ | ⨢ | ⨣ | ⨤ | ⨥ | ⨦ | ⨧ | ⨨ | ⨩ | ⨪ | ⨫ | ⨬ | ⨭ | ⨮ | ⨯
2A3x | U+2A3x | ⨰ | ⨱ | ⨲ | ⨳ | ⨴ | ⨵ | ⨶ | ⨷ | ⨸ | ⨹ | ⨺ | ⨻ | ⨼ | ⨽ | ⨾ | ⨿
2A4x | U+2A4x | ⩀ | ⩁ | ⩂ | ⩃ | ⩄ | ⩅ | ⩆ | ⩇ | ⩈ | ⩉ | ⩊ | ⩋ | ⩌ | ⩍ | ⩎ | ⩏
2A5x | U+2A5x | ⩐ | ⩑ | ⩒ | ⩓ | ⩔ | ⩕ | ⩖ | ⩗ | ⩘ | ⩙ | ⩚ | ⩛ | ⩜ | ⩝ | ⩞ | ⩟
2A6x | U+2A6x | ⩠ | ⩡ | ⩢ | ⩣ | ⩤ | ⩥ | ⩦ | ⩧ | ⩨ | ⩩ | ⩪ | ⩫ | ⩬ | ⩭ | ⩮ | ⩯
2A7x | U+2A7x | ⩰ | ⩱ | ⩲ | ⩳ | ⩴ | ⩵ | ⩶ | ⩷ | ⩸ | ⩹ | ⩺ | ⩻ | ⩼ | ⩽ | ⩾ | ⩿
2A8x | U+2A8x | ⪀ | ⪁ | ⪂ | ⪃ | ⪄ | ⪅ | ⪆ | ⪇ | ⪈ | ⪉ | ⪊ | ⪋ | ⪌ | ⪍ | ⪎ | ⪏
2A9x | U+2A9x | ⪐ | ⪑ | ⪒ | ⪓ | ⪔ | ⪕ | ⪖ | ⪗ | ⪘ | ⪙ | ⪚ | ⪛ | ⪜ | ⪝ | ⪞ | ⪟
2AAx | U+2AAx | ⪠ | ⪡ | ⪢ | ⪣ | ⪤ | ⪥ | ⪦ | ⪧ | ⪨ | ⪩ | ⪪ | ⪫ | ⪬ | ⪭ | ⪮ | ⪯
2ABx | U+2ABx | ⪰ | ⪱ | ⪲ | ⪳ | ⪴ | ⪵ | ⪶ | ⪷ | ⪸ | ⪹ | ⪺ | ⪻ | ⪼ | ⪽ | ⪾ | ⪿
2ACx | U+2ACx | ⫀ | ⫁ | ⫂ | ⫃ | ⫄ | ⫅ | ⫆ | ⫇ | ⫈ | ⫉ | ⫊ | ⫋ | ⫌ | ⫍ | ⫎ | ⫏
2ADx | U+2ADx | ⫐ | ⫑ | ⫒ | ⫓ | ⫔ | ⫕ | ⫖ | ⫗ | ⫘ | ⫙ | ⫚ | ⫛ | ⫝̸ | ⫝ | ⫞ | ⫟
2AEx | U+2AEx | ⫠ | ⫡ | ⫢ | ⫣ | ⫤ | ⫥ | ⫦ | ⫧ | ⫨ | ⫩ | ⫪ | ⫫ | ⫬ | ⫭ | ⫮ | ⫯
2AFx | U+2AFx | ⫰ | ⫱ | ⫲ | ⫳ | ⫴ | ⫵ | ⫶ | ⫷ | ⫸ | ⫹ | ⫺ | ⫻ | ⫼ | ⫽ | ⫾ | ⫿
27Cx | U+27Cx | ⟀ | ⟁ | ⟂ | ⟃ | ⟄ | ⟅ | ⟆ | ⟇ | ⟈ | ⟉ | ⟊ | ⟋ | ⟌ | ⟍ | ⟎ | ⟏ | Miscellaneous Mathematical Symbols-A | 48
27Dx | U+27Dx | ⟐ | ⟑ | ⟒ | ⟓ | ⟔ | ⟕ | ⟖ | ⟗ | ⟘ | ⟙ | ⟚ | ⟛ | ⟜ | ⟝ | ⟞ | ⟟ | U+27C0–U+27EF
27Ex | U+27Ex | ⟠ | ⟡ | ⟢ | ⟣ | ⟤ | ⟥ | ⟦ | ⟧ | ⟨ | ⟩ | ⟪ | ⟫ | ⟬ | ⟭ | ⟮ | ⟯
298x | U+298x | ⦀ | ⦁ | ⦂ | ⦃ | ⦄ | ⦅ | ⦆ | ⦇ | ⦈ | ⦉ | ⦊ | ⦋ | ⦌ | ⦍ | ⦎ | ⦏ | Miscellaneous Mathematical Symbols-B | 128
299x | U+299x | ⦐ | ⦑ | ⦒ | ⦓ | ⦔ | ⦕ | ⦖ | ⦗ | ⦘ | ⦙ | ⦚ | ⦛ | ⦜ | ⦝ | ⦞ | ⦟ | U+2980–U+29FF
29Ax | U+29Ax | ⦠ | ⦡ | ⦢ | ⦣ | ⦤ | ⦥ | ⦦ | ⦧ | ⦨ | ⦩ | ⦪ | ⦫ | ⦬ | ⦭ | ⦮ | ⦯
29Bx | U+29Bx | ⦰ | ⦱ | ⦲ | ⦳ | ⦴ | ⦵ | ⦶ | ⦷ | ⦸ | ⦹ | ⦺ | ⦻ | ⦼ | ⦽ | ⦾ | ⦿
29Cx | U+29Cx | ⧀ | ⧁ | ⧂ | ⧃ | ⧄ | ⧅ | ⧆ | ⧇ | ⧈ | ⧉ | ⧊ | ⧋ | ⧌ | ⧍ | ⧎ | ⧏
29Dx | U+29Dx | ⧐ | ⧑ | ⧒ | ⧓ | ⧔ | ⧕ | ⧖ | ⧗ | ⧘ | ⧙ | ⧚ | ⧛ | ⧜ | ⧝ | ⧞ | ⧟
29Ex | U+29Ex | ⧠ | ⧡ | ⧢ | ⧣ | ⧤ | ⧥ | ⧦ | ⧧ | ⧨ | ⧩ | ⧪ | ⧫ | ⧬ | ⧭ | ⧮ | ⧯
29Fx | U+29Fx | ⧰ | ⧱ | ⧲ | ⧳ | ⧴ | ⧵ | ⧶ | ⧷ | ⧸ | ⧹ | ⧺ | ⧻ | ⧼ | ⧽ | ⧾ | ⧿
2160 | 2160 | Ⅰ | Ⅱ | Ⅲ | Ⅳ | Ⅴ | Ⅵ | Ⅶ | Ⅷ | Ⅸ | Ⅹ | Ⅺ | Ⅻ | Ⅼ | Ⅽ | Ⅾ | Ⅿ | Number Forms | 41
2170 | 2170 | ⅰ | ⅱ | ⅲ | ⅳ | ⅴ | ⅵ | ⅶ | ⅷ | ⅸ | ⅹ | ⅺ | ⅻ | ⅼ | ⅽ | ⅾ | ⅿ | 2150–218F
2180 | 2180 | ↀ | ↁ | ↂ | Ↄ | ↄ | ↅ | ↆ | ↇ | ↈ | ↉ | ↊ | ↋

Sheet: Technical
U+ | U+ | 0 | 1 | 2 | 3 | 4 | 5 | 6 | 7 | 8 | 9 | A | B | C | D | E | F | Block | #
230x | U+230x | ⌀ | ⌁ | ⌂ | ⌃ | ⌄ | ⌅ | ⌆ | ⌇ | ⌈ | ⌉ | ⌊ | ⌋ | ⌌ | ⌍ | ⌎ | ⌏ | Miscellaneous Technical | 256
231x | U+231x | ⌐ | ⌑ | ⌒ | ⌓ | ⌔ | ⌕ | ⌖ | ⌗ | ⌘ | ⌙ | ⌚ | ⌛ | ⌜ | ⌝ | ⌞ | ⌟ | U+2300..U+23FF
232x | U+232x | ⌠ | ⌡ | ⌢ | ⌣ | ⌤ | ⌥ | ⌦ | ⌧ | ⌨ | 〈 | 〉 | ⌫ | ⌬ | ⌭ | ⌮ | ⌯
233x | U+233x | ⌰ | ⌱ | ⌲ | ⌳ | ⌴ | ⌵ | ⌶ | ⌷ | ⌸ | ⌹ | ⌺ | ⌻ | ⌼ | ⌽ | ⌾ | ⌿
234x | U+234x | ⍀ | ⍁ | ⍂ | ⍃ | ⍄ | ⍅ | ⍆ | ⍇ | ⍈ | ⍉ | ⍊ | ⍋ | ⍌ | ⍍ | ⍎ | ⍏
235x | U+235x | ⍐ | ⍑ | ⍒ | ⍓ | ⍔ | ⍕ | ⍖ | ⍗ | ⍘ | ⍙ | ⍚ | ⍛ | ⍜ | ⍝ | ⍞ | ⍟
236x | U+236x | ⍠ | ⍡ | ⍢ | ⍣ | ⍤ | ⍥ | ⍦ | ⍧ | ⍨ | ⍩ | ⍪ | ⍫ | ⍬ | ⍭ | ⍮ | ⍯
237x | U+237x | ⍰ | ⍱ | ⍲ | ⍳ | ⍴ | ⍵ | ⍶ | ⍷ | ⍸ | ⍹ | ⍺ | ⍻ | ⍼ | ⍽ | ⍾ | ⍿
238x | U+238x | ⎀ | ⎁ | ⎂ | ⎃ | ⎄ | ⎅ | ⎆ | ⎇ | ⎈ | ⎉ | ⎊ | ⎋ | ⎌ | ⎍ | ⎎ | ⎏
239x | U+239x | ⎐ | ⎑ | ⎒ | ⎓ | ⎔ | ⎕ | ⎖ | ⎗ | ⎘ | ⎙ | ⎚ | ⎛ | ⎜ | ⎝ | ⎞ | ⎟
23Ax | U+23Ax | ⎠ | ⎡ | ⎢ | ⎣ | ⎤ | ⎥ | ⎦ | ⎧ | ⎨ | ⎩ | ⎪ | ⎫ | ⎬ | ⎭ | ⎮ | ⎯
23Bx | U+23Bx | ⎰ | ⎱ | ⎲ | ⎳ | ⎴ | ⎵ | ⎶ | ⎷ | ⎸ | ⎹ | ⎺ | ⎻ | ⎼ | ⎽ | ⎾ | ⎿
23Cx | U+23Cx | ⏀ | ⏁ | ⏂ | ⏃ | ⏄ | ⏅ | ⏆ | ⏇ | ⏈ | ⏉ | ⏊ | ⏋ | ⏌ | ⏍ | ⏎ | ⏏
23Dx | U+23Dx | ⏐ | ⏑ | ⏒ | ⏓ | ⏔ | ⏕ | ⏖ | ⏗ | ⏘ | ⏙ | ⏚ | ⏛ | ⏜ | ⏝ | ⏞ | ⏟
23Ex | U+23Ex | ⏠ | ⏡ | ⏢ | ⏣ | ⏤ | ⏥ | ⏦ | ⏧ | ⏨ | ⏩ | ⏪ | ⏫ | ⏬ | ⏭ | ⏮ | ⏯
23Fx | U+23Fx | ⏰ | ⏱ | ⏲ | ⏳ | ⏴ | ⏵ | ⏶ | ⏷ | ⏸ | ⏹ | ⏺ | ⏻ | ⏼ | ⏽ | ⏾ | ⏿
244x | U+244x | ⑀ | ⑁ | ⑂ | ⑃ | ⑄ | ⑅ | ⑆ | ⑇ | ⑈ | ⑉ | ⑊ |  |  |  |  |  | Optical Character Recognition | 11
245x | U+245x |  |  |  |  |  |  |  |  |  |  |  |  |  |  |  |  | U+2440..U+245F
240x | U+240x | ␀ | ␁ | ␂ | ␃ | ␄ | ␅ | ␆ | ␇ | ␈ | ␉ | ␊ | ␋ | ␌ | ␍ | ␎ | ␏ | Control Pictures | 39
241x | U+241x | ␐ | ␑ | ␒ | ␓ | ␔ | ␕ | ␖ | ␗ | ␘ | ␙ | ␚ | ␛ | ␜ | ␝ | ␞ | ␟ | U+2400..U+243F
242x | U+242x | ␠ | ␡ | ␢ | ␣ | ␤ | ␥ | ␦
243x | U+243x

Sheet: Symbols
U+ | U+ | 0 | 1 | 2 | 3 | 4 | 5 | 6 | 7 | 8 | 9 | A | B | C | D | E | F | Block | #
250x | U+250x | ─ | ━ | │ | ┃ | ┄ | ┅ | ┆ | ┇ | ┈ | ┉ | ┊ | ┋ | ┌ | ┍ | ┎ | ┏ | Box Drawing | 128
251x | U+251x | ┐ | ┑ | ┒ | ┓ | └ | ┕ | ┖ | ┗ | ┘ | ┙ | ┚ | ┛ | ├ | ┝ | ┞ | ┟ | U+2500..U+257F
252x | U+252x | ┠ | ┡ | ┢ | ┣ | ┤ | ┥ | ┦ | ┧ | ┨ | ┩ | ┪ | ┫ | ┬ | ┭ | ┮ | ┯
253x | U+253x | ┰ | ┱ | ┲ | ┳ | ┴ | ┵ | ┶ | ┷ | ┸ | ┹ | ┺ | ┻ | ┼ | ┽ | ┾ | ┿
254x | U+254x | ╀ | ╁ | ╂ | ╃ | ╄ | ╅ | ╆ | ╇ | ╈ | ╉ | ╊ | ╋ | ╌ | ╍ | ╎ | ╏
255x | U+255x | ═ | ║ | ╒ | ╓ | ╔ | ╕ | ╖ | ╗ | ╘ | ╙ | ╚ | ╛ | ╜ | ╝ | ╞ | ╟
256x | U+256x | ╠ | ╡ | ╢ | ╣ | ╤ | ╥ | ╦ | ╧ | ╨ | ╩ | ╪ | ╫ | ╬ | ╭ | ╮ | ╯
257x | U+257x | ╰ | ╱ | ╲ | ╳ | ╴ | ╵ | ╶ | ╷ | ╸ | ╹ | ╺ | ╻ | ╼ | ╽ | ╾ | ╿
258x | U+258x | ▀ | ▁ | ▂ | ▃ | ▄ | ▅ | ▆ | ▇ | █ | ▉ | ▊ | ▋ | ▌ | ▍ | ▎ | ▏ | Block Elements | 32
259x | U+259x | ▐ | ░ | ▒ | ▓ | ▔ | ▕ | ▖ | ▗ | ▘ | ▙ | ▚ | ▛ | ▜ | ▝ | ▞ | ▟ | U+2580..U+259F
1FB0x | U+1FB0x | 🬀 | 🬁 | 🬂 | 🬃 | 🬄 | 🬅 | 🬆 | 🬇 | 🬈 | 🬉 | 🬊 | 🬋 | 🬌 | 🬍 | 🬎 | 🬏 | Symbols for Legacy Computing | 212
1FB1x | U+1FB1x | 🬐 | 🬑 | 🬒 | 🬓 | 🬔 | 🬕 | 🬖 | 🬗 | 🬘 | 🬙 | 🬚 | 🬛 | 🬜 | 🬝 | 🬞 | 🬟 | U+1FB00..U+1FBFF
1FB2x | U+1FB2x | 🬠 | 🬡 | 🬢 | 🬣 | 🬤 | 🬥 | 🬦 | 🬧 | 🬨 | 🬩 | 🬪 | 🬫 | 🬬 | 🬭 | 🬮 | 🬯
1FB3x | U+1FB3x | 🬰 | 🬱 | 🬲 | 🬳 | 🬴 | 🬵 | 🬶 | 🬷 | 🬸 | 🬹 | 🬺 | 🬻 | 🬼 | 🬽 | 🬾 | 🬿
1FB4x | U+1FB4x | 🭀 | 🭁 | 🭂 | 🭃 | 🭄 | 🭅 | 🭆 | 🭇 | 🭈 | 🭉 | 🭊 | 🭋 | 🭌 | 🭍 | 🭎 | 🭏
1FB5x | U+1FB5x | 🭐 | 🭑 | 🭒 | 🭓 | 🭔 | 🭕 | 🭖 | 🭗 | 🭘 | 🭙 | 🭚 | 🭛 | 🭜 | 🭝 | 🭞 | 🭟
1FB6x | U+1FB6x | 🭠 | 🭡 | 🭢 | 🭣 | 🭤 | 🭥 | 🭦 | 🭧 | 🭨 | 🭩 | 🭪 | 🭫 | 🭬 | 🭭 | 🭮 | 🭯
1FB7x | U+1FB7x | 🭰 | 🭱 | 🭲 | 🭳 | 🭴 | 🭵 | 🭶 | 🭷 | 🭸 | 🭹 | 🭺 | 🭻 | 🭼 | 🭽 | 🭾 | 🭿
1FB8x | U+1FB8x | 🮀 | 🮁 | 🮂 | 🮃 | 🮄 | 🮅 | 🮆 | 🮇 | 🮈 | 🮉 | 🮊 | 🮋 | 🮌 | 🮍 | 🮎 | 🮏
1FB9x | U+1FB9x | 🮐 | 🮑 | 🮒 |  | 🮔 | 🮕 | 🮖 | 🮗 | 🮘 | 🮙 | 🮚 | 🮛 | 🮜 | 🮝 | 🮞 | 🮟
1FBAx | U+1FBAx | 🮠 | 🮡 | 🮢 | 🮣 | 🮤 | 🮥 | 🮦 | 🮧 | 🮨 | 🮩 | 🮪 | 🮫 | 🮬 | 🮭 | 🮮 | 🮯
1FBBx | U+1FBBx | 🮰 | 🮱 | 🮲 | 🮳 | 🮴 | 🮵 | 🮶 | 🮷 | 🮸 | 🮹 | 🮺 | 🮻 | 🮼 | 🮽 | 🮾 | 🮿
1FBCx | U+1FBCx | 🯀 | 🯁 | 🯂 | 🯃 | 🯄 | 🯅 | 🯆 | 🯇 | 🯈 | 🯉 | 🯊
1FBDx | U+1FBDx
1FBEx | U+1FBEx
1FBFx | U+1FBFx | 🯰 | 🯱 | 🯲 | 🯳 | 🯴 | 🯵 | 🯶 | 🯷 | 🯸 | 🯹
25Ax | U+25Ax | ■ | □ | ▢ | ▣ | ▤ | ▥ | ▦ | ▧ | ▨ | ▩ | ▪ | ▫ | ▬ | ▭ | ▮ | ▯ | Geometric Shapes | 96
25Bx | U+25Bx | ▰ | ▱ | ▲ | △ | ▴ | ▵ | ▶ | ▷ | ▸ | ▹ | ► | ▻ | ▼ | ▽ | ▾ | ▿ | U+25A0–U+25FF
25Cx | U+25Cx | ◀ | ◁ | ◂ | ◃ | ◄ | ◅ | ◆ | ◇ | ◈ | ◉ | ◊ | ○ | ◌ | ◍ | ◎ | ●
25Dx | U+25Dx | ◐ | ◑ | ◒ | ◓ | ◔ | ◕ | ◖ | ◗ | ◘ | ◙ | ◚ | ◛ | ◜ | ◝ | ◞ | ◟
25Ex | U+25Ex | ◠ | ◡ | ◢ | ◣ | ◤ | ◥ | ◦ | ◧ | ◨ | ◩ | ◪ | ◫ | ◬ | ◭ | ◮ | ◯
25Fx | U+25Fx | ◰ | ◱ | ◲ | ◳ | ◴ | ◵ | ◶ | ◷ | ◸ | ◹ | ◺ | ◻ | ◼ | ◽ | ◾ | ◿
219x | U+219x | ← | ↑ | → | ↓ | ↔ | ↕ | ↖ | ↗ | ↘ | ↙ | ↚ | ↛ | ↜ | ↝ | ↞ | ↟ | Arrows | 128
21Ax | U+21Ax | ↠ | ↡ | ↢ | ↣ | ↤ | ↥ | ↦ | ↧ | ↨ | ↩ | ↪ | ↫ | ↬ | ↭ | ↮ | ↯ | U+2190–U+21FF
21Bx | U+21Bx | ↰ | ↱ | ↲ | ↳ | ↴ | ↵ | ↶ | ↷ | ↸ | ↹ | ↺ | ↻ | ↼ | ↽ | ↾ | ↿
21Cx | U+21Cx | ⇀ | ⇁ | ⇂ | ⇃ | ⇄ | ⇅ | ⇆ | ⇇ | ⇈ | ⇉ | ⇊ | ⇋ | ⇌ | ⇍ | ⇎ | ⇏
21Dx | U+21Dx | ⇐ | ⇑ | ⇒ | ⇓ | ⇔ | ⇕ | ⇖ | ⇗ | ⇘ | ⇙ | ⇚ | ⇛ | ⇜ | ⇝ | ⇞ | ⇟
21Ex | U+21Ex | ⇠ | ⇡ | ⇢ | ⇣ | ⇤ | ⇥ | ⇦ | ⇧ | ⇨ | ⇩ | ⇪ | ⇫ | ⇬ | ⇭ | ⇮ | ⇯
21Fx | U+21Fx | ⇰ | ⇱ | ⇲ | ⇳ | ⇴ | ⇵ | ⇶ | ⇷ | ⇸ | ⇹ | ⇺ | ⇻ | ⇼ | ⇽ | ⇾ | ⇿
27Fx | U+27Fx | ⟰ | ⟱ | ⟲ | ⟳ | ⟴ | ⟵ | ⟶ | ⟷ | ⟸ | ⟹ | ⟺ | ⟻ | ⟼ | ⟽ | ⟾ | ⟿ | Supplemental Arrows-A | 16
 |  |  |  |  |  |  |  |  |  |  |  |  |  |  |  |  |  | U+27F0–U+27FF
2B0x | U+2B0x | ⬀ | ⬁ | ⬂ | ⬃ | ⬄ | ⬅ | ⬆ | ⬇ | ⬈ | ⬉ | ⬊ | ⬋ | ⬌ | ⬍ | ⬎ | ⬏ | Miscellaneous Symbols and Arrows | 253
2B1x | U+2B1x | ⬐ | ⬑ | ⬒ | ⬓ | ⬔ | ⬕ | ⬖ | ⬗ | ⬘ | ⬙ | ⬚ | ⬛ | ⬜ | ⬝ | ⬞ | ⬟ | U+2B00–U+2BFF
2B2x | U+2B2x | ⬠ | ⬡ | ⬢ | ⬣ | ⬤ | ⬥ | ⬦ | ⬧ | ⬨ | ⬩ | ⬪ | ⬫ | ⬬ | ⬭ | ⬮ | ⬯
2B3x | U+2B3x | ⬰ | ⬱ | ⬲ | ⬳ | ⬴ | ⬵ | ⬶ | ⬷ | ⬸ | ⬹ | ⬺ | ⬻ | ⬼ | ⬽ | ⬾ | ⬿
2B4x | U+2B4x | ⭀ | ⭁ | ⭂ | ⭃ | ⭄ | ⭅ | ⭆ | ⭇ | ⭈ | ⭉ | ⭊ | ⭋ | ⭌ | ⭍ | ⭎ | ⭏
2B5x | U+2B5x | ⭐ | ⭑ | ⭒ | ⭓ | ⭔ | ⭕ | ⭖ | ⭗ | ⭘ | ⭙ | ⭚ | ⭛ | ⭜ | ⭝ | ⭞ | ⭟
2B6x | U+2B6x | ⭠ | ⭡ | ⭢ | ⭣ | ⭤ | ⭥ | ⭦ | ⭧ | ⭨ | ⭩ | ⭪ | ⭫ | ⭬ | ⭭ | ⭮ | ⭯
2B7x | U+2B7x | ⭰ | ⭱ | ⭲ | ⭳ |  |  | ⭶ | ⭷ | ⭸ | ⭹ | ⭺ | ⭻ | ⭼ | ⭽ | ⭾ | ⭿
2B8x | U+2B8x | ⮀ | ⮁ | ⮂ | ⮃ | ⮄ | ⮅ | ⮆ | ⮇ | ⮈ | ⮉ | ⮊ | ⮋ | ⮌ | ⮍ | ⮎ | ⮏
2B9x | U+2B9x | ⮐ | ⮑ | ⮒ | ⮓ | ⮔ | ⮕ |  | ⮗ | ⮘ | ⮙ | ⮚ | ⮛ | ⮜ | ⮝ | ⮞ | ⮟
2BAx | U+2BAx | ⮠ | ⮡ | ⮢ | ⮣ | ⮤ | ⮥ | ⮦ | ⮧ | ⮨ | ⮩ | ⮪ | ⮫ | ⮬ | ⮭ | ⮮ | ⮯
2BBx | U+2BBx | ⮰ | ⮱ | ⮲ | ⮳ | ⮴ | ⮵ | ⮶ | ⮷ | ⮸ | ⮹ | ⮺ | ⮻ | ⮼ | ⮽ | ⮾ | ⮿
2BCx | U+2BCx | ⯀ | ⯁ | ⯂ | ⯃ | ⯄ | ⯅ | ⯆ | ⯇ | ⯈ | ⯉ | ⯊ | ⯋ | ⯌ | ⯍ | ⯎ | ⯏
2BDx | U+2BDx | ⯐ | ⯑ | ⯒ | ⯓ | ⯔ | ⯕ | ⯖ | ⯗ | ⯘ | ⯙ | ⯚ | ⯛ | ⯜ | ⯝ | ⯞ | ⯟
2BEx | U+2BEx | ⯠ | ⯡ | ⯢ | ⯣ | ⯤ | ⯥ | ⯦ | ⯧ | ⯨ | ⯩ | ⯪ | ⯫ | ⯬ | ⯭ | ⯮ | ⯯
2BFx | U+2BFx | ⯰ | ⯱ | ⯲ | ⯳ | ⯴ | ⯵ | ⯶ | ⯷ | ⯸ | ⯹ | ⯺ | ⯻ | ⯼ | ⯽ | ⯾ | ⯿
260x | U+260x | ☀ | ☁ | ☂ | ☃ | ☄ | ★ | ☆ | ☇ | ☈ | ☉ | ☊ | ☋ | ☌ | ☍ | ☎ | ☏ | Miscellaneous Symbols | 256
261x | U+261x | ☐ | ☑ | ☒ | ☓ | ☔ | ☕ | ☖ | ☗ | ☘ | ☙ | ☚ | ☛ | ☜ | ☝ | ☞ | ☟ | U+2600..U+26FF
262x | U+262x | ☠ | ☡ | ☢ | ☣ | ☤ | ☥ | ☦ | ☧ | ☨ | ☩ | ☪ | ☫ | ☬ | ☭ | ☮ | ☯
263x | U+263x | ☰ | ☱ | ☲ | ☳ | ☴ | ☵ | ☶ | ☷ | ☸ | ☹ | ☺ | ☻ | ☼ | ☽ | ☾ | ☿
264x | U+264x | ♀ | ♁ | ♂ | ♃ | ♄ | ♅ | ♆ | ♇ | ♈ | ♉ | ♊ | ♋ | ♌ | ♍ | ♎ | ♏
265x | U+265x | ♐ | ♑ | ♒ | ♓ | ♔ | ♕ | ♖ | ♗ | ♘ | ♙ | ♚ | ♛ | ♜ | ♝ | ♞ | ♟
266x | U+266x | ♠ | ♡ | ♢ | ♣ | ♤ | ♥ | ♦ | ♧ | ♨ | ♩ | ♪ | ♫ | ♬ | ♭ | ♮ | ♯
267x | U+267x | ♰ | ♱ | ♲ | ♳ | ♴ | ♵ | ♶ | ♷ | ♸ | ♹ | ♺ | ♻ | ♼ | ♽ | ♾ | ♿
268x | U+268x | ⚀ | ⚁ | ⚂ | ⚃ | ⚄ | ⚅ | ⚆ | ⚇ | ⚈ | ⚉ | ⚊ | ⚋ | ⚌ | ⚍ | ⚎ | ⚏
269x | U+269x | ⚐ | ⚑ | ⚒ | ⚓ | ⚔ | ⚕ | ⚖ | ⚗ | ⚘ | ⚙ | ⚚ | ⚛ | ⚜ | ⚝ | ⚞ | ⚟
26Ax | U+26Ax | ⚠ | ⚡ | ⚢ | ⚣ | ⚤ | ⚥ | ⚦ | ⚧ | ⚨ | ⚩ | ⚪ | ⚫ | ⚬ | ⚭ | ⚮ | ⚯
26Bx | U+26Bx | ⚰ | ⚱ | ⚲ | ⚳ | ⚴ | ⚵ | ⚶ | ⚷ | ⚸ | ⚹ | ⚺ | ⚻ | ⚼ | ⚽ | ⚾ | ⚿
26Cx | U+26Cx | ⛀ | ⛁ | ⛂ | ⛃ | ⛄ | ⛅ | ⛆ | ⛇ | ⛈ | ⛉ | ⛊ | ⛋ | ⛌ | ⛍ | ⛎ | ⛏
26Dx | U+26Dx | ⛐ | ⛑ | ⛒ | ⛓ | ⛔ | ⛕ | ⛖ | ⛗ | ⛘ | ⛙ | ⛚ | ⛛ | ⛜ | ⛝ | ⛞ | ⛟
26Ex | U+26Ex | ⛠ | ⛡ | ⛢ | ⛣ | ⛤ | ⛥ | ⛦ | ⛧ | ⛨ | ⛩ | ⛪ | ⛫ | ⛬ | ⛭ | ⛮ | ⛯
26Fx | U+26Fx | ⛰ | ⛱ | ⛲ | ⛳ | ⛴ | ⛵ | ⛶ | ⛷ | ⛸ | ⛹ | ⛺ | ⛻ | ⛼ | ⛽ | ⛾ | ⛿
270x | U+270x | ✀ | ✁ | ✂ | ✃ | ✄ | ✅ | ✆ | ✇ | ✈ | ✉ | ✊ | ✋ | ✌ | ✍ | ✎ | ✏ | Dingbats | 192
271x | U+271x | ✐ | ✑ | ✒ | ✓ | ✔ | ✕ | ✖ | ✗ | ✘ | ✙ | ✚ | ✛ | ✜ | ✝ | ✞ | ✟ | U+2700..U+27BF
272x | U+272x | ✠ | ✡ | ✢ | ✣ | ✤ | ✥ | ✦ | ✧ | ✨ | ✩ | ✪ | ✫ | ✬ | ✭ | ✮ | ✯
273x | U+273x | ✰ | ✱ | ✲ | ✳ | ✴ | ✵ | ✶ | ✷ | ✸ | ✹ | ✺ | ✻ | ✼ | ✽ | ✾ | ✿
274x | U+274x | ❀ | ❁ | ❂ | ❃ | ❄ | ❅ | ❆ | ❇ | ❈ | ❉ | ❊ | ❋ | ❌ | ❍ | ❎ | ❏
275x | U+275x | ❐ | ❑ | ❒ | ❓ | ❔ | ❕ | ❖ | ❗ | ❘ | ❙ | ❚ | ❛ | ❜ | ❝ | ❞ | ❟
276x | U+276x | ❠ | ❡ | ❢ | ❣ | ❤ | ❥ | ❦ | ❧ | ❨ | ❩ | ❪ | ❫ | ❬ | ❭ | ❮ | ❯
277x | U+277x | ❰ | ❱ | ❲ | ❳ | ❴ | ❵ | ❶ | ❷ | ❸ | ❹ | ❺ | ❻ | ❼ | ❽ | ❾ | ❿
278x | U+278x | ➀ | ➁ | ➂ | ➃ | ➄ | ➅ | ➆ | ➇ | ➈ | ➉ | ➊ | ➋ | ➌ | ➍ | ➎ | ➏
279x | U+279x | ➐ | ➑ | ➒ | ➓ | ➔ | ➕ | ➖ | ➗ | ➘ | ➙ | ➚ | ➛ | ➜ | ➝ | ➞ | ➟
27Ax | U+27Ax | ➠ | ➡ | ➢ | ➣ | ➤ | ➥ | ➦ | ➧ | ➨ | ➩ | ➪ | ➫ | ➬ | ➭ | ➮ | ➯
27Bx | U+27Bx | ➰ | ➱ | ➲ | ➳ | ➴ | ➵ | ➶ | ➷ | ➸ | ➹ | ➺ | ➻ | ➼ | ➽ | ➾ | ➿
1D10x | U+1D10x | 𝄀 | 𝄁 | 𝄂 | 𝄃 | 𝄄 | 𝄅 | 𝄆 | 𝄇 | 𝄈 | 𝄉 | 𝄊 | 𝄋 | 𝄌 | 𝄍 | 𝄎 | 𝄏 | Musical Symbols | 256
1D11x | U+1D11x | 𝄐 | 𝄑 | 𝄒 | 𝄓 | 𝄔 | 𝄕 | 𝄖 | 𝄗 | 𝄘 | 𝄙 | 𝄚 | 𝄛 | 𝄜 | 𝄝 | 𝄞 | 𝄟 | U+1D100..U+1D1FF
1D12x | U+1D12x | 𝄠 | 𝄡 | 𝄢 | 𝄣 | 𝄤 | 𝄥 | 𝄦 |  |  | 𝄩 | 𝄪 | 𝄫 | 𝄬 | 𝄭 | 𝄮 | 𝄯
1D13x | U+1D13x | 𝄰 | 𝄱 | 𝄲 | 𝄳 | 𝄴 | 𝄵 | 𝄶 | 𝄷 | 𝄸 | 𝄹 | 𝄺 | 𝄻 | 𝄼 | 𝄽 | 𝄾 | 𝄿
1D14x | U+1D14x | 𝅀 | 𝅁 | 𝅂 | 𝅃 | 𝅄 | 𝅅 | 𝅆 | 𝅇 | 𝅈 | 𝅉 | 𝅊 | 𝅋 | 𝅌 | 𝅍 | 𝅎 | 𝅏
1D15x | U+1D15x | 𝅐 | 𝅑 | 𝅒 | 𝅓 | 𝅔 | 𝅕 | 𝅖 | 𝅗 | 𝅘 | NULL | 𝅚 | 𝅛 | 𝅜 | 𝅝 | 𝅗𝅥 | 𝅘𝅥
 |  |  |  |  |  |  |  |  |  |  | NOTE
 |  |  |  |  |  |  |  |  |  |  | HEAD
1D16x | U+1D16x | 𝅘𝅥𝅮 | 𝅘𝅥𝅯 | 𝅘𝅥𝅰 | 𝅘𝅥𝅱 | 𝅘𝅥𝅲 | 𝅥 | 𝅦 | 𝅧 | 𝅨 | 𝅩 | 𝅪 | 𝅫 | 𝅬 | 𝅭 | 𝅮 | 𝅯
1D17x | U+1D17x | 𝅰 | 𝅱 | 𝅲 | BEGIN | END | BEGIN | END | BEGIN | END | BEGIN | END | 𝅻 | 𝅼 | 𝅽 | 𝅾 | 𝅿
 |  |  |  |  | BEAM | BEAM | TIE | TIE | SLUR | SLUR | PHR. | PHR.
1D18x | U+1D18x | 𝆀 | 𝆁 | 𝆂 | 𝆃 | 𝆄 | 𝆅 | 𝆆 | 𝆇 | 𝆈 | 𝆉 | 𝆊 | 𝆋 | 𝆌 | 𝆍 | 𝆎 | 𝆏
1D19x | U+1D19x | 𝆐 | 𝆑 | 𝆒 | 𝆓 | 𝆔 | 𝆕 | 𝆖 | 𝆗 | 𝆘 | 𝆙 | 𝆚 | 𝆛 | 𝆜 | 𝆝 | 𝆞 | 𝆟
1D1Ax | U+1D1Ax | 𝆠 | 𝆡 | 𝆢 | 𝆣 | 𝆤 | 𝆥 | 𝆦 | 𝆧 | 𝆨 | 𝆩 | 𝆪 | 𝆫 | 𝆬 | 𝆭 | 𝆮 | 𝆯
1D1Bx | U+1D1Bx | 𝆰 | 𝆱 | 𝆲 | 𝆳 | 𝆴 | 𝆵 | 𝆶 | 𝆷 | 𝆸 | 𝆹 | 𝆺 | 𝆹𝅥 | 𝆺𝅥 | 𝆹𝅥𝅮 | 𝆺𝅥𝅮 | 𝆹𝅥𝅯
1D1Cx | U+1D1Cx | 𝆺𝅥𝅯 | 𝇁 | 𝇂 | 𝇃 | 𝇄 | 𝇅 | 𝇆 | 𝇇 | 𝇈 | 𝇉 | 𝇊 | 𝇋 | 𝇌 | 𝇍 | 𝇎 | 𝇏
1D1Dx | U+1D1Dx | 𝇐 | 𝇑 | 𝇒 | 𝇓 | 𝇔 | 𝇕 | 𝇖 | 𝇗 | 𝇘 | 𝇙 | 𝇚 | 𝇛 | 𝇜 | 𝇝 | 𝇞 | 𝇟
1D1Ex | U+1D1Ex | 𝇠 | 𝇡 | 𝇢 | 𝇣 | 𝇤 | 𝇥 | 𝇦 | 𝇧 | 𝇨 | 𝇩 | 𝇪
1D1Fx | U+1D1Fx
280x | U+280x | ⠀ | ⠁ | ⠂ | ⠃ | ⠄ | ⠅ | ⠆ | ⠇ | ⠈ | ⠉ | ⠊ | ⠋ | ⠌ | ⠍ | ⠎ | ⠏ | Braille Patterns | 256
281x | U+281x | ⠐ | ⠑ | ⠒ | ⠓ | ⠔ | ⠕ | ⠖ | ⠗ | ⠘ | ⠙ | ⠚ | ⠛ | ⠜ | ⠝ | ⠞ | ⠟ | U+2800..U+28FF
282x | U+282x | ⠠ | ⠡ | ⠢ | ⠣ | ⠤ | ⠥ | ⠦ | ⠧ | ⠨ | ⠩ | ⠪ | ⠫ | ⠬ | ⠭ | ⠮ | ⠯
283x | U+283x | ⠰ | ⠱ | ⠲ | ⠳ | ⠴ | ⠵ | ⠶ | ⠷ | ⠸ | ⠹ | ⠺ | ⠻ | ⠼ | ⠽ | ⠾ | ⠿
284x | U+284x | ⡀ | ⡁ | ⡂ | ⡃ | ⡄ | ⡅ | ⡆ | ⡇ | ⡈ | ⡉ | ⡊ | ⡋ | ⡌ | ⡍ | ⡎ | ⡏
285x | U+285x | ⡐ | ⡑ | ⡒ | ⡓ | ⡔ | ⡕ | ⡖ | ⡗ | ⡘ | ⡙ | ⡚ | ⡛ | ⡜ | ⡝ | ⡞ | ⡟
286x | U+286x | ⡠ | ⡡ | ⡢ | ⡣ | ⡤ | ⡥ | ⡦ | ⡧ | ⡨ | ⡩ | ⡪ | ⡫ | ⡬ | ⡭ | ⡮ | ⡯
287x | U+287x | ⡰ | ⡱ | ⡲ | ⡳ | ⡴ | ⡵ | ⡶ | ⡷ | ⡸ | ⡹ | ⡺ | ⡻ | ⡼ | ⡽ | ⡾ | ⡿
288x | U+288x | ⢀ | ⢁ | ⢂ | ⢃ | ⢄ | ⢅ | ⢆ | ⢇ | ⢈ | ⢉ | ⢊ | ⢋ | ⢌ | ⢍ | ⢎ | ⢏
289x | U+289x | ⢐ | ⢑ | ⢒ | ⢓ | ⢔ | ⢕ | ⢖ | ⢗ | ⢘ | ⢙ | ⢚ | ⢛ | ⢜ | ⢝ | ⢞ | ⢟
28Ax | U+28Ax | ⢠ | ⢡ | ⢢ | ⢣ | ⢤ | ⢥ | ⢦ | ⢧ | ⢨ | ⢩ | ⢪ | ⢫ | ⢬ | ⢭ | ⢮ | ⢯
28Bx | U+28Bx | ⢰ | ⢱ | ⢲ | ⢳ | ⢴ | ⢵ | ⢶ | ⢷ | ⢸ | ⢹ | ⢺ | ⢻ | ⢼ | ⢽ | ⢾ | ⢿
28Cx | U+28Cx | ⣀ | ⣁ | ⣂ | ⣃ | ⣄ | ⣅ | ⣆ | ⣇ | ⣈ | ⣉ | ⣊ | ⣋ | ⣌ | ⣍ | ⣎ | ⣏
28Dx | U+28Dx | ⣐ | ⣑ | ⣒ | ⣓ | ⣔ | ⣕ | ⣖ | ⣗ | ⣘ | ⣙ | ⣚ | ⣛ | ⣜ | ⣝ | ⣞ | ⣟
28Ex | U+28Ex | ⣠ | ⣡ | ⣢ | ⣣ | ⣤ | ⣥ | ⣦ | ⣧ | ⣨ | ⣩ | ⣪ | ⣫ | ⣬ | ⣭ | ⣮ | ⣯
28Fx | U+28Fx | ⣰ | ⣱ | ⣲ | ⣳ | ⣴ | ⣵ | ⣶ | ⣷ | ⣸ | ⣹ | ⣺ | ⣻ | ⣼ | ⣽ | ⣾ | ⣿
1F65x | U+1F65x | 🙐 | 🙑 | 🙒 | 🙓 | 🙔 | 🙕 | 🙖 | 🙗 | 🙘 | 🙙 | 🙚 | 🙛 | 🙜 | 🙝 | 🙞 | 🙟 | Ornamental Dingbats | 48
1F66x | U+1F66x | 🙠 | 🙡 | 🙢 | 🙣 | 🙤 | 🙥 | 🙦 | 🙧 | 🙨 | 🙩 | 🙪 | 🙫 | 🙬 | 🙭 | 🙮 | 🙯 | U+1F650..U+1F67F
1F67x | U+1F67x | 🙰 | 🙱 | 🙲 | 🙳 | 🙴 | 🙵 | 🙶 | 🙷 | 🙸 | 🙹 | 🙺 | 🙻 | 🙼 | 🙽 | 🙾 | 🙿
1F70x | U+1F70x | 🜀 | 🜁 | 🜂 | 🜃 | 🜄 | 🜅 | 🜆 | 🜇 | 🜈 | 🜉 | 🜊 | 🜋 | 🜌 | 🜍 | 🜎 | 🜏 | Alchemical Symbols | 124
1F71x | U+1F71x | 🜐 | 🜑 | 🜒 | 🜓 | 🜔 | 🜕 | 🜖 | 🜗 | 🜘 | 🜙 | 🜚 | 🜛 | 🜜 | 🜝 | 🜞 | 🜟 | U+1F700..U+1F77F
1F72x | U+1F72x | 🜠 | 🜡 | 🜢 | 🜣 | 🜤 | 🜥 | 🜦 | 🜧 | 🜨 | 🜩 | 🜪 | 🜫 | 🜬 | 🜭 | 🜮 | 🜯
1F73x | U+1F73x | 🜰 | 🜱 | 🜲 | 🜳 | 🜴 | 🜵 | 🜶 | 🜷 | 🜸 | 🜹 | 🜺 | 🜻 | 🜼 | 🜽 | 🜾 | 🜿
1F74x | U+1F74x | 🝀 | 🝁 | 🝂 | 🝃 | 🝄 | 🝅 | 🝆 | 🝇 | 🝈 | 🝉 | 🝊 | 🝋 | 🝌 | 🝍 | 🝎 | 🝏
1F75x | U+1F75x | 🝐 | 🝑 | 🝒 | 🝓 | 🝔 | 🝕 | 🝖 | 🝗 | 🝘 | 🝙 | 🝚 | 🝛 | 🝜 | 🝝 | 🝞 | 🝟
1F76x | U+1F76x | 🝠 | 🝡 | 🝢 | 🝣 | 🝤 | 🝥 | 🝦 | 🝧 | 🝨 | 🝩 | 🝪 | 🝫 | 🝬 | 🝭 | 🝮 | 🝯
1F77x | U+1F77x | 🝰 | 🝱 | 🝲 | 🝳 | 🝴 | 🝵 | 🝶 |  |  |  |  | 🝻 | 🝼 | 🝽 | 🝾 | 🝿
1F78x | U+1F78x | 🞀 | 🞁 | 🞂 | 🞃 | 🞄 | 🞅 | 🞆 | 🞇 | 🞈 | 🞉 | 🞊 | 🞋 | 🞌 | 🞍 | 🞎 | 🞏 | Geometric Shapes Extended | 103
1F79x | U+1F79x | 🞐 | 🞑 | 🞒 | 🞓 | 🞔 | 🞕 | 🞖 | 🞗 | 🞘 | 🞙 | 🞚 | 🞛 | 🞜 | 🞝 | 🞞 | 🞟 | U+1F780..U+1F7FF
1F7Ax | U+1F7Ax | 🞠 | 🞡 | 🞢 | 🞣 | 🞤 | 🞥 | 🞦 | 🞧 | 🞨 | 🞩 | 🞪 | 🞫 | 🞬 | 🞭 | 🞮 | 🞯
1F7Bx | U+1F7Bx | 🞰 | 🞱 | 🞲 | 🞳 | 🞴 | 🞵 | 🞶 | 🞷 | 🞸 | 🞹 | 🞺 | 🞻 | 🞼 | 🞽 | 🞾 | 🞿
1F7Cx | U+1F7Cx | 🟀 | 🟁 | 🟂 | 🟃 | 🟄 | 🟅 | 🟆 | 🟇 | 🟈 | 🟉 | 🟊 | 🟋 | 🟌 | 🟍 | 🟎 | 🟏
1F7Dx | U+1F7Dx | 🟐 | 🟑 | 🟒 | 🟓 | 🟔 | 🟕 | 🟖 | 🟗 | 🟘 | 🟙
1F7Ex | U+1F7Ex | 🟠 | 🟡 | 🟢 | 🟣 | 🟤 | 🟥 | 🟦 | 🟧 | 🟨 | 🟩 | 🟪 | 🟫
1F7Fx | U+1F7Fx | 🟰
1F60x | U+1F60x | 😀 | 😁 | 😂 | 😃 | 😄 | 😅 | 😆 | 😇 | 😈 | 😉 | 😊 | 😋 | 😌 | 😍 | 😎 | 😏 | Emoticons | 80
1F61x | U+1F61x | 😐 | 😑 | 😒 | 😓 | 😔 | 😕 | 😖 | 😗 | 😘 | 😙 | 😚 | 😛 | 😜 | 😝 | 😞 | 😟 | U+1F600..U+1F64F
1F62x | U+1F62x | 😠 | 😡 | 😢 | 😣 | 😤 | 😥 | 😦 | 😧 | 😨 | 😩 | 😪 | 😫 | 😬 | 😭 | 😮 | 😯
1F63x | U+1F63x | 😰 | 😱 | 😲 | 😳 | 😴 | 😵 | 😶 | 😷 | 😸 | 😹 | 😺 | 😻 | 😼 | 😽 | 😾 | 😿
1F64x | U+1F64x | 🙀 | 🙁 | 🙂 | 🙃 | 🙄 | 🙅 | 🙆 | 🙇 | 🙈 | 🙉 | 🙊 | 🙋 | 🙌 | 🙍 | 🙎 | 🙏
1F30x | U+1F30x | 🌀 | 🌁 | 🌂 | 🌃 | 🌄 | 🌅 | 🌆 | 🌇 | 🌈 | 🌉 | 🌊 | 🌋 | 🌌 | 🌍 | 🌎 | 🌏 | Miscellaneous Symbols and Pictographs | 768
1F31x | U+1F31x | 🌐 | 🌑 | 🌒 | 🌓 | 🌔 | 🌕 | 🌖 | 🌗 | 🌘 | 🌙 | 🌚 | 🌛 | 🌜 | 🌝 | 🌞 | 🌟 | U+1F300..U+1F5FF
1F32x | U+1F32x | 🌠 | 🌡 | 🌢 | 🌣 | 🌤 | 🌥 | 🌦 | 🌧 | 🌨 | 🌩 | 🌪 | 🌫 | 🌬 | 🌭 | 🌮 | 🌯
1F33x | U+1F33x | 🌰 | 🌱 | 🌲 | 🌳 | 🌴 | 🌵 | 🌶 | 🌷 | 🌸 | 🌹 | 🌺 | 🌻 | 🌼 | 🌽 | 🌾 | 🌿
1F34x | U+1F34x | 🍀 | 🍁 | 🍂 | 🍃 | 🍄 | 🍅 | 🍆 | 🍇 | 🍈 | 🍉 | 🍊 | 🍋 | 🍌 | 🍍 | 🍎 | 🍏
1F35x | U+1F35x | 🍐 | 🍑 | 🍒 | 🍓 | 🍔 | 🍕 | 🍖 | 🍗 | 🍘 | 🍙 | 🍚 | 🍛 | 🍜 | 🍝 | 🍞 | 🍟
1F36x | U+1F36x | 🍠 | 🍡 | 🍢 | 🍣 | 🍤 | 🍥 | 🍦 | 🍧 | 🍨 | 🍩 | 🍪 | 🍫 | 🍬 | 🍭 | 🍮 | 🍯
1F37x | U+1F37x | 🍰 | 🍱 | 🍲 | 🍳 | 🍴 | 🍵 | 🍶 | 🍷 | 🍸 | 🍹 | 🍺 | 🍻 | 🍼 | 🍽 | 🍾 | 🍿
1F38x | U+1F38x | 🎀 | 🎁 | 🎂 | 🎃 | 🎄 | 🎅 | 🎆 | 🎇 | 🎈 | 🎉 | 🎊 | 🎋 | 🎌 | 🎍 | 🎎 | 🎏
1F39x | U+1F39x | 🎐 | 🎑 | 🎒 | 🎓 | 🎔 | 🎕 | 🎖 | 🎗 | 🎘 | 🎙 | 🎚 | 🎛 | 🎜 | 🎝 | 🎞 | 🎟
1F3Ax | U+1F3Ax | 🎠 | 🎡 | 🎢 | 🎣 | 🎤 | 🎥 | 🎦 | 🎧 | 🎨 | 🎩 | 🎪 | 🎫 | 🎬 | 🎭 | 🎮 | 🎯
1F3Bx | U+1F3Bx | 🎰 | 🎱 | 🎲 | 🎳 | 🎴 | 🎵 | 🎶 | 🎷 | 🎸 | 🎹 | 🎺 | 🎻 | 🎼 | 🎽 | 🎾 | 🎿
1F3Cx | U+1F3Cx | 🏀 | 🏁 | 🏂 | 🏃 | 🏄 | 🏅 | 🏆 | 🏇 | 🏈 | 🏉 | 🏊 | 🏋 | 🏌 | 🏍 | 🏎 | 🏏
1F3Dx | U+1F3Dx | 🏐 | 🏑 | 🏒 | 🏓 | 🏔 | 🏕 | 🏖 | 🏗 | 🏘 | 🏙 | 🏚 | 🏛 | 🏜 | 🏝 | 🏞 | 🏟
1F3Ex | U+1F3Ex | 🏠 | 🏡 | 🏢 | 🏣 | 🏤 | 🏥 | 🏦 | 🏧 | 🏨 | 🏩 | 🏪 | 🏫 | 🏬 | 🏭 | 🏮 | 🏯
1F3Fx | U+1F3Fx | 🏰 | 🏱 | 🏲 | 🏳 | 🏴 | 🏵 | 🏶 | 🏷 | 🏸 | 🏹 | 🏺 | 🏻 | 🏼 | 🏽 | 🏾 | 🏿
1F40x | U+1F40x | 🐀 | 🐁 | 🐂 | 🐃 | 🐄 | 🐅 | 🐆 | 🐇 | 🐈 | 🐉 | 🐊 | 🐋 | 🐌 | 🐍 | 🐎 | 🐏
1F41x | U+1F41x | 🐐 | 🐑 | 🐒 | 🐓 | 🐔 | 🐕 | 🐖 | 🐗 | 🐘 | 🐙 | 🐚 | 🐛 | 🐜 | 🐝 | 🐞 | 🐟
1F42x | U+1F42x | 🐠 | 🐡 | 🐢 | 🐣 | 🐤 | 🐥 | 🐦 | 🐧 | 🐨 | 🐩 | 🐪 | 🐫 | 🐬 | 🐭 | 🐮 | 🐯
1F43x | U+1F43x | 🐰 | 🐱 | 🐲 | 🐳 | 🐴 | 🐵 | 🐶 | 🐷 | 🐸 | 🐹 | 🐺 | 🐻 | 🐼 | 🐽 | 🐾 | 🐿
1F44x | U+1F44x | 👀 | 👁 | 👂 | 👃 | 👄 | 👅 | 👆 | 👇 | 👈 | 👉 | 👊 | 👋 | 👌 | 👍 | 👎 | 👏
1F45x | U+1F45x | 👐 | 👑 | 👒 | 👓 | 👔 | 👕 | 👖 | 👗 | 👘 | 👙 | 👚 | 👛 | 👜 | 👝 | 👞 | 👟
1F46x | U+1F46x | 👠 | 👡 | 👢 | 👣 | 👤 | 👥 | 👦 | 👧 | 👨 | 👩 | 👪 | 👫 | 👬 | 👭 | 👮 | 👯
1F47x | U+1F47x | 👰 | 👱 | 👲 | 👳 | 👴 | 👵 | 👶 | 👷 | 👸 | 👹 | 👺 | 👻 | 👼 | 👽 | 👾 | 👿
1F48x | U+1F48x | 💀 | 💁 | 💂 | 💃 | 💄 | 💅 | 💆 | 💇 | 💈 | 💉 | 💊 | 💋 | 💌 | 💍 | 💎 | 💏
1F49x | U+1F49x | 💐 | 💑 | 💒 | 💓 | 💔 | 💕 | 💖 | 💗 | 💘 | 💙 | 💚 | 💛 | 💜 | 💝 | 💞 | 💟
1F4Ax | U+1F4Ax | 💠 | 💡 | 💢 | 💣 | 💤 | 💥 | 💦 | 💧 | 💨 | 💩 | 💪 | 💫 | 💬 | 💭 | 💮 | 💯
1F4Bx | U+1F4Bx | 💰 | 💱 | 💲 | 💳 | 💴 | 💵 | 💶 | 💷 | 💸 | 💹 | 💺 | 💻 | 💼 | 💽 | 💾 | 💿
1F4Cx | U+1F4Cx | 📀 | 📁 | 📂 | 📃 | 📄 | 📅 | 📆 | 📇 | 📈 | 📉 | 📊 | 📋 | 📌 | 📍 | 📎 | 📏
1F4Dx | U+1F4Dx | 📐 | 📑 | 📒 | 📓 | 📔 | 📕 | 📖 | 📗 | 📘 | 📙 | 📚 | 📛 | 📜 | 📝 | 📞 | 📟
1F4Ex | U+1F4Ex | 📠 | 📡 | 📢 | 📣 | 📤 | 📥 | 📦 | 📧 | 📨 | 📩 | 📪 | 📫 | 📬 | 📭 | 📮 | 📯
1F4Fx | U+1F4Fx | 📰 | 📱 | 📲 | 📳 | 📴 | 📵 | 📶 | 📷 | 📸 | 📹 | 📺 | 📻 | 📼 | 📽 | 📾 | 📿
1F50x | U+1F50x | 🔀 | 🔁 | 🔂 | 🔃 | 🔄 | 🔅 | 🔆 | 🔇 | 🔈 | 🔉 | 🔊 | 🔋 | 🔌 | 🔍 | 🔎 | 🔏
1F51x | U+1F51x | 🔐 | 🔑 | 🔒 | 🔓 | 🔔 | 🔕 | 🔖 | 🔗 | 🔘 | 🔙 | 🔚 | 🔛 | 🔜 | 🔝 | 🔞 | 🔟
1F52x | U+1F52x | 🔠 | 🔡 | 🔢 | 🔣 | 🔤 | 🔥 | 🔦 | 🔧 | 🔨 | 🔩 | 🔪 | 🔫 | 🔬 | 🔭 | 🔮 | 🔯
1F53x | U+1F53x | 🔰 | 🔱 | 🔲 | 🔳 | 🔴 | 🔵 | 🔶 | 🔷 | 🔸 | 🔹 | 🔺 | 🔻 | 🔼 | 🔽 | 🔾 | 🔿
1F54x | U+1F54x | 🕀 | 🕁 | 🕂 | 🕃 | 🕄 | 🕅 | 🕆 | 🕇 | 🕈 | 🕉 | 🕊 | 🕋 | 🕌 | 🕍 | 🕎 | 🕏
1F55x | U+1F55x | 🕐 | 🕑 | 🕒 | 🕓 | 🕔 | 🕕 | 🕖 | 🕗 | 🕘 | 🕙 | 🕚 | 🕛 | 🕜 | 🕝 | 🕞 | 🕟
1F56x | U+1F56x | 🕠 | 🕡 | 🕢 | 🕣 | 🕤 | 🕥 | 🕦 | 🕧 | 🕨 | 🕩 | 🕪 | 🕫 | 🕬 | 🕭 | 🕮 | 🕯
1F57x | U+1F57x | 🕰 | 🕱 | 🕲 | 🕳 | 🕴 | 🕵 | 🕶 | 🕷 | 🕸 | 🕹 | 🕺 | 🕻 | 🕼 | 🕽 | 🕾 | 🕿
1F58x | U+1F58x | 🖀 | 🖁 | 🖂 | 🖃 | 🖄 | 🖅 | 🖆 | 🖇 | 🖈 | 🖉 | 🖊 | 🖋 | 🖌 | 🖍 | 🖎 | 🖏
1F59x | U+1F59x | 🖐 | 🖑 | 🖒 | 🖓 | 🖔 | 🖕 | 🖖 | 🖗 | 🖘 | 🖙 | 🖚 | 🖛 | 🖜 | 🖝 | 🖞 | 🖟
1F5Ax | U+1F5Ax | 🖠 | 🖡 | 🖢 | 🖣 | 🖤 | 🖥 | 🖦 | 🖧 | 🖨 | 🖩 | 🖪 | 🖫 | 🖬 | 🖭 | 🖮 | 🖯
1F5Bx | U+1F5Bx | 🖰 | 🖱 | 🖲 | 🖳 | 🖴 | 🖵 | 🖶 | 🖷 | 🖸 | 🖹 | 🖺 | 🖻 | 🖼 | 🖽 | 🖾 | 🖿
1F5Cx | U+1F5Cx | 🗀 | 🗁 | 🗂 | 🗃 | 🗄 | 🗅 | 🗆 | 🗇 | 🗈 | 🗉 | 🗊 | 🗋 | 🗌 | 🗍 | 🗎 | 🗏
1F5Dx | U+1F5Dx | 🗐 | 🗑 | 🗒 | 🗓 | 🗔 | 🗕 | 🗖 | 🗗 | 🗘 | 🗙 | 🗚 | 🗛 | 🗜 | 🗝 | 🗞 | 🗟
1F5Ex | U+1F5Ex | 🗠 | 🗡 | 🗢 | 🗣 | 🗤 | 🗥 | 🗦 | 🗧 | 🗨 | 🗩 | 🗪 | 🗫 | 🗬 | 🗭 | 🗮 | 🗯
1F5Fx | U+1F5Fx | 🗰 | 🗱 | 🗲 | 🗳 | 🗴 | 🗵 | 🗶 | 🗷 | 🗸 | 🗹 | 🗺 | 🗻 | 🗼 | 🗽 | 🗾 | 🗿
1F90x | U+1F90x | 🤀 | 🤁 | 🤂 | 🤃 | 🤄 | 🤅 | 🤆 | 🤇 | 🤈 | 🤉 | 🤊 | 🤋 | 🤌 | 🤍 | 🤎 | 🤏 | Supplemental Symbols and Pictographs | 256
1F91x | U+1F91x | 🤐 | 🤑 | 🤒 | 🤓 | 🤔 | 🤕 | 🤖 | 🤗 | 🤘 | 🤙 | 🤚 | 🤛 | 🤜 | 🤝 | 🤞 | 🤟 | U+1F900..U+1F9FF
1F92x | U+1F92x | 🤠 | 🤡 | 🤢 | 🤣 | 🤤 | 🤥 | 🤦 | 🤧 | 🤨 | 🤩 | 🤪 | 🤫 | 🤬 | 🤭 | 🤮 | 🤯
1F93x | U+1F93x | 🤰 | 🤱 | 🤲 | 🤳 | 🤴 | 🤵 | 🤶 | 🤷 | 🤸 | 🤹 | 🤺 | 🤻 | 🤼 | 🤽 | 🤾 | 🤿
1F94x | U+1F94x | 🥀 | 🥁 | 🥂 | 🥃 | 🥄 | 🥅 | 🥆 | 🥇 | 🥈 | 🥉 | 🥊 | 🥋 | 🥌 | 🥍 | 🥎 | 🥏
1F95x | U+1F95x | 🥐 | 🥑 | 🥒 | 🥓 | 🥔 | 🥕 | 🥖 | 🥗 | 🥘 | 🥙 | 🥚 | 🥛 | 🥜 | 🥝 | 🥞 | 🥟
1F96x | U+1F96x | 🥠 | 🥡 | 🥢 | 🥣 | 🥤 | 🥥 | 🥦 | 🥧 | 🥨 | 🥩 | 🥪 | 🥫 | 🥬 | 🥭 | 🥮 | 🥯
1F97x | U+1F97x | 🥰 | 🥱 | 🥲 | 🥳 | 🥴 | 🥵 | 🥶 | 🥷 | 🥸 | 🥹 | 🥺 | 🥻 | 🥼 | 🥽 | 🥾 | 🥿
1F98x | U+1F98x | 🦀 | 🦁 | 🦂 | 🦃 | 🦄 | 🦅 | 🦆 | 🦇 | 🦈 | 🦉 | 🦊 | 🦋 | 🦌 | 🦍 | 🦎 | 🦏
1F99x | U+1F99x | 🦐 | 🦑 | 🦒 | 🦓 | 🦔 | 🦕 | 🦖 | 🦗 | 🦘 | 🦙 | 🦚 | 🦛 | 🦜 | 🦝 | 🦞 | 🦟
1F9Ax | U+1F9Ax | 🦠 | 🦡 | 🦢 | 🦣 | 🦤 | 🦥 | 🦦 | 🦧 | 🦨 | 🦩 | 🦪 | 🦫 | 🦬 | 🦭 | 🦮 | 🦯
1F9Bx | U+1F9Bx | 🦰 | 🦱 | 🦲 | 🦳 | 🦴 | 🦵 | 🦶 | 🦷 | 🦸 | 🦹 | 🦺 | 🦻 | 🦼 | 🦽 | 🦾 | 🦿
1F9Cx | U+1F9Cx | 🧀 | 🧁 | 🧂 | 🧃 | 🧄 | 🧅 | 🧆 | 🧇 | 🧈 | 🧉 | 🧊 | 🧋 | 🧌 | 🧍 | 🧎 | 🧏
1F9Dx | U+1F9Dx | 🧐 | 🧑 | 🧒 | 🧓 | 🧔 | 🧕 | 🧖 | 🧗 | 🧘 | 🧙 | 🧚 | 🧛 | 🧜 | 🧝 | 🧞 | 🧟
1F9Ex | U+1F9Ex | 🧠 | 🧡 | 🧢 | 🧣 | 🧤 | 🧥 | 🧦 | 🧧 | 🧨 | 🧩 | 🧪 | 🧫 | 🧬 | 🧭 | 🧮 | 🧯
1F9Fx | U+1F9Fx | 🧰 | 🧱 | 🧲 | 🧳 | 🧴 | 🧵 | 🧶 | 🧷 | 🧸 | 🧹 | 🧺 | 🧻 | 🧼 | 🧽 | 🧾 | 🧿
1FA7x | U+1FA7x | 🩰 | 🩱 | 🩲 | 🩳 | 🩴 | 🩵 | 🩶 | 🩷 | 🩸 | 🩹 | 🩺 | 🩻 | 🩼 |  |  |  | Symbols and Pictographs Extended-A | 107
1FA8x | U+1FA8x | 🪀 | 🪁 | 🪂 | 🪃 | 🪄 | 🪅 | 🪆 | 🪇 | 🪈 |  |  |  |  |  |  |  | U+1FA70..U+1FAFF
1FA9x | U+1FA9x | 🪐 | 🪑 | 🪒 | 🪓 | 🪔 | 🪕 | 🪖 | 🪗 | 🪘 | 🪙 | 🪚 | 🪛 | 🪜 | 🪝 | 🪞 | 🪟
1FAAx | U+1FAAx | 🪠 | 🪡 | 🪢 | 🪣 | 🪤 | 🪥 | 🪦 | 🪧 | 🪨 | 🪩 | 🪪 | 🪫 | 🪬 | 🪭 | 🪮 | 🪯
1FABx | U+1FABx | 🪰 | 🪱 | 🪲 | 🪳 | 🪴 | 🪵 | 🪶 | 🪷 | 🪸 | 🪹 | 🪺 | 🪻 | 🪼 | 🪽 |  | 🪿
1FACx | U+1FACx | 🫀 | 🫁 | 🫂 | 🫃 | 🫄 | 🫅 |  |  |  |  |  |  |  |  | 🫎 | 🫏
1FADx | U+1FADx | 🫐 | 🫑 | 🫒 | 🫓 | 🫔 | 🫕 | 🫖 | 🫗 | 🫘 | 🫙 | 🫚 | 🫛
1FAEx | U+1FAEx | 🫠 | 🫡 | 🫢 | 🫣 | 🫤 | 🫥 | 🫦 | 🫧 | 🫨
1FAFx | U+1FAFx | 🫰 | 🫱 | 🫲 | 🫳 | 🫴 | 🫵 | 🫶 | 🫷 | 🫸
1F68x | U+1F68x | 🚀 | 🚁 | 🚂 | 🚃 | 🚄 | 🚅 | 🚆 | 🚇 | 🚈 | 🚉 | 🚊 | 🚋 | 🚌 | 🚍 | 🚎 | 🚏 | Transport and Map Symbols | 118
1F69x | U+1F69x | 🚐 | 🚑 | 🚒 | 🚓 | 🚔 | 🚕 | 🚖 | 🚗 | 🚘 | 🚙 | 🚚 | 🚛 | 🚜 | 🚝 | 🚞 | 🚟 | U+1F680..U+1F6FF
1F6Ax | U+1F6Ax | 🚠 | 🚡 | 🚢 | 🚣 | 🚤 | 🚥 | 🚦 | 🚧 | 🚨 | 🚩 | 🚪 | 🚫 | 🚬 | 🚭 | 🚮 | 🚯
1F6Bx | U+1F6Bx | 🚰 | 🚱 | 🚲 | 🚳 | 🚴 | 🚵 | 🚶 | 🚷 | 🚸 | 🚹 | 🚺 | 🚻 | 🚼 | 🚽 | 🚾 | 🚿
1F6Cx | U+1F6Cx | 🛀 | 🛁 | 🛂 | 🛃 | 🛄 | 🛅 | 🛆 | 🛇 | 🛈 | 🛉 | 🛊 | 🛋 | 🛌 | 🛍 | 🛎 | 🛏
1F6Dx | U+1F6Dx | 🛐 | 🛑 | 🛒 | 🛓 | 🛔 | 🛕 | 🛖 | 🛗 |  |  |  |  | 🛜 | 🛝 | 🛞 | 🛟
1F6Ex | U+1F6Ex | 🛠 | 🛡 | 🛢 | 🛣 | 🛤 | 🛥 | 🛦 | 🛧 | 🛨 | 🛩 | 🛪 | 🛫 | 🛬
1F6Fx | U+1F6Fx | 🛰 | 🛱 | 🛲 | 🛳 | 🛴 | 🛵 | 🛶 | 🛷 | 🛸 | 🛹 | 🛺 | 🛻 | 🛼

Sheet: Logic
Symbol |  | Unicode | https://en.wikipedia.org/wiki/LaTeX | Logic Name | Read as | Category | Explanation | Examples
 |  | value
 |  | (hexadecimal)
⇒ | ⇒ | U+21D2 |  | material implication (https://en.wikipedia.org/wiki/Material_conditional) | implies; if ... then | propositional logic, Heyting algebra | �⇒� is false when A is true and B is false but true otherwise. | �=2⇒�2=4 is true, but �2=4⇒�=2 is in general false
→ | → |  |  |  |  |  |  | (since x could be −2).
⊃ | ⊃ | U+2192 |  |  |  |  | →
 |  |  |  |  |  |  | may mean the same as ⇒
 |  | U+2283
 |  |  |  |  |  |  | (the symbol may also indicate the domain and codomain of a function; see table of mathematical symbols).
 |  |  |  |  |  |  | ⊃
 |  |  |  |  |  |  | may mean the same as ⇒
 |  |  |  |  |  |  | (the symbol may also mean superset). (https://en.wikipedia.org/wiki/Superset)
⇔ | ⇔ | U+21D4 |  | material equivalence (https://en.wikipedia.org/wiki/Material_equivalence) | if and only if; iff; means the same as | propositional logic (https://en.wikipedia.org/wiki/Propositional_logic) | �⇔� is true only if both A and B are false, or both A and B are true. | �+5=�+2⇔�+3=�
≡ | ≡
↔ | ↔ | U+2261
 |  | U+2194
¬ | ¬ | U+00AC |  | negation (https://en.wikipedia.org/wiki/Negation) | not | propositional logic (https://en.wikipedia.org/wiki/Propositional_logic) | The statement ¬� is true if and only if A is false. | ¬(¬�)⇔�
˜ | ˜ |  |  |  |  |  |  | �≠�⇔¬(�=�)
! | ! | U+02DC |  |  |  |  | A slash placed through another operator is the same as ¬
 |  |  |  |  |  |  | placed in front.
 |  | U+0021
� | � | U+1D53B |  | Domain of discourse (https://en.wikipedia.org/wiki/Domain_of_discourse) | Domain of predicate | Predicate (mathematical logic) (https://en.wikipedia.org/wiki/Predicate_(mathematical_logic)) |  | �:�
∧ | ∧ | U+2227 |  | logical conjunction (https://en.wikipedia.org/wiki/Logical_conjunction) | and | propositional logic, Boolean algebra | The statement A ∧ B is true if A and B are both true; otherwise, it is false. | n < 4 ∧ n >2 ⇔ n = 3 when n is a natural number. (https://en.wikipedia.org/wiki/Natural_number)
· | ·
& | & | U+00B7
 |  | U+0026
∨ | ∨ | U+2228 |  | logical (inclusive) disjunction (https://en.wikipedia.org/wiki/Logical_disjunction) | or | propositional logic, Boolean algebra | The statement A ∨ B is true if A or B (or both) are true; if both are false, the statement is false. | n ≥ 4 ∨ n ≤ 2 ⇔ n ≠ 3 when n is a natural number. (https://en.wikipedia.org/wiki/Natural_number)
+ | +
∥ | ∥ | U+002B
 |  | U+2225
↮ | ↮ | U+21AE |  | exclusive disjunction (https://en.wikipedia.org/wiki/Exclusive_or) | xor; either ... or | propositional logic, Boolean algebra | The statement A ↮ B is true when either A or B, but not both, are true. | (¬A) ↮ A is always true, and A ↮ A always false, if vacuous truth is excluded. (https://en.wikipedia.org/wiki/Vacuous_truth)
⊕ | ⊕ |  |  |  |  |  | A ⊻ B means the same.
⊻ | ⊻ | U+2295
≢ | ≢
 |  | U+22BB
 |  | U+2262 (https://en.wikipedia.org/wiki/Mathematical_Operators)
⊤ | ⊤ | U+22A4 |  | Tautology (https://en.wikipedia.org/wiki/Tautology_(logic)) | top, truth, full clause | propositional logic, Boolean algebra, first-order logic | ⊤ is unconditionally true. | ⊤(A) ⇒ A is always true.
T | T
1 | 1 | U+25A0
■ | ■
⊥ | ⊥ | U+22A5 |  | Contradiction (https://en.wikipedia.org/wiki/Contradiction) | bottom, falsum, falsity, empty clause | propositional logic, Boolean algebra, first-order logic | ⊥ is unconditionally false. | ⊥(A) ⇒ A is always false.
F | F |  |  |  |  |  | (The symbol ⊥ may also refer to perpendicular lines.) (https://en.wikipedia.org/wiki/Perpendicular)
0 | 0 | U+25A1
□ | □
∀ | ∀ | U+2200 |  | universal quantification (https://en.wikipedia.org/wiki/Universal_quantification) | for all; for any; for each | first-order logic (https://en.wikipedia.org/wiki/First-order_logic) | ∀ x: P(x) or (x) P(x) means P(x) is true for all x. | ∀�∈�:�2≥�.
() | ()
∃ | ∃ | U+2203 |  | existential quantification (https://en.wikipedia.org/wiki/Existential_quantification) | there exists | first-order logic (https://en.wikipedia.org/wiki/First-order_logic) | ∃ x: P(x) means there exists at least one x such that P(x) is true. | ∃�∈�: n is even.
∃! | ∃! | U+2203 U+0021 |  | uniqueness quantification (https://en.wikipedia.org/wiki/Uniqueness_quantification) | there exists exactly one | first-order logic (https://en.wikipedia.org/wiki/First-order_logic) | ∃! x: P(x) means there exists exactly one x such that P(x) is true. | ∃!�∈�:�+5=2�.
≔ | ≔ | U+2254 (U+003A U+003D) |  | definition (https://en.wikipedia.org/wiki/Definition) | is defined as | everywhere | x ≔ y or x ≡ y means x is defined to be another name for y | cosh⁡�:=��+�−�2
≡ | ≡ |  |  |  |  |  | ( The symbol ≡ can also mean other things, such as congruence). (https://en.wikipedia.org/wiki/Congruence_relation)
:⇔ | :⇔ | U+2261 |  |  |  |  |  | A ⊕ B :⇔ (A ∨ B) ∧ ¬(A ∧ B)
 |  |  |  |  |  |  | P :⇔ Q means P is defined to be logically equivalent to Q. (https://en.wikipedia.org/wiki/Logical_equivalence)
 |  | U+003A U+21D4
( ) | ( ) | U+0028 U+0029 |  | precedence grouping (https://en.wikipedia.org/wiki/Precedence_grouping) | parentheses; brackets | everywhere | Perform the operations inside the parentheses first. | (8 ÷ 4) ÷ 2 = 2 ÷ 2 = 1, but 8 ÷ (4 ÷ 2) = 8 ÷ 2 = 4.
⊢ | ⊢ | U+22A2 |  | turnstile (https://en.wikipedia.org/wiki/Turnstile_(symbol)) | proves (https://en.wikipedia.org/wiki/Logical_consequence) | propositional logic, first-order logic | x ⊢ y means x proves (syntactically entails) y | (A → B) ⊢ (¬B → ¬A)
⊨ | ⊨ | U+22A8 |  | double turnstile (https://en.wikipedia.org/wiki/Double_turnstile) | models (https://en.wikipedia.org/wiki/Logical_consequence) | propositional logic, first-order logic | x ⊨ y means x models (semantically entails) y | (A → B) ⊨ (¬B → ¬A)
Symbol |  | Unicode | https://en.wikipedia.org/wiki/LaTeX | Logic Name | Read as | Category | Explanation | Examples
 |  | value
 |  | (hexadecimal)
̅ | ̅ | U+0305 |  | COMBINING OVERLINE (https://en.wikipedia.org/wiki/Overline) |  |  | used format for denoting Gödel numbers. (https://en.wikipedia.org/wiki/G%C3%B6del_numbering) | using HTML style "4̅" is a shorthand for the standard numeral "SSSS0".
 |  |  |  |  |  |  | denoting negation used primarily in electronics. | "A ∨ B" says the Gödel number of "(A ∨ B)". "A ∨ B" is the same as "¬(A ∨ B)".
↑ | ↑ | U+2191 |  | UPWARDS ARROW |  |  | Sheffer stroke, (https://en.wikipedia.org/wiki/Sheffer_stroke)
| | | | U+007C |  | VERTICAL LINE |  |  | the sign for the NAND operator (negation of conjunction).
↓ | ↓ | U+2193 |  | DOWNWARDS ARROW |  |  | Peirce Arrow, (https://en.wikipedia.org/wiki/Peirce_arrow)
 |  |  |  |  |  |  | the sign for the NOR operator (negation of disjunction).
⊙ | ⊙ | U+2299 |  | CIRCLED DOT OPERATOR |  |  | the sign for the XNOR operator (negation of exclusive disjunction).
∁ | ∁ | U+2201 |  | COMPLEMENT (https://en.wikipedia.org/wiki/Complement_(set_theory))
∄ | ∄ | U+2204 |  | THERE DOES NOT EXIST |  |  | strike out existential quantifier, same as "¬∃"
∴ | ∴ | U+2234 |  | THEREFORE (https://en.wikipedia.org/wiki/Therefore_sign) | Therefore (https://en.wikipedia.org/wiki/Therefore_sign)
∵ | ∵ | U+2235 |  | BECAUSE (https://en.wikipedia.org/wiki/Therefore_sign) | because
⊧ | ⊧ | U+22A7 |  | MODELS |  |  | is a model of (or "is a valuation satisfying")
⊨ | ⊨ | U+22A8 |  | TRUE | is true of
⊬ | ⊬ | U+22AC |  | DOES NOT PROVE |  |  | negated ⊢, the sign for "does not prove" | T ⊬ P says "P is not a theorem of T"
⊭ | ⊭ | U+22AD |  | NOT TRUE | is not true of
† | † | U+2020 |  | DAGGER | it is true that ... |  | Affirmation operator
⊼ | ⊼ | U+22BC |  | NAND |  |  | NAND operator
⊽ | ⊽ | U+22BD |  | NOR |  |  | NOR operator
◇ | ◇ | U+25C7 |  | WHITE DIAMOND |  |  | modal operator for "it is possible that", "it is not necessarily not" or rarely "it is not probably not" (in most modal logics it is defined as "¬◻¬")
⋆ | ⋆ | U+22C6 |  | STAR OPERATOR |  |  | usually used for ad-hoc operators
⊥ | ⊥ | U+22A5 |  | UP TACK (https://en.wikipedia.org/wiki/Up_tack) |  |  | Webb-operator or Peirce arrow, the sign for NOR.
↓ | ↓ | U+2193 |  | DOWNWARDS ARROW |  |  | Confusingly, "⊥" is also the sign for contradiction or absurdity.
⌐ | ⌐ | U+2310 |  | REVERSED NOT SIGN
⌜ | ⌜ | U+231C |  | TOP LEFT CORNER |  |  | corner quotes, also called "Quine quotes"; for quasi-quotation, i.e. quoting specific context of unspecified ("variable") expressions;[3] also used for denoting Gödel number;[4] for example "⌜G⌝" denotes the Gödel number of G. (Typographical note: although the quotes appears as a "pair" in unicode (231C and 231D), they are not symmetrical in some fonts. In some fonts (for example Arial) they are only symmetrical in certain sizes. Alternatively the quotes can be rendered as ⌈ and ⌉ (U+2308 and U+2309) or by using a negation symbol and a reversed negation symbol ⌐ ¬ in superscript mode. )
⌝ | ⌝ | U+231D |  | TOP RIGHT CORNER
◻ | ◻ | U+25FB |  | WHITE MEDIUM SQUARE |  |  | modal operator for "it is necessary that"
□ | □ | U+25A1 |  | WHITE SQUARE |  |  | (in modal logic), or "it is provable that" (https://en.wikipedia.org/wiki/Modal_logic)
 |  |  |  |  |  |  | (in provability logic), or "it is obligatory that" (https://en.wikipedia.org/wiki/Provability_logic)
 |  |  |  |  |  |  | (in deontic logic), or "it is believed that" (https://en.wikipedia.org/wiki/Deontic_logic)
 |  |  |  |  |  |  | (in doxastic logic); also as empty clause (alternatives: ∅
 |  |  |  |  |  |  | and ⊥)
⟛ | ⟛ | U+27DB |  | LEFT AND RIGHT TACK |  | semantic equivalent
⟡ | ⟡ | U+27E1 |  | WHITE CONCAVE-SIDED DIAMOND | never | modal operator
⟢ | ⟢ | U+27E2 |  | WHITE CONCAVE-SIDED DIAMOND WITH LEFTWARDS TICK | was never | modal operator
⟣ | ⟣ | U+27E3 |  | WHITE CONCAVE-SIDED DIAMOND WITH RIGHTWARDS TICK | will never be | modal operator
□ | □ | U+25A1 |  | WHITE SQUARE | always | modal operator
⟤ | ⟤ | U+25A4 |  | WHITE SQUARE WITH LEFTWARDS TICK | was always | modal operator
⟥ | ⟥ | U+25A5 |  | WHITE SQUARE WITH RIGHTWARDS TICK | will always be | modal operator
⥽ | ⥽ | U+297D |  | RIGHT FISH TAIL |  |  | sometimes used for "relation", also used for denoting various ad hoc relations (for example, for denoting "witnessing" in the context of Rosser's trick) The fish hook is also used as strict implication by C.I.Lewis � ⥽ �≡◻(�→�). See here for an image of glyph. Added to Unicode 3.2.0.
⨇ | ⨇ | U+2A07 |  | TWO LOGICAL AND OPERATOR
