Julesc013/abacus-2/hardware/video/video_adapter/CDA Technical.xlsx

Sheet: Modes
CVGA Modes
ID | Mode | Resolution | Colors | Chars | Kbytes | Circuitry | Notes
0 | Text 40×24 | 640×480 | 2 | – | – | Yamaha V9938 | Insert padding scan lines.
1 | Text 80×24 | 640×480 | 2 | – | – | Yamaha V9938 | Insert padding scan lines.
2 | Pattern MC | 640×480 | 16 | – | – | Yamaha V9938 | Insert padding scan lines.
3 | Pattern G1 | 640×480 | 16 | – | – | Yamaha V9938 | Insert padding scan lines.
4 | Pattern G2 | 640×480 | 16 | – | – | Yamaha V9938 | Insert padding scan lines.
5 | Pattern G3 | 640×480 | 16 | – | – | Yamaha V9938 | Insert padding scan lines.
6 | – | – | – | – | – | – | –
7 | – | – | – | – | – | – | –
8 | Text 40×24 | 1920×1080 | 2 | – | – | Yamaha V9938 | Upscale to 1080p.
9 | Text 80×24 | 1920×1080 | 2 | – | – | Yamaha V9938 | Upscale to 1080p.
A | Pattern MC | 1920×1080 | 16 | – | – | Yamaha V9938 | Upscale to 1080p.
B | Pattern G1 | 1920×1080 | 16 | – | – | Yamaha V9938 | Upscale to 1080p.
C | Pattern G2 | 1920×1080 | 16 | – | – | Yamaha V9938 | Upscale to 1080p.
D | Pattern G3 | 1920×1080 | 16 | – | – | Yamaha V9938 | Upscale to 1080p.
E | – | – | – | – | – | – | –
F | Text 160×45 | 1920×1080 | 4 | – | – | CVGA 1000 | Native 1080p resolution.
CDA Text Modes
ID | Mode | Resolution | Colors | Chars | Kbytes | Circuitry | Notes
0 | VGA 80×30 | 640×480 | 8 / 8 | 8×16 | – | CDA 1000 | –
1 | VGA 80×60 | 640×480 | 8 / 8 | 8×8 | – | – | –
2 | – | – | – | – | – | – | –
3 | – | – | – | – | – | – | –
4 | – | – | – | – | – | – | –
5 | – | – | – | – | – | – | –
6 | – | – | – | – | – | – | –
7 | – | – | – | – | – | – | –
8 | FHD 80×30 | 1920×1080 | 8 / 8 | 24×36 | – | CDA 1000 | –
9 | FHD 80×60 | 1920×1080 | 8 / 8 | 24×18 | – | – | –
A | FHD 120×30 | 1920×1080 | 8 / 8 | 16×36 | – | – | –
B | FHD 120×60 | 1920×1080 | 8 / 8 | 16×18 | – | – | –
C | FHD 160×45 | 1920×1080 | 8 / 8 | 12×24 | – | CDA 1000 | –
D | FHD 160×90 | 1920×1080 | 8 / 8 | 12×12 | – | – | –
E | FHD 240×60 | 1920×1080 | 8 / 8 | 8×18 | – | – | –
F | FHD 240×120 | 1920×1080 | 8 / 8 | 8×9 | – | – | –
CDA Text Modes
ID | Mode | Resolution | Colors | Chars | Kbytes | Circuitry | Notes
0 | VGA 40×20 | 640×480 | 8 / 4 | 16×24 | – | CDA 1000 | –
1 | – | – | – | – | – | – | –
2 | VGA 80×40 | 640×480 | 8 / 4 | 8×12 | – | CDA 1000 | –
3 | – | – | – | – | – | – | –
4 | – | – | – | – | – | – | –
5 | – | – | – | – | – | – | –
6 | – | – | – | – | – | – | –
7 | – | – | – | – | – | – | –
8 | FHD 40×20 | 1920×1080 | 8 / 4 | 48×54 | – | CDA 1000 | –
9 | – | – | – | – | – | – | –
A | FHD 80×40 | 1920×1080 | 8 / 4 | 24×27 | – | CDA 1000 | –
B | – | – | – | – | – | – | –
C | FHD 120×45 | 1920×1080 | 8 / 4 | 16×24 | – | CDA 1000 | –
D | – | – | – | – | – | – | –
E | FHD 240×90 | 1920×1080 | 8 / 4 | 8×12 | – | CDA 1000 | –
F | – | – | – | – | – | – | –
CDA Text Modes
ID | Mode | Resolution | Colors | Chars | Kbytes | Circuitry | Notes
0 | VGA 40×20 | 640×480 | 8 / 4 | 16×24 | 10 | CDA I | –
1 | – | – | – | – | – | – | –
2 | SVGA 50×25 | 800×600 | 8 / 4 | 16×24 | 12.5 | CDA I | –
3 | – | – | – | – | – | – | –
4 | XGA 64×32 | 1024×768 | 8 / 4 | 16×24 | 16 | CDA I | –
5 | – | – | – | – | – | – | –
6 | WXGA 80×30 | 1280×720* | 8 / 4 | 16×24 | 15 | CDA I | –
7 | QVGA 40×15 | 1280×720* | 8 / 4 | 32×48 | 7.5 | CDA I | –
8 | SHD 96×36 | 1536×864 | 8 / 4 | 16×24 | 18 | CDA I | –
9 | QSHD 48×18 | 1536×864 | 8 / 4 | 32×48 | 9 | CDA I | –
A | FHD 120×45 | 1920×1080 | 8 / 4 | 16×24 | 22.5 | CDA I | –
B | NVGA 40×15 | 1920×1080 | 8 / 4 | 48×72 | 7.5 | CDA I | –
C | WQHD 160×60 | 2560×1440 | 8 / 4 | 16×24 | 30 | CDA II | –
D | QWXGA 80×30 | 2560×1440 | 8 / 4 | 32×48 | 15 | CDA II | –
E | UHD 240×90 | 3840×2160 | 8 / 4 | 16×24 | 45 | CDA III | –
F | QFHD 120×45 | 3840×2160 | 8 / 4 | 32×48 | 22.5 | CDA III | –
 |  | * Will need to overscan to 1280×800
6 | WQHD 80×30 | 2560×1440 | 8 / 4 | 32×48 | 15 | CDA I | –
7 | QWXGA 40×15 | 2560×1440 | 8 / 4 | 64×96 | 7.5 | CDA I | –

Sheet: Color Palettes
CDA Color Palettes |  |  |  |  |  |  |  |  |  | CVGA Color Palettes
Text Mode (4 Byte) |  |  | Text Mode (2 Byte) |  |  |  |  |  |  | Text Mode (4 Byte) |  |  | Bitmap Mode (4 Bit)
Color | Lum = 0 | Lum = 1 | R | G | B | 00 | 01 | 10 | 11 | Color | Lum = 0 | Lum = 1 | Color | Default | Alternate | Grey | Custom
0000 | 000000 | 555555 | 00 | 00 | 00 | 000000 | 404040 | 808080 | C0C0C0 | 0000 | 000000 | 555555 | 0000 | 000000 | 000000 | 000000 | 000000
0001 | 000080 | 0000FF | 00 | 00 | 01 | 000055 | 404080 | 8080D5 | C0C0D5 | 0001 | 000080 | 0000FF | 0001 | 0080FF | 000080 | 111111 | 9DAFFF
0010 | 008000 | 00FF00 | 00 | 00 | 10 | 0000AA | 4040C0 | 8080D5 | C0C0EA | 0010 | 008000 | 00FF00 | 0010 | 80FF00 | 008000 | 222222 | 81C57A
0011 | 008080 | 00FFFF | 00 | 00 | 11 | 0000FF | 4040FF | 8080FF | C0C0FF | 0011 | 008080 | 00FFFF | 0011 | 00FF80 | 008080 | 333333 | E9DEBB
0100 | 800000 | FF0000 | 00 | 01 | 00 | 005500 | 408040 | 80D580 | C0D5C0 | 0100 | 800000 | FF0000 | 0100 | FF0080 | 800000 | 444444 | FF9233
0101 | 800080 | FF00FF | 00 | 01 | 01 | 005555 | 408080 | 80D5D5 | C0D5D5 | 0101 | 800080 | FF00FF | 0101 | 8000FF | 800080 | 555555 | 8126C0
0110 | 808000 | FFFF00 | 00 | 01 | 10 | 0055AA | 4080C0 | 80D5D5 | C0D5EA | 0110 | 808000 | FFFF00 | 0110 | FF8000 | 808000 | 666666 | 814A19
0111 | AAAAAA | FFFFFF | 00 | 01 | 11 | 0055FF | 4080FF | 80D5FF | C0D5FF | 0111 | AAAAAA | FFFFFF | 0111 | AAAAAA | AAAAAA | 777777 | A0A0A0
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
 |  |  | 11 | 10 | 00 | FFAA00 | FFC040 | FFD580 | FFEAC0
 |  |  | 11 | 10 | 01 | FFAA55 | FFC080 | FFD5D5 | FFEAD5
 |  |  | 11 | 10 | 10 | FFAAAA | FFC0C0 | FFD5D5 | FFEAEA
 |  |  | 11 | 10 | 11 | FFAAFF | FFC0FF | FFD5FF | FFEAFF
 |  |  | 11 | 11 | 00 | FFFF00 | FFFF40 | FFFF80 | FFFFC0
 |  |  | 11 | 11 | 01 | FFFF55 | FFFF80 | FFFFD5 | FFFFD5
 |  |  | 11 | 11 | 10 | FFFFAA | FFFFC0 | FFFFD5 | FFFFEA
 |  |  | 11 | 11 | 11 | FFFFFF | FFFFFF | FFFFFF | FFFFFF

Sheet: Code Pages (CVGA-2)
Page |  | 0 | 1 | 2 | 3 | 4 | 5 | 6 | 7 | 8 | 9 | A | B | C | D | E | F | Block | Page | Block | Points | Notes
0 | 0x |  | Α | Β | Γ | Δ | Ε | Ζ | Η | Θ | Ι | Κ | Λ | Μ | Ν | Ξ | Ο | Greek Alphabet (Uppercase) | 0 | 0x – 1x | Miscellaneous Symbols A
 | 1x | Π | Ρ | ⁊ | Σ | Τ | Υ | Φ | Χ | Ψ | Ω | ℥ | ⟨ | ‹ | ⟩ | › | ₧ |  |  | 2x – 7x | Latin Alphabet (ASCII)
 | 2x |  | ! | " | # | $ | % | & | ' | ( | ) | * | + | , | - | . | / | Latin Alphabet (ASCII) |  | 8x – 9x | Miscellaneous Symbols B
 | 3x | 0 | 1 | 2 | 3 | 4 | 5 | 6 | 7 | 8 | 9 | : | ; | < | = | > | ? |  |  | Ax – Fx | Latin Supplement
 | 4x | @ | A | B | C | D | E | F | G | H | I | J | K | L | M | N | O |  | 1 | 0x – 3x | Greek Alphabet
 | 5x | P | Q | R | S | T | U | V | W | X | Y | Z | [ | \ | ] | ^ | _ |  |  | 4x – 7x | Cyrillic Alphabet
 | 6x | ` | a | b | c | d | e | f | g | h | i | j | k | l | m | n | o |  |  | 8x – Cx | General Punctuation
 | 7x | p | q | r | s | t | u | v | w | x | y | z | { | | | } | ~ | ⌂ |  |  | Dx – Fx | Supplementary Symbols | Arrows, Fractions, Currency, Roman Numerals
 | 8x | € | α | β | γ | δ | ε | ζ | η | θ | ι | κ | λ | μ | ν | ξ | ο | Greek Alphabet (Lowercase) | 2 | 0x – 7x | Mathematical Operators
 | 9x | π | ρ | ς | σ | τ | υ | φ | χ | ψ | ω | – | — | … | ℠ | ℗ | № |  |  | 8x – Fx | Box Drawing
 | Ax |  | ¡ | ¢ | £ | ¤ | ¥ | ¦ | § | ¨ | © | ª | « | ¬ | ™ | ® | ¯ | Latin Supplement | 3 | 0x – Bx | Legacy Elements | Symbols for Legacy Computing
 | Bx | ° | ± | ² | ³ | ´ | µ | ¶ | · | ¸ | ¹ | º | » | ¼ | ½ | ¾ | ¿ |  |  | Cx – Dx | Block Elements
 | Cx | À | Á | Â | Ã | Ä | Å | Æ | Ç | È | É | Ê | Ë | Ì | Í | Î | Ï |  |  | Ex – Fx | Letterlike Symbols
 | Dx | Ð | Ñ | Ò | Ó | Ô | Õ | Ö | × | Ø | Ù | Ú | Û | Ü | Ý | Þ | ß
 | Ex | à | á | â | ã | ä | å | æ | ç | è | é | ê | ë | ì | í | î | ï
 | Fx | ð | ñ | ò | ó | ô | õ | ö | ÷ | ø | ù | ú | û | ü | ý | þ | ÿ
1 | 0x | † | ‡ | ℹ | ⁎ | ⁑ | ⁂ | ※ | ∓ | ‸ | ⁿ | ƒ | ⁋ | ⁌ | ⁍ | ‽ | ‼ | General Punctuation & Mathematical Operators
 | 1x | ‰ | ‱ | ′ | ″ | ‴ | ⁗ | ∂ | ∧ | ∨ | ∩ | ∪ | ∫ | ∬ | ∭ | ℇ | ℯ
 | 2x | ∠ | ∡ | ∢ | ∟ | ⊾ | ⅈ | ⅉ | ∈ | ∉ | ∥ | ∦ | ∝ | ⌐ | √ | ∛ | ∜
 | 3x | ≠ | ≡ | ≢ | ≣ | ≔ | ∴ | ∵ | ∷ | ⋰ | ⋱ | ⋮ | ⋯ | ≤ | ≈ | ≥ | ≉
 | 4x | ℕ | ℤ | ℚ | 𝔸 | ℝ | 𝕀 | ℂ | ∞ | ⌀ | ∗ | ∘ | ∙ | ⊕ | ⊖ | ⊗ | ⊘
 | 5x | ⅐ | ⅑ | ⅒ | ⅓ | ⅔ | ⅕ | ⅖ | ⅗ | ⅘ | ⅙ | ⅚ | ⅛ | ⅜ | ⅝ | ⅞ | ⅟ | Supplementary Symbols
 | 6x | ← | ↑ | → | ↓ | ↔ | ↕ | ↖ | ↗ | ↘ | ↙ | ⇐ | ⇋ | ⇒ | ⇌ | ⇔ | ⇕
 | 7x | ◄ | ▲ | ► | ▼ | ☺ | ☻ | ♥ | ♦ | ♣ | ♠ | ♂ | ♀ | ♪ | ♫ | ☼ | ↨ | Code Page 437 (Leftovers)
 | 8x | 🮀 | 🮁 | 🮂 | 🮃 | 🮄 | 🮅 | 🮆 | 🮇 | 🮈 | 🮉 | 🮊 | 🮋 | 🮌 | 🮍 | 🮎 | 🮏 | Legacy Elements
 | 9x | 🮐 | 🮑 | 🮒 | ■ | 🮔 | 🮕 | 🮖 | 🮗 | 🮘 | 🮙 | 🮚 | 🮛 | 🮜 | 🮝 | 🮞 | 🮟
 | Ax | ▀ | ▁ | ▂ | ▃ | ▄ | ▅ | ▆ | ▇ | █ | ▉ | ▊ | ▋ | ▌ | ▍ | ▎ | ▏ | Block Elements
 | Bx | ▐ | ░ | ▒ | ▓ | ▔ | ▕ | ▖ | ▗ | ▘ | ▙ | ▚ | ▛ | ▜ | ▝ | ▞ | ▟
 | Cx | ─ | │ | ┌ | ┐ | └ | ┘ | ├ | ┤ | ┬ | ┴ | ┼ | ‣ | • | ◘ | ○ | ◙ | Box Drawing
 | Dx | ═ | ║ | ╒ | ╓ | ╔ | ╕ | ╖ | ╗ | ╘ | ╙ | ╚ | ╛ | ╜ | ╝ | ╞ | ╟
 | Ex | ╠ | ╡ | ╢ | ╣ | ╤ | ╥ | ╦ | ╧ | ╨ | ╩ | ╪ | ╫ | ╬ | ╭ | ╮ | ╯
 | Fx | ╰ | ╱ | ╲ | ╳ | ⌠ | ⌡ | ∎ | ▬ | ╸ | ╹ | ╺ | ╻ | ☑ | ☐ | 🮰

Sheet: Code Pages (CVGA-4)
Page |  | 0 | 1 | 2 | 3 | 4 | 5 | 6 | 7 | 8 | 9 | A | B | C | D | E | F | U+ | Block | Page | Block | Points | Notes
0 | 0x |  |  |  |  |  |  |  |  |  |  |  |  |  |  |  |  |  | Miscellaneous Symbols A | 0 | 0x – 1x | Miscellaneous Symbols A
 | 1x |  |  |  |  |  |  |  |  |  |  |  |  |  |  |  |  |  |  |  | 2x – 7x | Latin Alphabet (ASCII)
 | 2x |  | ! | " | # | $ | % | & | ' | ( | ) | * | + | , | - | . | / | 002x | Latin Alphabet (ASCII) |  | 8x – 9x | Miscellaneous Symbols B
 | 3x | 0 | 1 | 2 | 3 | 4 | 5 | 6 | 7 | 8 | 9 | : | ; | < | = | > | ? | 003x |  |  | Ax – Fx | Latin Supplement
 | 4x | @ | A | B | C | D | E | F | G | H | I | J | K | L | M | N | O | 004x |  | 1 | 0x – 3x | Greek Alphabet
 | 5x | P | Q | R | S | T | U | V | W | X | Y | Z | [ | \ | ] | ^ | _ | 005x |  |  | 4x – 7x | Cyrillic Alphabet
 | 6x | ` | a | b | c | d | e | f | g | h | i | j | k | l | m | n | o | 006x |  |  | 8x – Cx | General Punctuation
 | 7x | p | q | r | s | t | u | v | w | x | y | z | { | | | } | ~ | DEL | 007x |  |  | Dx – Fx | Supplementary Symbols | Arrows, Fractions, Currency, Roman Numerals
 | 8x |  |  |  |  |  |  |  |  |  |  |  |  |  |  |  |  |  | Miscellaneous Symbols B | 2 | 0x – 7x | Mathematical Operators
 | 9x |  |  |  |  |  |  |  |  |  |  |  |  |  |  |  |  |  |  |  | 8x – Fx | Box Drawing
 | Ax |  | ¡ | ¢ | £ | ¤ | ¥ | ¦ | § | ¨ | © | ª | « | ¬ | SHY | ® | ¯ | 00Ax | Latin Supplement | 3 | 0x – Bx | Legacy Elements | Symbols for Legacy Computing
 | Bx | ° | ± | ² | ³ | ´ | µ | ¶ | · | ¸ | ¹ | º | » | ¼ | ½ | ¾ | ¿ | 00Bx |  |  | Cx – Dx | Block Elements
 | Cx | À | Á | Â | Ã | Ä | Å | Æ | Ç | È | É | Ê | Ë | Ì | Í | Î | Ï | 00Cx |  |  | Ex – Fx | Letterlike Symbols
 | Dx | Ð | Ñ | Ò | Ó | Ô | Õ | Ö | × | Ø | Ù | Ú | Û | Ü | Ý | Þ | ß | 00Dx
 | Ex | à | á | â | ã | ä | å | æ | ç | è | é | ê | ë | ì | í | î | ï | 00Ex
 | Fx | ð | ñ | ò | ó | ô | õ | ö | ÷ | ø | ù | ú | û | ü | ý | þ | ÿ | 00Fx
1 | 0x | ΐ | Α | Β | Γ | Δ | Ε | Ζ | Η | Θ | Ι | Κ | Λ | Μ | Ν | Ξ | Ο | 039x | Greek Alphabet
 | 1x | Π | Ρ |  | Σ | Τ | Υ | Φ | Χ | Ψ | Ω | Ϊ | Ϋ | ά | έ | ή | ί | 03Ax
 | 2x | ΰ | α | β | γ | δ | ε | ζ | η | θ | ι | κ | λ | μ | ν | ξ | ο | 03Bx
 | 3x | π | ρ | ς | σ | τ | υ | φ | χ | ψ | ω | ϊ | ϋ | ό | ύ | ώ | Ϗ | 03Cx
 | 4x | А | Б | В | Г | Д | Е | Ж | З | И | Й | К | Л | М | Н | О | П | 041x | Cyrillic Alphabet
 | 5x | Р | С | Т | У | Ф | Х | Ц | Ч | Ш | Щ | Ъ | Ы | Ь | Э | Ю | Я | 042x
 | 6x | а | б | в | г | д | е | ж | з | и | й | к | л | м | н | о | п | 043x
 | 7x | р | с | т | у | ф | х | ц | ч | ш | щ | ъ | ы | ь | э | ю | я | 044x
 | 8x | ‐ | NB | ‒ | – | — | ― | ‖ | ‗ | ‘ | ’ | ‚ | ‛ | “ | ” | „ | ‟ | 201x | General Punctuation
 | 9x | † | ‡ | • | ‣ | ․ | ‥ | … | ‧ | LSEP | PSEP | LRE | RLE | PDF | LRO | RLO | NNBSP | 202x
 | Ax | ‰ | ‱ | ′ | ″ | ‴ | ‵ | ‶ | ‷ | ‸ | ‹ | › | ※ | ‼ | ‽ | ‾ | ‿ | 203x
 | Bx | ⁀ | ⁁ | ⁂ | ⁃ | ⁄ | ⁅ | ⁆ | ⁇ | ⁈ | ⁉ | ⁊ | ⁋ | ⁌ | ⁍ | ⁎ | ⁏ | 204x
 | Cx | ⁐ | ⁑ | ⁒ | ⁓ | ⁔ | ⁕ | ⁖ | ⁗ | ⁘ | ⁙ | ⁚ | ⁛ | ⁜ | ⁝ | ⁞ | MMSP | 205x
 | Dx | ← | ↑ | → | ↓ | ↔ | ↕ | ↖ | ↗ | ↘ | ↙ | ⇐ | ⇋ | ⇒ | ⇌ | ⇔ | ⇕ | 219x | Supplementary Symbols
 | Ex | ⅐ | ⅑ | ⅒ | ⅓ | ⅔ | ⅕ | ⅖ | ⅗ | ⅘ | ⅙ | ⅚ | ⅛ | ⅜ | ⅝ | ⅞ | ⅟ | 215x
 | Fx | Ⅰ | Ⅱ | Ⅲ | Ⅳ | Ⅴ | Ⅵ | Ⅶ | Ⅷ | Ⅸ | Ⅹ | Ⅺ | Ⅻ | ₵ | ₤ | € | ¥ | 216x
2 | 0x | ∀ | ∁ | ∂ | ∃ | ∄ | ∅ | ∆ | ∇ | ∈ | ∉ | ∊ | ∋ | ∌ | ∍ | ∎ | ∏ | 220x | Mathematical Operators
 | 1x | ∐ | ∑ | − | ∓ | ∔ | ∕ | ∖ | ∗ | ∘ | ∙ | √ | ∛ | ∜ | ∝ | ∞ | ∟ | 221x
 | 2x | ∠ | ∡ | ∢ | ∣ | ∤ | ∥ | ∦ | ∧ | ∨ | ∩ | ∪ | ∫ | ∬ | ∭ | ∮ | ∯ | 222x
 | 3x | ∰ | ∱ | ∲ | ∳ | ∴ | ∵ | ∶ | ∷ | ∸ | ∹ | ∺ | ∻ | ∼ | ∽ | ∾ | ∿ | 223x
 | 4x | ≀ | ≁ | ≂ | ≃ | ≄ | ≅ | ≆ | ≇ | ≈ | ≉ | ≊ | ≋ | ≌ | ≍ | ≎ | ≏ | 224x
 | 5x | ≐ | ≑ | ≒ | ≓ | ≔ | ≕ | ⋍ | ⊾ | ⋰ | ⋱ | ⋮ | ⋯ | ⊕ | ⊖ | ⊗ | ⊘ | 225x
 | 6x | ≠ | ≡ | ≢ | ≣ | ≤ | ≥ | ≦ | ≧ | ≨ | ≩ | ≪ | ≫ | ≬ | ≭ | ≮ | ≯ | 226x
 | 7x | ⊂ | ⊃ | ⊄ | ⊅ | ⊆ | ⊇ | ⊈ | ⋀ | ⋁ | ⋂ | ⋃ | ⊉ | ⋖ | ⋗ | ⋘ | ⋙ | 227x
 | 8x | ─ | ━ | │ | ┃ | ┄ | ┅ | ┆ | ┇ | ┈ | ┉ | ┊ | ┋ | ┌ | ┍ | ┎ | ┏ | 250x | Box Drawing
 | 9x | ┐ | ┑ | ┒ | ┓ | └ | ┕ | ┖ | ┗ | ┘ | ┙ | ┚ | ┛ | ├ | ┝ | ┞ | ┟ | 251x
 | Ax | ┠ | ┡ | ┢ | ┣ | ┤ | ┥ | ┦ | ┧ | ┨ | ┩ | ┪ | ┫ | ┬ | ┭ | ┮ | ┯ | 252x
 | Bx | ┰ | ┱ | ┲ | ┳ | ┴ | ┵ | ┶ | ┷ | ┸ | ┹ | ┺ | ┻ | ┼ | ┽ | ┾ | ┿ | 253x
 | Cx | ╀ | ╁ | ╂ | ╃ | ╄ | ╅ | ╆ | ╇ | ╈ | ╉ | ╊ | ╋ | ╌ | ╍ | ╎ | ╏ | 254x
 | Dx | ═ | ║ | ╒ | ╓ | ╔ | ╕ | ╖ | ╗ | ╘ | ╙ | ╚ | ╛ | ╜ | ╝ | ╞ | ╟ | 255x
 | Ex | ╠ | ╡ | ╢ | ╣ | ╤ | ╥ | ╦ | ╧ | ╨ | ╩ | ╪ | ╫ | ╬ | ╭ | ╮ | ╯ | 256x
 | Fx | ╰ | ╱ | ╲ | ╳ | ╴ | ╵ | ╶ | ╷ | ╸ | ╹ | ╺ | ╻ | ╼ | ╽ | ╾ | ╿ | 257x
3 | 0x | 🬀 | 🬁 | 🬂 | 🬃 | 🬄 | 🬅 | 🬆 | 🬇 | 🬈 | 🬉 | 🬊 | 🬋 | 🬌 | 🬍 | 🬎 | 🬏 | 1FB0x | Legacy Elements
 | 1x | 🬐 | 🬑 | 🬒 | 🬓 | 🬔 | 🬕 | 🬖 | 🬗 | 🬘 | 🬙 | 🬚 | 🬛 | 🬜 | 🬝 | 🬞 | 🬟 | 1FB1x
 | 2x | 🬠 | 🬡 | 🬢 | 🬣 | 🬤 | 🬥 | 🬦 | 🬧 | 🬨 | 🬩 | 🬪 | 🬫 | 🬬 | 🬭 | 🬮 | 🬯 | 1FB2x
 | 3x | 🬰 | 🬱 | 🬲 | 🬳 | 🬴 | 🬵 | 🬶 | 🬷 | 🬸 | 🬹 | 🬺 | 🬻 | 🬼 | 🬽 | 🬾 | 🬿 | 1FB3x
 | 4x | 🭀 | 🭁 | 🭂 | 🭃 | 🭄 | 🭅 | 🭆 | 🭇 | 🭈 | 🭉 | 🭊 | 🭋 | 🭌 | 🭍 | 🭎 | 🭏 | 1FB4x
 | 5x | 🭐 | 🭑 | 🭒 | 🭓 | 🭔 | 🭕 | 🭖 | 🭗 | 🭘 | 🭙 | 🭚 | 🭛 | 🭜 | 🭝 | 🭞 | 🭟 | 1FB5x
 | 6x | 🭠 | 🭡 | 🭢 | 🭣 | 🭤 | 🭥 | 🭦 | 🭧 | 🭨 | 🭩 | 🭪 | 🭫 | 🭬 | 🭭 | 🭮 | 🭯 | 1FB6x
 | 7x | 🭰 | 🭱 | 🭲 | 🭳 | 🭴 | 🭵 | 🭶 | 🭷 | 🭸 | 🭹 | 🭺 | 🭻 | 🭼 | 🭽 | 🭾 | 🭿 | 1FB7x
 | 8x | 🮀 | 🮁 | 🮂 | 🮃 | 🮄 | 🮅 | 🮆 | 🮇 | 🮈 | 🮉 | 🮊 | 🮋 | 🮌 | 🮍 | 🮎 | 🮏 | 1FB8x
 | 9x | 🮐 | 🮑 | 🮒 |  | 🮔 | 🮕 | 🮖 | 🮗 | 🮘 | 🮙 | 🮚 | 🮛 | 🮜 | 🮝 | 🮞 | 🮟 | 1FB9x
 | Ax | 🮠 | 🮡 | 🮢 | 🮣 | 🮤 | 🮥 | 🮦 | 🮧 | 🮨 | 🮩 | 🮪 | 🮫 | 🮬 | 🮭 | 🮮 | 🮯 | 1FBAx
 | Bx | 🮰 | 🮱 | 🮲 | 🮳 | 🮴 | 🮵 | 🮶 | 🮷 | 🮸 | 🮹 | 🮺 | 🮻 | 🮼 | 🮽 | 🮾 | 🮿 | 1FBBx
 | Cx | ▀ | ▁ | ▂ | ▃ | ▄ | ▅ | ▆ | ▇ | █ | ▉ | ▊ | ▋ | ▌ | ▍ | ▎ | ▏ | 258x | Block Elements
 | Dx | ▐ | ░ | ▒ | ▓ | ▔ | ▕ | ▖ | ▗ | ▘ | ▙ | ▚ | ▛ | ▜ | ▝ | ▞ | ▟ | 259x
 | Ex | ℀ | ℁ | ℂ | ℃ | ℄ | ℅ | ℆ | ℇ | ℈ | ℉ | ℚ | ℻ | ℥ | ℝ | ℮ | ℯ | 210x | Letterlike Symbols
 | Fx | ℠ | ℡ | ™ | ℣ | ℤ | ℕ | № | ℗ | ⅈ | ⅉ | ⅀ | ℹ | ℼ | ℽ | ℾ | ℿ | 211x

Sheet: Code Pages (CVGA-12)
Page |  | 0 | 1 | 2 | 3 | 4 | 5 | 6 | 7 | 8 | 9 | A | B | C | D | E | F | U+ | Block
0 | 0x | NUL | SOH | STX | ETX | EOT | ENQ | ACK | BEL | BS | HT | LF | VT | FF | CR | SO | SI | 000x | C0 Controls
 | 1x | DLE | DC1 | DC2 | DC3 | DC4 | NAK | SYN | ETB | CAN | EM | SUB | ESC | FS | GS | RS | US | 001x
 | 2x | SP | ! | " | # | $ | % | & | ' | ( | ) | * | + | , | - | . | / | 002x | Basic Latin
 | 3x | 0 | 1 | 2 | 3 | 4 | 5 | 6 | 7 | 8 | 9 | : | ; | < | = | > | ? | 003x
 | 4x | @ | A | B | C | D | E | F | G | H | I | J | K | L | M | N | O | 004x
 | 5x | P | Q | R | S | T | U | V | W | X | Y | Z | [ | \ | ] | ^ | _ | 005x
 | 6x | ` | a | b | c | d | e | f | g | h | i | j | k | l | m | n | o | 006x
 | 7x | p | q | r | s | t | u | v | w | x | y | z | { | | | } | ~ | DEL | 007x
 | 8x | XXX | XXX | BPH | NBH | IND | NEL | SSA | ESA | HTS | HTJ | VTS | PLD | PLU | RI | SS2 | SS3 | 008x | C1 Controls
 | 9x | DCS | PU1 | PU2 | STS | CCH | MW | SPA | EPA | SOS | XXX | SCI | CSI | ST | OSC | PM | APC | 009x
 | Ax | NBSP | ¡ | ¢ | £ | ¤ | ¥ | ¦ | § | ¨ | © | ª | « | ¬ | SHY | ® | ¯ | 00Ax | Latin-1 Supplement
 | Bx | ° | ± | ² | ³ | ´ | µ | ¶ | · | ¸ | ¹ | º | » | ¼ | ½ | ¾ | ¿ | 00Bx
 | Cx | À | Á | Â | Ã | Ä | Å | Æ | Ç | È | É | Ê | Ë | Ì | Í | Î | Ï | 00Cx
 | Dx | Ð | Ñ | Ò | Ó | Ô | Õ | Ö | × | Ø | Ù | Ú | Û | Ü | Ý | Þ | ß | 00Dx
 | Ex | à | á | â | ã | ä | å | æ | ç | è | é | ê | ë | ì | í | î | ï | 00Ex
 | Fx | ð | ñ | ò | ó | ô | õ | ö | ÷ | ø | ù | ú | û | ü | ý | þ | ÿ | 00Fx
1 | 0x | Ѐ | Ё | Ђ | Ѓ | Є | Ѕ | І | Ї | Ј | Љ | Њ | Ћ | Ќ | Ѝ | Ў | Џ | 040x | Cyrillic
 | 1x | А | Б | В | Г | Д | Е | Ж | З | И | Й | К | Л | М | Н | О | П | 041x
 | 2x | Р | С | Т | У | Ф | Х | Ц | Ч | Ш | Щ | Ъ | Ы | Ь | Э | Ю | Я | 042x
 | 3x | а | б | в | г | д | е | ж | з | и | й | к | л | м | н | о | п | 043x
 | 4x | р | с | т | у | ф | х | ц | ч | ш | щ | ъ | ы | ь | э | ю | я | 044x
 | 5x | ѐ | ё | ђ | ѓ | є | ѕ | і | ї | ј | љ | њ | ћ | ќ | ѝ | ў | џ | 045x
 | 6x | Ѡ | ѡ | Ѣ | ѣ | Ѥ | ѥ | Ѧ | ѧ | Ѩ | ѩ | Ѫ | ѫ | Ѭ | ѭ | Ѯ | ѯ | 046x
 | 7x | Ѱ | ѱ | Ѳ | ѳ | Ѵ | ѵ | Ѷ | ѷ | Ѹ | ѹ | Ѻ | ѻ | Ѽ | ѽ | Ѿ | ѿ | 047x
 | 8x |  |  |  |  | ΄ | ΅ | Ά | · | Έ | Ή | Ί |  | Ό |  | Ύ | Ώ | 038x | Greek and Coptic
 | 9x | ΐ | Α | Β | Γ | Δ | Ε | Ζ | Η | Θ | Ι | Κ | Λ | Μ | Ν | Ξ | Ο | 039x
 | Ax | Π | Ρ |  | Σ | Τ | Υ | Φ | Χ | Ψ | Ω | Ϊ | Ϋ | ά | έ | ή | ί | 03Ax
 | Bx | ΰ | α | β | γ | δ | ε | ζ | η | θ | ι | κ | λ | μ | ν | ξ | ο | 03Bx
 | Cx | π | ρ | ς | σ | τ | υ | φ | χ | ψ | ω | ϊ | ϋ | ό | ύ | ώ | Ϗ | 03Cx
 | Dx | ϐ | ϑ | ϒ | ϓ | ϔ | ϕ | ϖ | ϗ | Ϙ | ϙ | Ϛ | ϛ | Ϝ | ϝ | Ϟ | ϟ | 03Dx
 | Ex | Ϡ | ϡ | Ϣ | ϣ | Ϥ | ϥ | Ϧ | ϧ | Ϩ | ϩ | Ϫ | ϫ | Ϭ | ϭ | Ϯ | ϯ | 03Ex
 | Fx | ϰ | ϱ | ϲ | ϳ | ϴ | ϵ | ϶ | Ϸ | ϸ | Ϲ | Ϻ | ϻ | ϼ | Ͻ | Ͼ | Ͽ | 03Fx
2 | 0x | IDSP | 、 | 。 | 〃 | 〄 | 々 | 〆 | 〇 | 〈 | 〉 | 《 | 》 | 「 | 」 | 『 | 』 | 300x | CJK Symbols and Punctuation
 | 1x | 【 | 】 | 〒 | 〓 | 〔 | 〕 | 〖 | 〗 | 〘 | 〙 | 〚 | 〛 | 〜 | 〝 | 〞 | 〟 | 301x
 | 2x | 〠 | 〡 | 〢 | 〣 | 〤 | 〥 | 〦 | 〧 | 〨 | 〩 | 〪 | 〫 | 〬 | 〭 | 〮 | 〯 | 302x
 | 3x | 〰 | 〱 | 〲 | 〳 | 〴 | 〵 | 〶 | 〷 | 〸 | 〹 | 〺 | 〻 | 〼 | 〽 | 〾 | 〿 | 303x
 | 4x |  | ぁ | あ | ぃ | い | ぅ | う | ぇ | え | ぉ | お | か | が | き | ぎ | く | 304x | Hiragana
 | 5x | ぐ | け | げ | こ | ご | さ | ざ | し | じ | す | ず | せ | ぜ | そ | ぞ | た | 305x
 | 6x | だ | ち | ぢ | っ | つ | づ | て | で | と | ど | な | に | ぬ | ね | の | は | 306x
 | 7x | ば | ぱ | ひ | び | ぴ | ふ | ぶ | ぷ | へ | べ | ぺ | ほ | ぼ | ぽ | ま | み | 307x
 | 8x | む | め | も | ゃ | や | ゅ | ゆ | ょ | よ | ら | り | る | れ | ろ | ゎ | わ | 308x
 | 9x | ゐ | ゑ | を | ん | ゔ | ゕ | ゖ |  |  | ゙ | ゚ | ゛ | ゜ | ゝ | ゞ | ゟ | 309x
 | Ax | ゠ | ァ | ア | ィ | イ | ゥ | ウ | ェ | エ | ォ | オ | カ | ガ | キ | ギ | ク | 30Ax | Katakana
 | Bx | グ | ケ | ゲ | コ | ゴ | サ | ザ | シ | ジ | ス | ズ | セ | ゼ | ソ | ゾ | タ | 30Bx
 | Cx | ダ | チ | ヂ | ッ | ツ | ヅ | テ | デ | ト | ド | ナ | ニ | ヌ | ネ | ノ | ハ | 30Cx
 | Dx | バ | パ | ヒ | ビ | ピ | フ | ブ | プ | ヘ | ベ | ペ | ホ | ボ | ポ | マ | ミ | 30Dx
 | Ex | ム | メ | モ | ャ | ヤ | ュ | ユ | ョ | ヨ | ラ | リ | ル | レ | ロ | ヮ | ワ | 30Ex
 | Fx | ヰ | ヱ | ヲ | ン | ヴ | ヵ | ヶ | ヷ | ヸ | ヹ | ヺ | ・ | ー | ヽ | ヾ | ヿ | 30Fx
8 | 0x | ─ | ━ | │ | ┃ | ┄ | ┅ | ┆ | ┇ | ┈ | ┉ | ┊ | ┋ | ┌ | ┍ | ┎ | ┏ | 250x | Box Drawing
 | 1x | ┐ | ┑ | ┒ | ┓ | └ | ┕ | ┖ | ┗ | ┘ | ┙ | ┚ | ┛ | ├ | ┝ | ┞ | ┟ | 251x
 | 2x | ┠ | ┡ | ┢ | ┣ | ┤ | ┥ | ┦ | ┧ | ┨ | ┩ | ┪ | ┫ | ┬ | ┭ | ┮ | ┯ | 252x
 | 3x | ┰ | ┱ | ┲ | ┳ | ┴ | ┵ | ┶ | ┷ | ┸ | ┹ | ┺ | ┻ | ┼ | ┽ | ┾ | ┿ | 253x
 | 4x | ╀ | ╁ | ╂ | ╃ | ╄ | ╅ | ╆ | ╇ | ╈ | ╉ | ╊ | ╋ | ╌ | ╍ | ╎ | ╏ | 254x
 | 5x | ═ | ║ | ╒ | ╓ | ╔ | ╕ | ╖ | ╗ | ╘ | ╙ | ╚ | ╛ | ╜ | ╝ | ╞ | ╟ | 255x
 | 6x | ╠ | ╡ | ╢ | ╣ | ╤ | ╥ | ╦ | ╧ | ╨ | ╩ | ╪ | ╫ | ╬ | ╭ | ╮ | ╯ | 256x
 | 7x | ╰ | ╱ | ╲ | ╳ | ╴ | ╵ | ╶ | ╷ | ╸ | ╹ | ╺ | ╻ | ╼ | ╽ | ╾ | ╿ | 257x
 | 8x | ▀ | ▁ | ▂ | ▃ | ▄ | ▅ | ▆ | ▇ | █ | ▉ | ▊ | ▋ | ▌ | ▍ | ▎ | ▏ | 258x | Block Elements
 | 9x | ▐ | ░ | ▒ | ▓ | ▔ | ▕ | ▖ | ▗ | ▘ | ▙ | ▚ | ▛ | ▜ | ▝ | ▞ | ▟ | 259x
 | Ax | ■ | □ | ▢ | ▣ | ▤ | ▥ | ▦ | ▧ | ▨ | ▩ | ▪ | ▫ | ▬ | ▭ | ▮ | ▯ | 25Ax | Geometric Shapes
 | Bx | ▰ | ▱ | ▲ | △ | ▴ | ▵ | ▶ | ▷ | ▸ | ▹ | ► | ▻ | ▼ | ▽ | ▾ | ▿ | 25Bx
 | Cx | ◀ | ◁ | ◂ | ◃ | ◄ | ◅ | ◆ | ◇ | ◈ | ◉ | ◊ | ○ | ◌ | ◍ | ◎ | ● | 25Cx
 | Dx | ◐ | ◑ | ◒ | ◓ | ◔ | ◕ | ◖ | ◗ | ◘ | ◙ | ◚ | ◛ | ◜ | ◝ | ◞ | ◟ | 25Dx
 | Ex | ◠ | ◡ | ◢ | ◣ | ◤ | ◥ | ◦ | ◧ | ◨ | ◩ | ◪ | ◫ | ◬ | ◭ | ◮ | ◯ | 25Ex
 | Fx | ◰ | ◱ | ◲ | ◳ | ◴ | ◵ | ◶ | ◷ | ◸ | ◹ | ◺ | ◻ | ◼ | ◽ | ◾ | ◿ | 25Fx
4 | 0x | NQSP | MQSP | ENSP | EMSP | 3/MSP | 4/MSP | 6/MSP | FSP | PSP | THSP | HSP | ZWSP | ZWNJ | ZW J | LRM | RLM | 200x | General Punctuation
 | 1x | ‐ | NB | ‒ | – | — | ― | ‖ | ‗ | ‘ | ’ | ‚ | ‛ | “ | ” | „ | ‟ | 201x
 | 2x | † | ‡ | • | ‣ | ․ | ‥ | … | ‧ | LSEP | PSEP | LRE | RLE | PDF | LRO | RLO | NNBSP | 202x
 | 3x | ‰ | ‱ | ′ | ″ | ‴ | ‵ | ‶ | ‷ | ‸ | ‹ | › | ※ | ‼ | ‽ | ‾ | ‿ | 203x
 | 4x | ⁀ | ⁁ | ⁂ | ⁃ | ⁄ | ⁅ | ⁆ | ⁇ | ⁈ | ⁉ | ⁊ | ⁋ | ⁌ | ⁍ | ⁎ | ⁏ | 204x
 | 5x | ⁐ | ⁑ | ⁒ | ⁓ | ⁔ | ⁕ | ⁖ | ⁗ | ⁘ | ⁙ | ⁚ | ⁛ | ⁜ | ⁝ | ⁞ | MMSP | 205x
 | 6x | WJ | ƒ() | × | , | + |  | LRI | RLI | FSI | PDI | ISS | ASS | IAFS | AAFS | NADS | NODS | 206x
 | 7x | ⑀ | ⑁ | ⑂ | ⑃ | ⑄ | ⑅ | ⑆ | ⑇ | ⑈ | ⑉ | ⑊ |  |  |  |  |  | 244x | Optical Character Recognition
 | 8x | ⸀ | ⸁ | ⸂ | ⸃ | ⸄ | ⸅ | ⸆ | ⸇ | ⸈ | ⸉ | ⸊ | ⸋ | ⸌ | ⸍ | ⸎ | ⸏ | 2E0x | Supplemental Punctuation
 | 9x | ⸐ | ⸑ | ⸒ | ⸓ | ⸔ | ⸕ | ⸖ | ⸗ | ⸘ | ⸙ | ⸚ | ⸛ | ⸜ | ⸝ | ⸞ | ⸟ | 2E1x
 | Ax | ⸠ | ⸡ | ⸢ | ⸣ | ⸤ | ⸥ | ⸦ | ⸧ | ⸨ | ⸩ | ⸪ | ⸫ | ⸬ | ⸭ | ⸮ | ⸯ | 2E2x
 | Bx | ⸰ | ⸱ | ⸲ | ⸳ | ⸴ | ⸵ | ⸶ | ⸷ | ⸸ | ⸹ | 2M⸺ | 3M⸻ | ⸼ | ⸽ | ⸾ | ⸿ | 2E3x
 | Cx | ⹀ | ⹁ | ⹂ | ⹃ | ⹄ | ⹅ | ⹆ | ⹇ | ⹈ | ⹉ | ⹊ | ⹋ | ⹌ | ⹍ | ⹎ | ⹏ | 2E4x
 | Dx | ⹐ | ⹑ | ⹒ | ⹓ | ⹔ | ⹕ | ⹖ | ⹗ | ⹘ | ⹙ | ⹚ | ⹛ | ⹜ | ⹝ |  |  | 2E5x
 | Ex
 | Fx
3 | 0x | ℀ | ℁ | ℂ | ℃ | ℄ | ℅ | ℆ | ℇ | ℈ | ℉ | ℊ | ℋ | ℌ | ℍ | ℎ | ℏ | 210x | Letterlike Symbols
 | 1x | ℐ | ℑ | ℒ | ℓ | ℔ | ℕ | № | ℗ | ℘ | ℙ | ℚ | ℛ | ℜ | ℝ | ℞ | ℟ | 211x
 | 2x | ℠ | ℡ | ™ | ℣ | ℤ | ℥ | Ω | ℧ | ℨ | ℩ | K | Å | ℬ | ℭ | ℮ | ℯ | 212x
 | 3x | ℰ | ℱ | Ⅎ | ℳ | ℴ | ℵ | ℶ | ℷ | ℸ | ℹ | ℺ | ℻ | ℼ | ℽ | ℾ | ℿ | 213x
 | 4x | ⅀ | ⅁ | ⅂ | ⅃ | ⅄ | ⅅ | ⅆ | ⅇ | ⅈ | ⅉ | ⅊ | ⅋ | ⅌ | ⅍ | ⅎ | ⅏ | 214x
 | 5x | ⅐ | ⅑ | ⅒ | ⅓ | ⅔ | ⅕ | ⅖ | ⅗ | ⅘ | ⅙ | ⅚ | ⅛ | ⅜ | ⅝ | ⅞ | ⅟ | 215x | Number Forms
 | 6x | Ⅰ | Ⅱ | Ⅲ | Ⅳ | Ⅴ | Ⅵ | Ⅶ | Ⅷ | Ⅸ | Ⅹ | Ⅺ | Ⅻ | Ⅼ | Ⅽ | Ⅾ | Ⅿ | 216x
 | 7x | ⅰ | ⅱ | ⅲ | ⅳ | ⅴ | ⅵ | ⅶ | ⅷ | ⅸ | ⅹ | ⅺ | ⅻ | ⅼ | ⅽ | ⅾ | ⅿ | 217x
 | 8x | ↀ | ↁ | ↂ | Ↄ | ↄ | ↅ | ↆ | ↇ | ↈ | ↉ | ↊ | ↋ |  |  |  |  | 218x
 | 9x
 | Ax | ₠ | ₡ | ₢ | ₣ | ₤ | ₥ | ₦ | ₧ | ₨ | ₩ | ₪ | ₫ | € | ₭ | ₮ | ₯ | 20Ax | Currency Symbols
 | Bx | ₰ | ₱ | ₲ | ₳ | ₴ | ₵ | ₶ | ₷ | ₸ | ₹ | ₺ | ₻ | ₼ | ₽ | ₾ | ₿ | 20Bx
 | Cx
 | Dx
 | Ex
 | Fx
6 | 0x | ∀ | ∁ | ∂ | ∃ | ∄ | ∅ | ∆ | ∇ | ∈ | ∉ | ∊ | ∋ | ∌ | ∍ | ∎ | ∏ | 220x | Mathematical Operators
 | 1x | ∐ | ∑ | − | ∓ | ∔ | ∕ | ∖ | ∗ | ∘ | ∙ | √ | ∛ | ∜ | ∝ | ∞ | ∟ | 221x
 | 2x | ∠ | ∡ | ∢ | ∣ | ∤ | ∥ | ∦ | ∧ | ∨ | ∩ | ∪ | ∫ | ∬ | ∭ | ∮ | ∯ | 222x
 | 3x | ∰ | ∱ | ∲ | ∳ | ∴ | ∵ | ∶ | ∷ | ∸ | ∹ | ∺ | ∻ | ∼ | ∽ | ∾ | ∿ | 223x
 | 4x | ≀ | ≁ | ≂ | ≃ | ≄ | ≅ | ≆ | ≇ | ≈ | ≉ | ≊ | ≋ | ≌ | ≍ | ≎ | ≏ | 224x
 | 5x | ≐ | ≑ | ≒ | ≓ | ≔ | ≕ | ≖ | ≗ | ≘ | ≙ | ≚ | ≛ | ≜ | ≝ | ≞ | ≟ | 225x
 | 6x | ≠ | ≡ | ≢ | ≣ | ≤ | ≥ | ≦ | ≧ | ≨ | ≩ | ≪ | ≫ | ≬ | ≭ | ≮ | ≯ | 226x
 | 7x | ≰ | ≱ | ≲ | ≳ | ≴ | ≵ | ≶ | ≷ | ≸ | ≹ | ≺ | ≻ | ≼ | ≽ | ≾ | ≿ | 227x
 | 8x | ⊀ | ⊁ | ⊂ | ⊃ | ⊄ | ⊅ | ⊆ | ⊇ | ⊈ | ⊉ | ⊊ | ⊋ | ⊌ | ⊍ | ⊎ | ⊏ | 228x
 | 9x | ⊐ | ⊑ | ⊒ | ⊓ | ⊔ | ⊕ | ⊖ | ⊗ | ⊘ | ⊙ | ⊚ | ⊛ | ⊜ | ⊝ | ⊞ | ⊟ | 229x
 | Ax | ⊠ | ⊡ | ⊢ | ⊣ | ⊤ | ⊥ | ⊦ | ⊧ | ⊨ | ⊩ | ⊪ | ⊫ | ⊬ | ⊭ | ⊮ | ⊯ | 22Ax
 | Bx | ⊰ | ⊱ | ⊲ | ⊳ | ⊴ | ⊵ | ⊶ | ⊷ | ⊸ | ⊹ | ⊺ | ⊻ | ⊼ | ⊽ | ⊾ | ⊿ | 22Bx
 | Cx | ⋀ | ⋁ | ⋂ | ⋃ | ⋄ | ⋅ | ⋆ | ⋇ | ⋈ | ⋉ | ⋊ | ⋋ | ⋌ | ⋍ | ⋎ | ⋏ | 22Cx
 | Dx | ⋐ | ⋑ | ⋒ | ⋓ | ⋔ | ⋕ | ⋖ | ⋗ | ⋘ | ⋙ | ⋚ | ⋛ | ⋜ | ⋝ | ⋞ | ⋟ | 22Dx
 | Ex | ⋠ | ⋡ | ⋢ | ⋣ | ⋤ | ⋥ | ⋦ | ⋧ | ⋨ | ⋩ | ⋪ | ⋫ | ⋬ | ⋭ | ⋮ | ⋯ | 22Ex
 | Fx | ⋰ | ⋱ | ⋲ | ⋳ | ⋴ | ⋵ | ⋶ | ⋷ | ⋸ | ⋹ | ⋺ | ⋻ | ⋼ | ⋽ | ⋾ | ⋿ | 22Fx
B | 0x | 🬀 | 🬁 | 🬂 | 🬃 | 🬄 | 🬅 | 🬆 | 🬇 | 🬈 | 🬉 | 🬊 | 🬋 | 🬌 | 🬍 | 🬎 | 🬏 | 1FB0x | Symbols for Legacy Computing
 | 1x | 🬐 | 🬑 | 🬒 | 🬓 | 🬔 | 🬕 | 🬖 | 🬗 | 🬘 | 🬙 | 🬚 | 🬛 | 🬜 | 🬝 | 🬞 | 🬟 | 1FB1x
 | 2x | 🬠 | 🬡 | 🬢 | 🬣 | 🬤 | 🬥 | 🬦 | 🬧 | 🬨 | 🬩 | 🬪 | 🬫 | 🬬 | 🬭 | 🬮 | 🬯 | 1FB2x
 | 3x | 🬰 | 🬱 | 🬲 | 🬳 | 🬴 | 🬵 | 🬶 | 🬷 | 🬸 | 🬹 | 🬺 | 🬻 | 🬼 | 🬽 | 🬾 | 🬿 | 1FB3x
 | 4x | 🭀 | 🭁 | 🭂 | 🭃 | 🭄 | 🭅 | 🭆 | 🭇 | 🭈 | 🭉 | 🭊 | 🭋 | 🭌 | 🭍 | 🭎 | 🭏 | 1FB4x
 | 5x | 🭐 | 🭑 | 🭒 | 🭓 | 🭔 | 🭕 | 🭖 | 🭗 | 🭘 | 🭙 | 🭚 | 🭛 | 🭜 | 🭝 | 🭞 | 🭟 | 1FB5x
 | 6x | 🭠 | 🭡 | 🭢 | 🭣 | 🭤 | 🭥 | 🭦 | 🭧 | 🭨 | 🭩 | 🭪 | 🭫 | 🭬 | 🭭 | 🭮 | 🭯 | 1FB6x
 | 7x | 🭰 | 🭱 | 🭲 | 🭳 | 🭴 | 🭵 | 🭶 | 🭷 | 🭸 | 🭹 | 🭺 | 🭻 | 🭼 | 🭽 | 🭾 | 🭿 | 1FB7x
 | 8x | 🮀 | 🮁 | 🮂 | 🮃 | 🮄 | 🮅 | 🮆 | 🮇 | 🮈 | 🮉 | 🮊 | 🮋 | 🮌 | 🮍 | 🮎 | 🮏 | 1FB8x
 | 9x | 🮐 | 🮑 | 🮒 |  | 🮔 | 🮕 | 🮖 | 🮗 | 🮘 | 🮙 | 🮚 | 🮛 | 🮜 | 🮝 | 🮞 | 🮟 | 1FB9x
 | Ax | 🮠 | 🮡 | 🮢 | 🮣 | 🮤 | 🮥 | 🮦 | 🮧 | 🮨 | 🮩 | 🮪 | 🮫 | 🮬 | 🮭 | 🮮 | 🮯 | 1FBAx
 | Bx | 🮰 | 🮱 | 🮲 | 🮳 | 🮴 | 🮵 | 🮶 | 🮷 | 🮸 | 🮹 | 🮺 | 🮻 | 🮼 | 🮽 | 🮾 | 🮿 | 1FBBx
 | Cx | 🯀 | 🯁 | 🯂 | 🯃 | 🯄 | 🯅 | 🯆 | 🯇 | 🯈 | 🯉 | 🯊 |  |  |  |  |  | 1FBCx
 | Dx | 🜀 | 🜁 | 🜂 | 🜃 | 🜄 | 🜅 | 🜆 | 🜇 | 🜈 | 🜉 | 🜊 | 🜋 | 🜌 | 🜍 | 🜎 | 🜏 | 1F70x | Alchemical Symbols
 | Ex | 🜐 | 🜑 | 🜒 | 🜓 | 🜔 | 🜕 | 🜖 | 🜗 | 🜘 | 🜙 | 🜚 | 🜛 | 🜜 | 🜝 | 🜞 | 🜟 | 1F71x
 | Fx | 🯰 | 🯱 | 🯲 | 🯳 | 🯴 | 🯵 | 🯶 | 🯷 | 🯸 | 🯹 |  |  |  |  |  |  | 1FBFx | Symbols for Legacy Computing
A | 0x | SP | ! | " | # | $ | % | & | ' | ( | ) | * | + | , | - | . | / | N/A | Superscript Symbols
 | 1x | 0 | 1 | 2 | 3 | 4 | 5 | 6 | 7 | 8 | 9 | : | ; | < | = | > | ? | N/A
 | 2x | @ | A | B | C | D | E | F | G | H | I | J | K | L | M | N | O | N/A
 | 3x | P | Q | R | S | T | U | V | W | X | Y | Z | [ | \ | ] | ^ | _ | N/A
 | 4x | ` | a | b | c | d | e | f | g | h | i | j | k | l | m | n | o | N/A
 | 5x | p | q | r | s | t | u | v | w | x | y | z | { | | | } | ~ | ± | N/A
 | 6x | § | α | β | γ | δ | ε | ζ | η | θ | ι | κ | λ | μ | ν | ξ | ο | N/A
 | 7x | π | ρ | ς | σ | τ | υ | φ | χ | ψ | ω | Δ | Θ | Ξ | Π | Σ | Ω | N/A
 | 8x | SP | ! | " | # | $ | % | & | ' | ( | ) | * | + | , | - | . | / | N/A | Subscript Symbols
 | 9x | 0 | 1 | 2 | 3 | 4 | 5 | 6 | 7 | 8 | 9 | : | ; | < | = | > | ? | N/A
 | Ax | @ | A | B | C | D | E | F | G | H | I | J | K | L | M | N | O | N/A
 | Bx | P | Q | R | S | T | U | V | W | X | Y | Z | [ | \ | ] | ^ | _ | N/A
 | Cx | ` | a | b | c | d | e | f | g | h | i | j | k | l | m | n | o | N/A
 | Dx | p | q | r | s | t | u | v | w | x | y | z | { | | | } | ~ | ± | N/A
 | Ex | § | α | β | γ | δ | ε | ζ | η | θ | ι | κ | λ | μ | ν | ξ | ο | N/A
 | Fx | π | ρ | ς | σ | τ | υ | φ | χ | ψ | ω | Δ | Θ | Ξ | Π | Σ | Ω | N/A
5 | 0x | ⦀ | ⦁ | ⦂ | ⦃ | ⦄ | ⦅ | ⦆ | ⦇ | ⦈ | ⦉ | ⦊ | ⦋ | ⦌ | ⦍ | ⦎ | ⦏ | 298x | Miscellaneous Mathematical Symbols-B
 | 1x | ⦐ | ⦑ | ⦒ | ⦓ | ⦔ | ⦕ | ⦖ | ⦗ | ⦘ | ⦙ | ⦚ | ⦛ | ⦜ | ⦝ | ⦞ | ⦟ | 299x
 | 2x | ⦠ | ⦡ | ⦢ | ⦣ | ⦤ | ⦥ | ⦦ | ⦧ | ⦨ | ⦩ | ⦪ | ⦫ | ⦬ | ⦭ | ⦮ | ⦯ | 29Ax
 | 3x | ⦰ | ⦱ | ⦲ | ⦳ | ⦴ | ⦵ | ⦶ | ⦷ | ⦸ | ⦹ | ⦺ | ⦻ | ⦼ | ⦽ | ⦾ | ⦿ | 29Bx
 | 4x | ⧀ | ⧁ | ⧂ | ⧃ | ⧄ | ⧅ | ⧆ | ⧇ | ⧈ | ⧉ | ⧊ | ⧋ | ⧌ | ⧍ | ⧎ | ⧏ | 29Cx
 | 5x | ⧐ | ⧑ | ⧒ | ⧓ | ⧔ | ⧕ | ⧖ | ⧗ | ⧘ | ⧙ | ⧚ | ⧛ | ⧜ | ⧝ | ⧞ | ⧟ | 29Dx
 | 6x | ⧠ | ⧡ | ⧢ | ⧣ | ⧤ | ⧥ | ⧦ | ⧧ | ⧨ | ⧩ | ⧪ | ⧫ | ⧬ | ⧭ | ⧮ | ⧯ | 29Ex
 | 7x | ⧰ | ⧱ | ⧲ | ⧳ | ⧴ | ⧵ | ⧶ | ⧷ | ⧸ | ⧹ | ⧺ | ⧻ | ⧼ | ⧽ | ⧾ | ⧿ | 29Fx
 | 8x | ⟀ | ⟁ | ⟂ | ⟃ | ⟄ | ⟅ | ⟆ | ⟇ | ⟈ | ⟉ | ⟊ | ⟋ | ⟌ | ⟍ | ⟎ | ⟏ | 27Cx | Miscellaneous Mathematical Symbols-A
 | 9x | ⟐ | ⟑ | ⟒ | ⟓ | ⟔ | ⟕ | ⟖ | ⟗ | ⟘ | ⟙ | ⟚ | ⟛ | ⟜ | ⟝ | ⟞ | ⟟ | 27Dx
 | Ax | ⟠ | ⟡ | ⟢ | ⟣ | ⟤ | ⟥ | ⟦ | ⟧ | ⟨ | ⟩ | ⟪ | ⟫ | ⟬ | ⟭ | ⟮ | ⟯ | 27Ex
 | Bx | ← | ↑ | → | ↓ | ↔ | ↕ | ↖ | ↗ | ↘ | ↙ | ↚ | ↛ | ↜ | ↝ | ↞ | ↟ | 219x | Arrows
 | Cx | ↠ | ↡ | ↢ | ↣ | ↤ | ↥ | ↦ | ↧ | ↨ | ↩ | ↪ | ↫ | ↬ | ↭ | ↮ | ↯ | 21Ax
 | Dx | ↰ | ↱ | ↲ | ↳ | ↴ | ↵ | ↶ | ↷ | ↸ | ↹ | ↺ | ↻ | ↼ | ↽ | ↾ | ↿ | 21Bx
 | Ex | ⇀ | ⇁ | ⇂ | ⇃ | ⇄ | ⇅ | ⇆ | ⇇ | ⇈ | ⇉ | ⇊ | ⇋ | ⇌ | ⇍ | ⇎ | ⇏ | 21Cx
 | Fx | ⇐ | ⇑ | ⇒ | ⇓ | ⇔ | ⇕ | ⇖ | ⇗ | ⇘ | ⇙ | ⇚ | ⇛ | ⇜ | ⇝ | ⇞ | ⇟ | 21Dx
9 | 0x | ⬀ | ⬁ | ⬂ | ⬃ | ⬄ | ⬅ | ⬆ | ⬇ | ⬈ | ⬉ | ⬊ | ⬋ | ⬌ | ⬍ | ⬎ | ⬏ | 2B0x | Miscellaneous Symbols and Arrows
 | 1x | ⬐ | ⬑ | ⬒ | ⬓ | ⬔ | ⬕ | ⬖ | ⬗ | ⬘ | ⬙ | ⬚ | ⬛ | ⬜ | ⬝ | ⬞ | ⬟ | 2B1x
 | 2x | ⬠ | ⬡ | ⬢ | ⬣ | ⬤ | ⬥ | ⬦ | ⬧ | ⬨ | ⬩ | ⬪ | ⬫ | ⬬ | ⬭ | ⬮ | ⬯ | 2B2x
 | 3x | ⬰ | ⬱ | ⬲ | ⬳ | ⬴ | ⬵ | ⬶ | ⬷ | ⬸ | ⬹ | ⬺ | ⬻ | ⬼ | ⬽ | ⬾ | ⬿ | 2B3x
 | 4x | ⭀ | ⭁ | ⭂ | ⭃ | ⭄ | ⭅ | ⭆ | ⭇ | ⭈ | ⭉ | ⭊ | ⭋ | ⭌ | ⭍ | ⭎ | ⭏ | 2B4x
 | 5x | ⭐ | ⭑ | ⭒ | ⭓ | ⭔ | ⭕ | ⭖ | ⭗ | ⭘ | ⭙ | ⭚ | ⭛ | ⭜ | ⭝ | ⭞ | ⭟ | 2B5x
 | 6x | ⭠ | ⭡ | ⭢ | ⭣ | ⭤ | ⭥ | ⭦ | ⭧ | ⭨ | ⭩ | ⭪ | ⭫ | ⭬ | ⭭ | ⭮ | ⭯ | 2B6x
 | 7x | ⭰ | ⭱ | ⭲ | ⭳ |  |  | ⭶ | ⭷ | ⭸ | ⭹ | ⭺ | ⭻ | ⭼ | ⭽ | ⭾ | ⭿ | 2B7x
 | 8x | ☀ | ☁ | ☂ | ☃ | ☄ | ★ | ☆ | ☇ | ☈ | ☉ | ☊ | ☋ | ☌ | ☍ | ☎ | ☏ | 260x | Miscellaneous Symbols
 | 9x | ☐ | ☑ | ☒ | ☓ | ☔ | ☕ | ☖ | ☗ | ☘ | ☙ | ☚ | ☛ | ☜ | ☝ | ☞ | ☟ | 261x
 | Ax | ☠ | ☡ | ☢ | ☣ | ☤ | ☥ | ☦ | ☧ | ☨ | ☩ | ☪ | ☫ | ☬ | ☭ | ☮ | ☯ | 262x
 | Bx | ☰ | ☱ | ☲ | ☳ | ☴ | ☵ | ☶ | ☷ | ☸ | ☹ | ☺ | ☻ | ☼ | ☽ | ☾ | ☿ | 263x
 | Cx | ♀ | ♁ | ♂ | ♃ | ♄ | ♅ | ♆ | ♇ | ♈ | ♉ | ♊ | ♋ | ♌ | ♍ | ♎ | ♏ | 264x
 | Dx | ♐ | ♑ | ♒ | ♓ | ♔ | ♕ | ♖ | ♗ | ♘ | ♙ | ♚ | ♛ | ♜ | ♝ | ♞ | ♟ | 265x
 | Ex | ♠ | ♡ | ♢ | ♣ | ♤ | ♥ | ♦ | ♧ | ♨ | ♩ | ♪ | ♫ | ♬ | ♭ | ♮ | ♯ | 266x
 | Fx | ♰ | ♱ | ♲ | ♳ | ♴ | ♵ | ♶ | ♷ | ♸ | ♹ | ♺ | ♻ | ♼ | ♽ | ♾ | ♿ | 267x
7 | 0x | ⌀ | ⌁ | ⌂ | ⌃ | ⌄ | ⌅ | ⌆ | ⌇ | ⌈ | ⌉ | ⌊ | ⌋ | ⌌ | ⌍ | ⌎ | ⌏ | 230x | Miscellaneous Technical
 | 1x | ⌐ | ⌑ | ⌒ | ⌓ | ⌔ | ⌕ | ⌖ | ⌗ | ⌘ | ⌙ | ⌚ | ⌛ | ⌜ | ⌝ | ⌞ | ⌟ | 231x
 | 2x | ⌠ | ⌡ | ⌢ | ⌣ | ⌤ | ⌥ | ⌦ | ⌧ | ⌨ | 〈 | 〉 | ⌫ | ⌬ | ⌭ | ⌮ | ⌯ | 232x
 | 3x | ⌰ | ⌱ | ⌲ | ⌳ | ⌴ | ⌵ | ⌶ | ⌷ | ⌸ | ⌹ | ⌺ | ⌻ | ⌼ | ⌽ | ⌾ | ⌿ | 233x
 | 4x | ⍀ | ⍁ | ⍂ | ⍃ | ⍄ | ⍅ | ⍆ | ⍇ | ⍈ | ⍉ | ⍊ | ⍋ | ⍌ | ⍍ | ⍎ | ⍏ | 234x
 | 5x | ⍐ | ⍑ | ⍒ | ⍓ | ⍔ | ⍕ | ⍖ | ⍗ | ⍘ | ⍙ | ⍚ | ⍛ | ⍜ | ⍝ | ⍞ | ⍟ | 235x
 | 6x | ⍠ | ⍡ | ⍢ | ⍣ | ⍤ | ⍥ | ⍦ | ⍧ | ⍨ | ⍩ | ⍪ | ⍫ | ⍬ | ⍭ | ⍮ | ⍯ | 236x
 | 7x | ⍰ | ⍱ | ⍲ | ⍳ | ⍴ | ⍵ | ⍶ | ⍷ | ⍸ | ⍹ | ⍺ | ⍻ | ⍼ | ⍽ | ⍾ | ⍿ | 237x
 | 8x | ⎀ | ⎁ | ⎂ | ⎃ | ⎄ | ⎅ | ⎆ | ⎇ | ⎈ | ⎉ | ⎊ | ⎋ | ⎌ | ⎍ | ⎎ | ⎏ | 238x
 | 9x | ⎐ | ⎑ | ⎒ | ⎓ | ⎔ | ⎕ | ⎖ | ⎗ | ⎘ | ⎙ | ⎚ | ⎛ | ⎜ | ⎝ | ⎞ | ⎟ | 239x
 | Ax | ⎠ | ⎡ | ⎢ | ⎣ | ⎤ | ⎥ | ⎦ | ⎧ | ⎨ | ⎩ | ⎪ | ⎫ | ⎬ | ⎭ | ⎮ | ⎯ | 23Ax
 | Bx | ⎰ | ⎱ | ⎲ | ⎳ | ⎴ | ⎵ | ⎶ | ⎷ | ⎸ | ⎹ | ⎺ | ⎻ | ⎼ | ⎽ | ⎾ | ⎿ | 23Bx
 | Cx | ⏀ | ⏁ | ⏂ | ⏃ | ⏄ | ⏅ | ⏆ | ⏇ | ⏈ | ⏉ | ⏊ | ⏋ | ⏌ | ⏍ | ⏎ | ⏏ | 23Cx
 | Dx | ⏐ | ⏑ | ⏒ | ⏓ | ⏔ | ⏕ | ⏖ | ⏗ | ⏘ | ⏙ | ⏚ | ⏛ | ⏜ | ⏝ | ⏞ | ⏟ | 23Dx
 | Ex | ⏠ | ⏡ | ⏢ | ⏣ | ⏤ | ⏥ | ⏦ | ⏧ | ⏨ | ⏩ | ⏪ | ⏫ | ⏬ | ⏭ | ⏮ | ⏯ | 23Ex
 | Fx | ⏰ | ⏱ | ⏲ | ⏳ | ⏴ | ⏵ | ⏶ | ⏷ | ⏸ | ⏹ | ⏺ | ⏻ | ⏼ | ⏽ | ⏾ | ⏿ | 23Fx
C | 0x |  |  |  |  |  |  |  |  |  |  |  |  |  |  |  |  | N/A | Allocated for User Definition
 | 1x |  |  |  |  |  |  |  |  |  |  |  |  |  |  |  |  | N/A
 | 2x |  |  |  |  |  |  |  |  |  |  |  |  |  |  |  |  | N/A
 | 3x |  |  |  |  |  |  |  |  |  |  |  |  |  |  |  |  | N/A
 | 4x |  |  |  |  |  |  |  |  |  |  |  |  |  |  |  |  | N/A
 | 5x |  |  |  |  |  |  |  |  |  |  |  |  |  |  |  |  | N/A
 | 6x |  |  |  |  |  |  |  |  |  |  |  |  |  |  |  |  | N/A
 | 7x |  |  |  |  |  |  |  |  |  |  |  |  |  |  |  |  | N/A
 | 8x |  |  |  |  |  |  |  |  |  |  |  |  |  |  |  |  | N/A
 | 9x |  |  |  |  |  |  |  |  |  |  |  |  |  |  |  |  | N/A
 | Ax |  |  |  |  |  |  |  |  |  |  |  |  |  |  |  |  | N/A
 | Bx |  |  |  |  |  |  |  |  |  |  |  |  |  |  |  |  | N/A
 | Cx |  |  |  |  |  |  |  |  |  |  |  |  |  |  |  |  | N/A
 | Dx |  |  |  |  |  |  |  |  |  |  |  |  |  |  |  |  | N/A
 | Ex |  |  |  |  |  |  |  |  |  |  |  |  |  |  |  |  | N/A
 | Fx |  |  |  |  |  |  |  |  |  |  |  |  |  |  |  |  | N/A
D | 0x |  |  |  |  |  |  |  |  |  |  |  |  |  |  |  |  | N/A | Allocated for User Definition
 | 1x |  |  |  |  |  |  |  |  |  |  |  |  |  |  |  |  | N/A
 | 2x |  |  |  |  |  |  |  |  |  |  |  |  |  |  |  |  | N/A
 | 3x |  |  |  |  |  |  |  |  |  |  |  |  |  |  |  |  | N/A
 | 4x |  |  |  |  |  |  |  |  |  |  |  |  |  |  |  |  | N/A
 | 5x |  |  |  |  |  |  |  |  |  |  |  |  |  |  |  |  | N/A
 | 6x |  |  |  |  |  |  |  |  |  |  |  |  |  |  |  |  | N/A
 | 7x |  |  |  |  |  |  |  |  |  |  |  |  |  |  |  |  | N/A
 | 8x |  |  |  |  |  |  |  |  |  |  |  |  |  |  |  |  | N/A
 | 9x |  |  |  |  |  |  |  |  |  |  |  |  |  |  |  |  | N/A
 | Ax |  |  |  |  |  |  |  |  |  |  |  |  |  |  |  |  | N/A
 | Bx |  |  |  |  |  |  |  |  |  |  |  |  |  |  |  |  | N/A
 | Cx |  |  |  |  |  |  |  |  |  |  |  |  |  |  |  |  | N/A
 | Dx |  |  |  |  |  |  |  |  |  |  |  |  |  |  |  |  | N/A
 | Ex |  |  |  |  |  |  |  |  |  |  |  |  |  |  |  |  | N/A
 | Fx |  |  |  |  |  |  |  |  |  |  |  |  |  |  |  |  | N/A
E | 0x |  |  |  |  |  |  |  |  |  |  |  |  |  |  |  |  | N/A | Allocated for User Definition
 | 1x |  |  |  |  |  |  |  |  |  |  |  |  |  |  |  |  | N/A
 | 2x |  |  |  |  |  |  |  |  |  |  |  |  |  |  |  |  | N/A
 | 3x |  |  |  |  |  |  |  |  |  |  |  |  |  |  |  |  | N/A
 | 4x |  |  |  |  |  |  |  |  |  |  |  |  |  |  |  |  | N/A
 | 5x |  |  |  |  |  |  |  |  |  |  |  |  |  |  |  |  | N/A
 | 6x |  |  |  |  |  |  |  |  |  |  |  |  |  |  |  |  | N/A
 | 7x |  |  |  |  |  |  |  |  |  |  |  |  |  |  |  |  | N/A
 | 8x |  |  |  |  |  |  |  |  |  |  |  |  |  |  |  |  | N/A
 | 9x |  |  |  |  |  |  |  |  |  |  |  |  |  |  |  |  | N/A
 | Ax |  |  |  |  |  |  |  |  |  |  |  |  |  |  |  |  | N/A
 | Bx |  |  |  |  |  |  |  |  |  |  |  |  |  |  |  |  | N/A
 | Cx |  |  |  |  |  |  |  |  |  |  |  |  |  |  |  |  | N/A
 | Dx |  |  |  |  |  |  |  |  |  |  |  |  |  |  |  |  | N/A
 | Ex |  |  |  |  |  |  |  |  |  |  |  |  |  |  |  |  | N/A
 | Fx |  |  |  |  |  |  |  |  |  |  |  |  |  |  |  |  | N/A
F | 0x |  |  |  |  |  |  |  |  |  |  |  |  |  |  |  |  | N/A | Allocated for User Definition
 | 1x |  |  |  |  |  |  |  |  |  |  |  |  |  |  |  |  | N/A
 | 2x |  |  |  |  |  |  |  |  |  |  |  |  |  |  |  |  | N/A
 | 3x |  |  |  |  |  |  |  |  |  |  |  |  |  |  |  |  | N/A
 | 4x |  |  |  |  |  |  |  |  |  |  |  |  |  |  |  |  | N/A
 | 5x |  |  |  |  |  |  |  |  |  |  |  |  |  |  |  |  | N/A
 | 6x |  |  |  |  |  |  |  |  |  |  |  |  |  |  |  |  | N/A
 | 7x |  |  |  |  |  |  |  |  |  |  |  |  |  |  |  |  | N/A
 | 8x |  |  |  |  |  |  |  |  |  |  |  |  |  |  |  |  | N/A
 | 9x |  |  |  |  |  |  |  |  |  |  |  |  |  |  |  |  | N/A
 | Ax |  |  |  |  |  |  |  |  |  |  |  |  |  |  |  |  | N/A
 | Bx |  |  |  |  |  |  |  |  |  |  |  |  |  |  |  |  | N/A
 | Cx |  |  |  |  |  |  |  |  |  |  |  |  |  |  |  |  | N/A
 | Dx |  |  |  |  |  |  |  |  |  |  |  |  |  |  |  |  | N/A
 | Ex |  |  |  |  |  |  |  |  |  |  |  |  |  |  |  |  | N/A
 | Fx |  |  |  |  |  |  |  |  |  |  |  |  |  |  |  |  | N/A
