Julesc013/abacus-2/hardware/instructions/i03.JPG

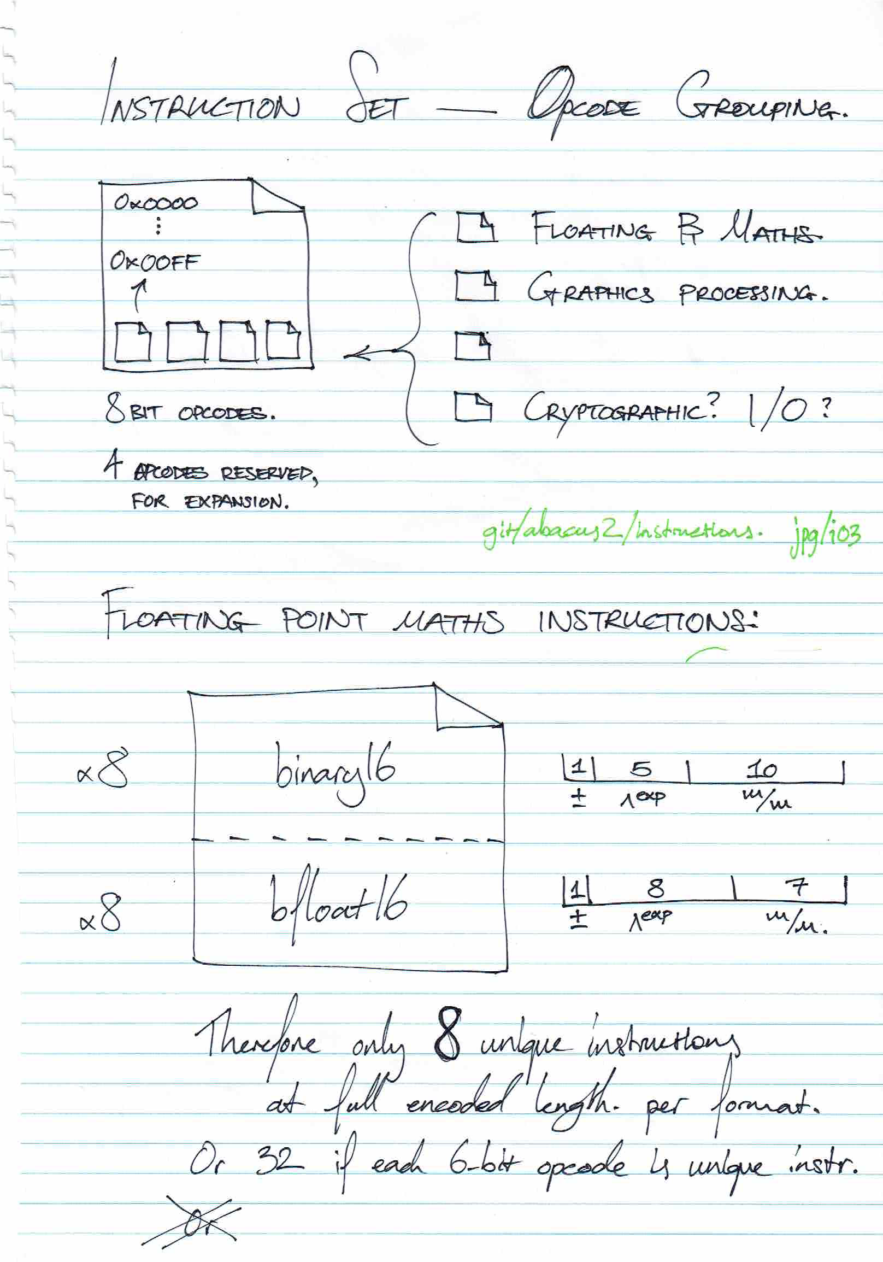
hardware/instructions/i03.JPG
