Julesc013/abacus-2/hardware/video/video_adapter/fonts/Test Greek Cyrillic.jpg

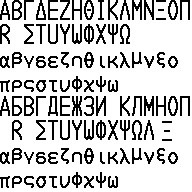
hardware/video/video_adapter/fonts/Test Greek Cyrillic.jpg
