Julesc013/abacus-2/hardware/video/video_adapter/CDA Modes.pdf

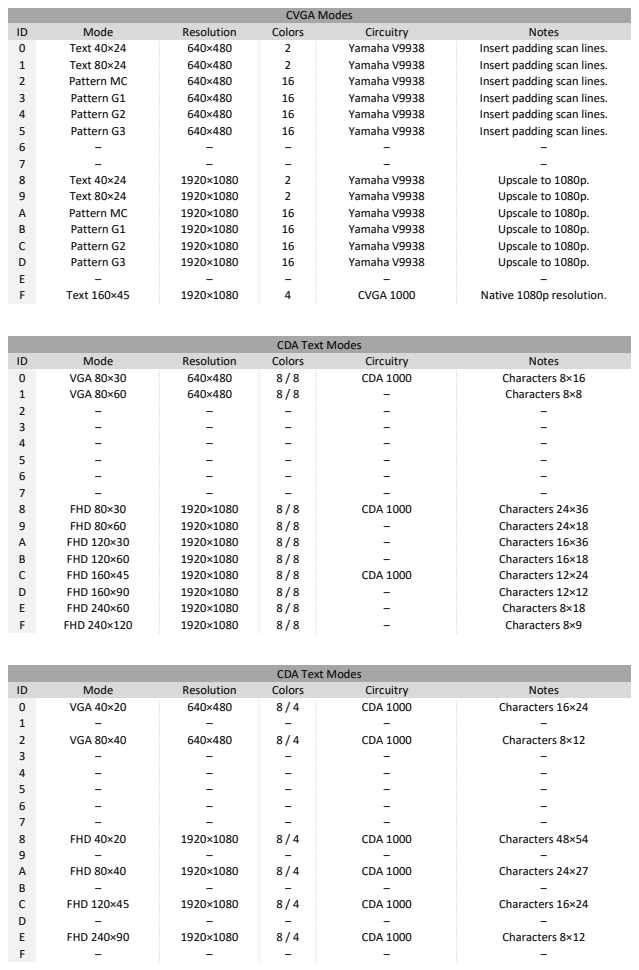
[picture p55: page 1]
Mode; Resolution; Colors; Circuitry; Notes; Text 40×24; Yamaha V9938; Insert padding scan lines.; Text 80×24; Pattern MC; Pattern G1; Pattern G2; Pattern G3; Upscale to 1080p.; Text 160×45; CVGA 1000; Native 1080p resolution.; VGA 80×30; CDA 1000; Characters 8×16; VGA 80×60; Characters 8×8; FHD 80×30; Characters 24×36; FHD 80×60; Characters 24×18; FHD 120×30; Characters 16×36; FHD 120×60; Characters 16×18; FHD 160×45; Characters 12×24; FHD 160×90; Characters 12×12; FHD 240×60; Characters 8×18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

CDA Text Modes
