Julesc013/abacus-2/schematics/carbonATX/CarbonZ80/200x300_64pin_4.pdf

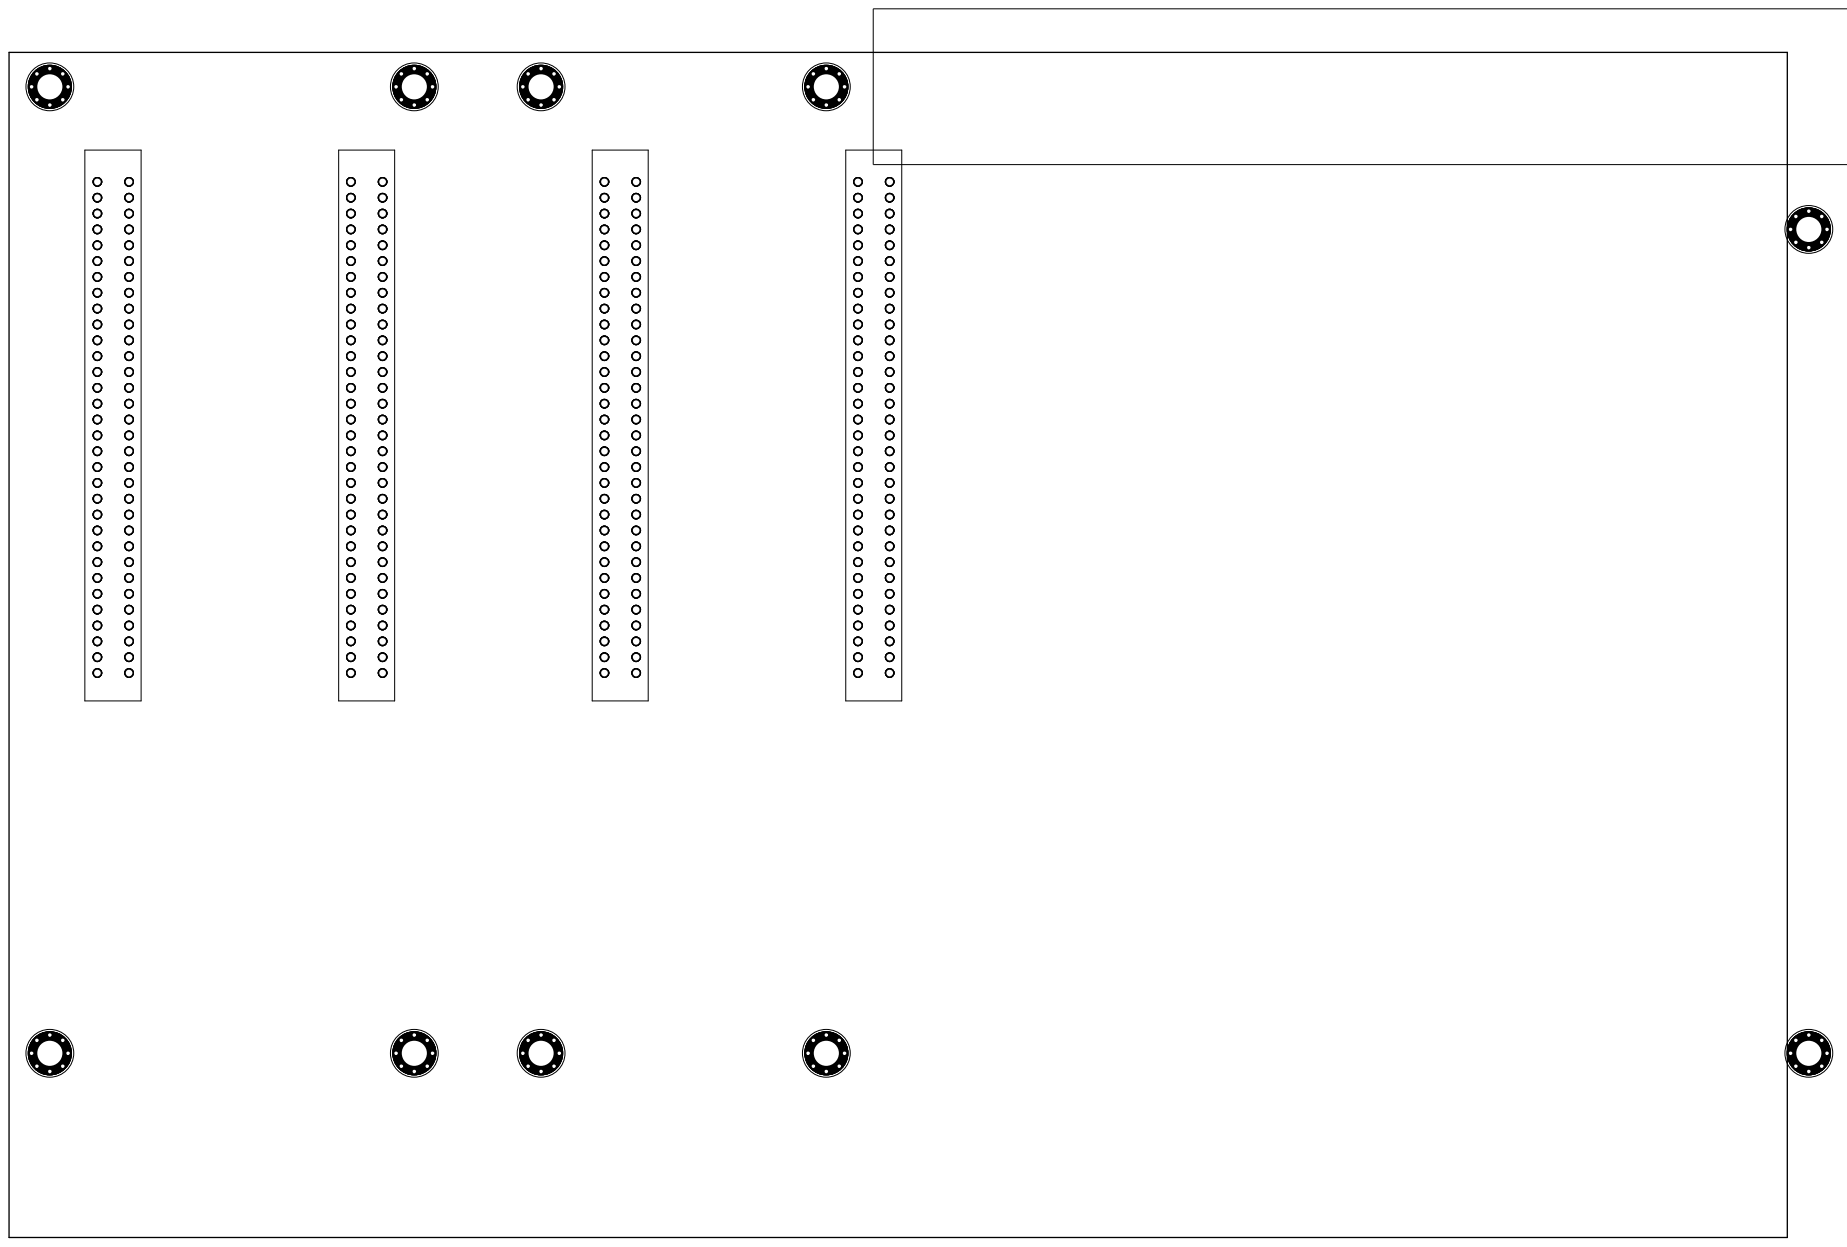
[picture p65: page 1]
